xcl666/trackpoint-mechanical-keyboard/PCB/3x10/3D/误差/IMG_2119.JPG

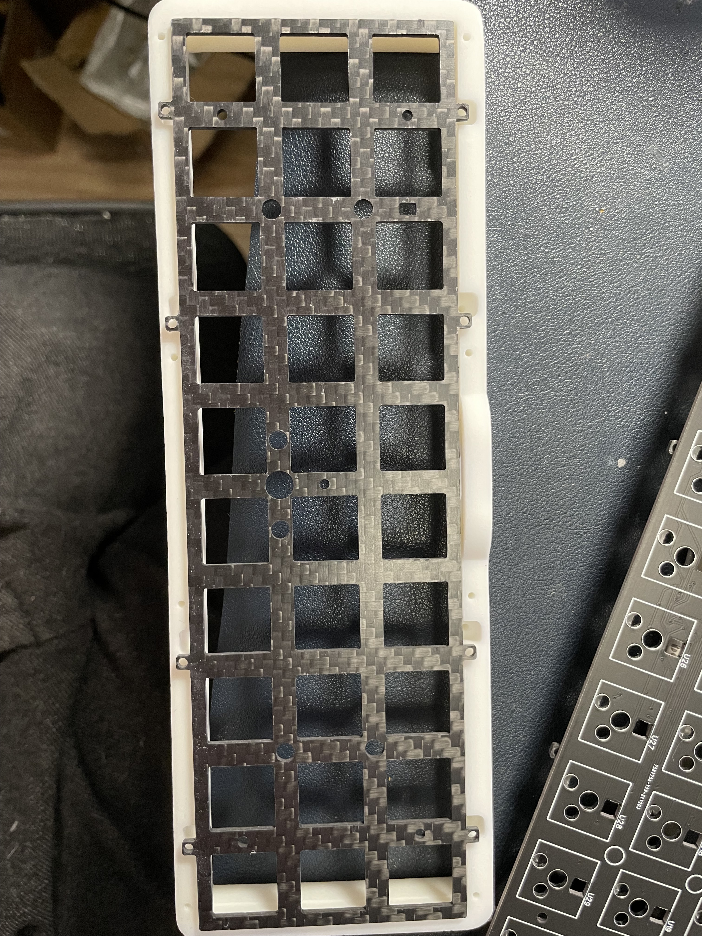
PCB/3x10/3D/误差/IMG_2119.JPG
