xcl666/trackpoint-mechanical-keyboard/PCB/3x10/3D/误差/QQ图片20211208211826.png

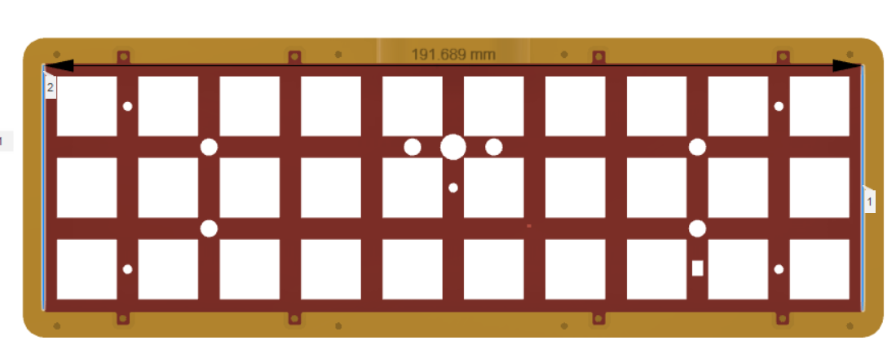
PCB/3x10/3D/误差/QQ图片20211208211826.png
