xcl666/trackpoint-mechanical-keyboard/PCB/3x10/pic/Fo7JxUKhkw28jX1DG1f_OKitPLBH.png

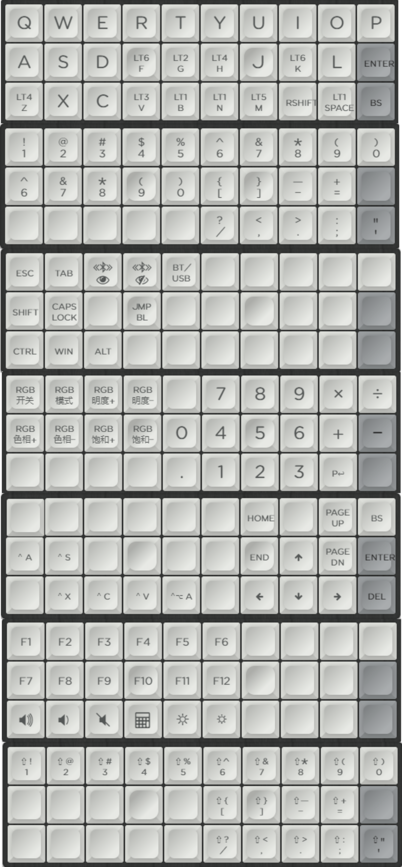
PCB/3x10/pic/Fo7JxUKhkw28jX1DG1f_OKitPLBH.png
