xcl666/trackpoint-mechanical-keyboard/PCB/3x10/pic/IMG_1978(20211202-105650).JPG

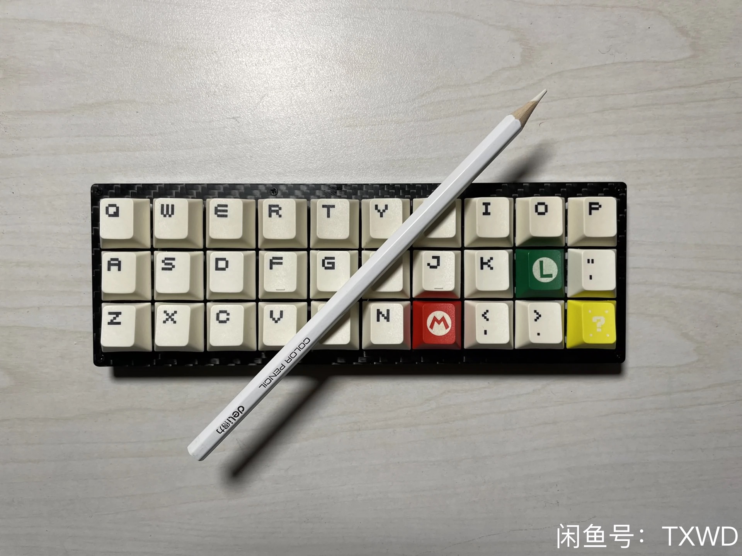
PCB/3x10/pic/IMG_1978(20211202-105650).JPG
