xcl666/trackpoint-mechanical-keyboard/PCB/3x10/pic/IMG_1979(20211202-105653).JPG

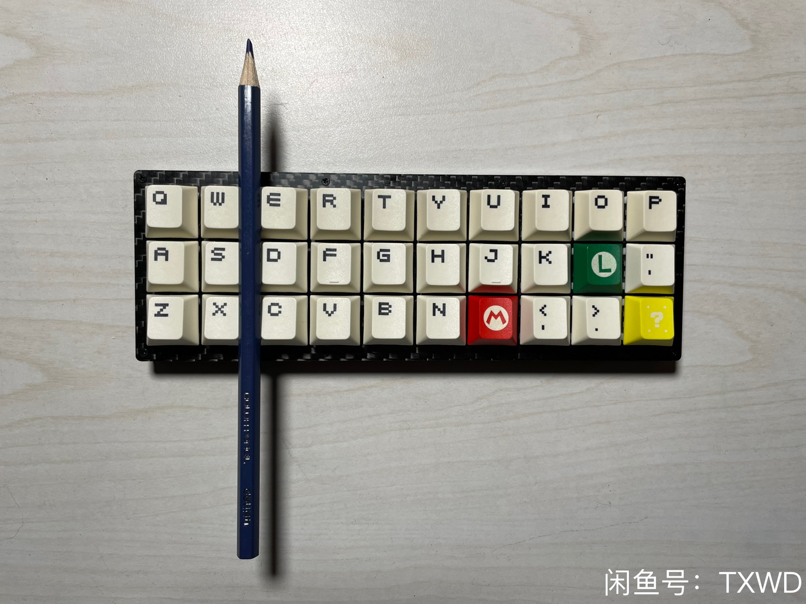
PCB/3x10/pic/IMG_1979(20211202-105653).JPG
