xcl666/trackpoint-mechanical-keyboard/PCB/3x10/pic/IMG_1980(20211202-105657).JPG

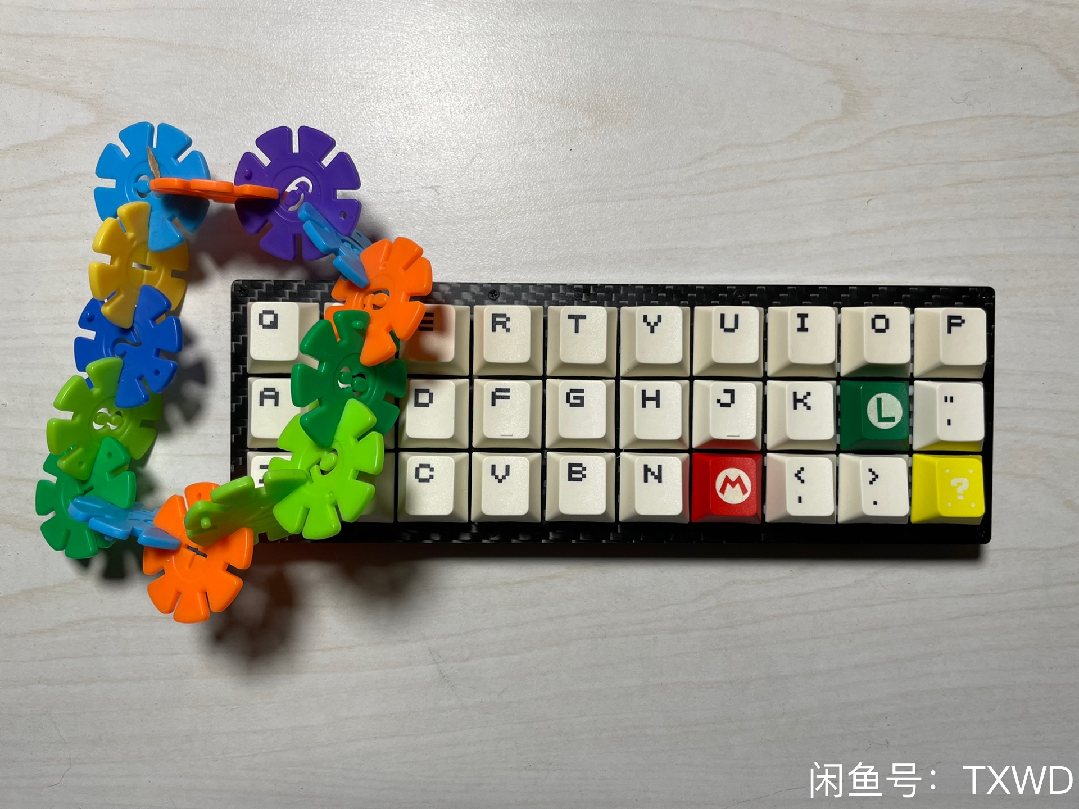
PCB/3x10/pic/IMG_1980(20211202-105657).JPG
