xcl666/trackpoint-mechanical-keyboard/PCB/3x10/pic/IMG_1981(20211202-105700).JPG

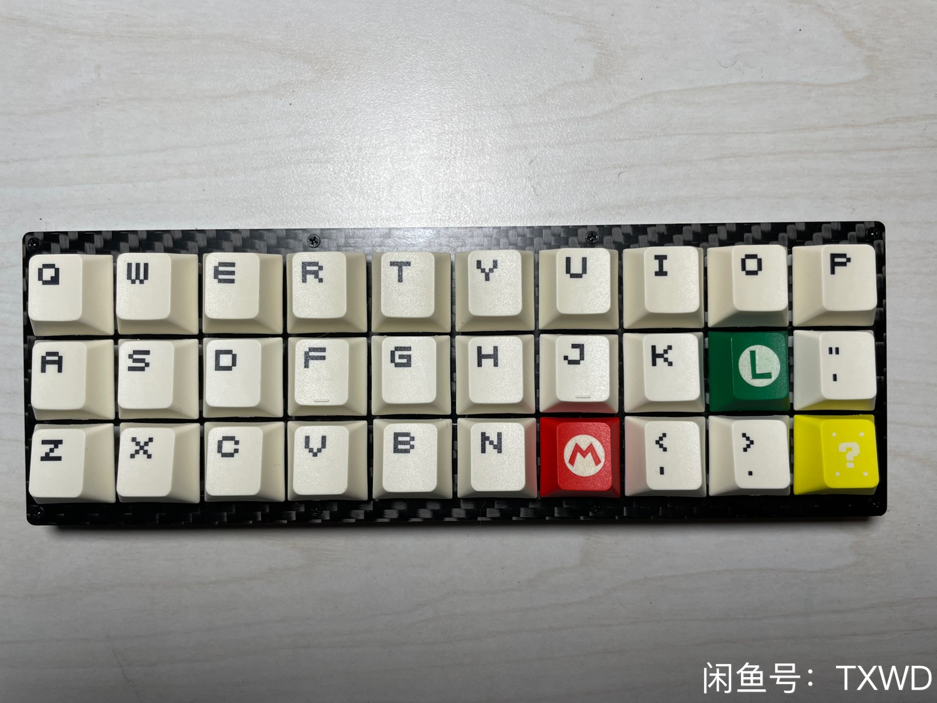
PCB/3x10/pic/IMG_1981(20211202-105700).JPG
