xcl666/trackpoint-mechanical-keyboard/PCB/3x10/pic/IMG_1982(20211202-105706).JPG

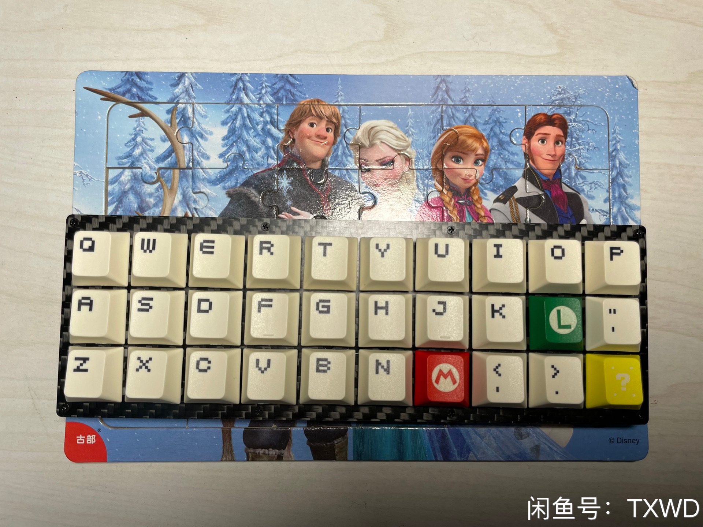
PCB/3x10/pic/IMG_1982(20211202-105706).JPG
