xcl666/trackpoint-mechanical-keyboard/PCB/3x10/pic/IMG_1983(20211202-105742).JPG

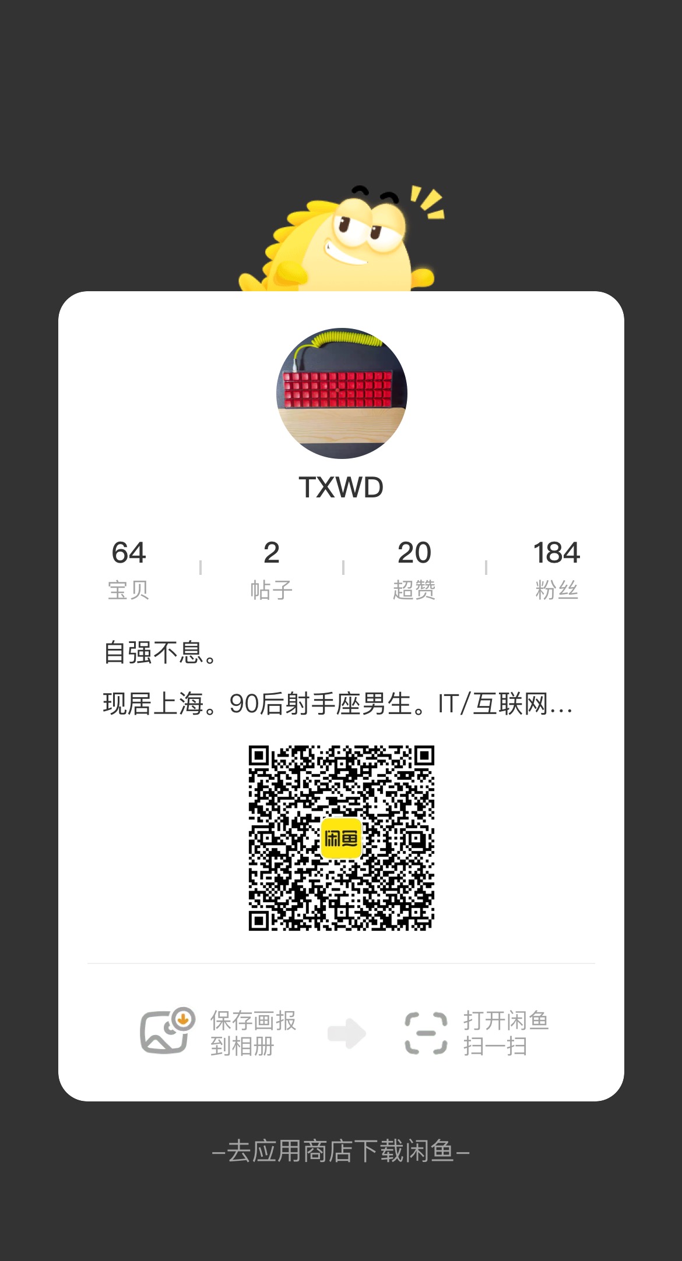
PCB/3x10/pic/IMG_1983(20211202-105742).JPG
