xcl666/trackpoint-mechanical-keyboard/PCB/3x10/QQ图片20211215133456.png

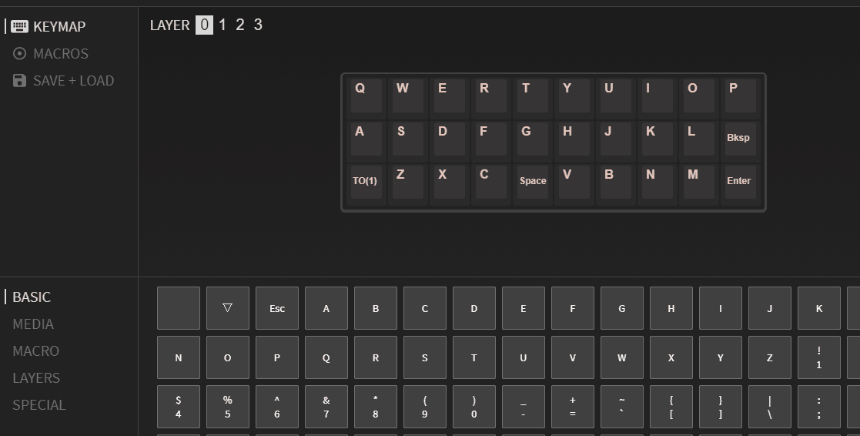
PCB/3x10/QQ图片20211215133456.png
