xcl666/trackpoint-mechanical-keyboard/PCB/4x14/pic/IMG_1932(20211130-000232).JPG

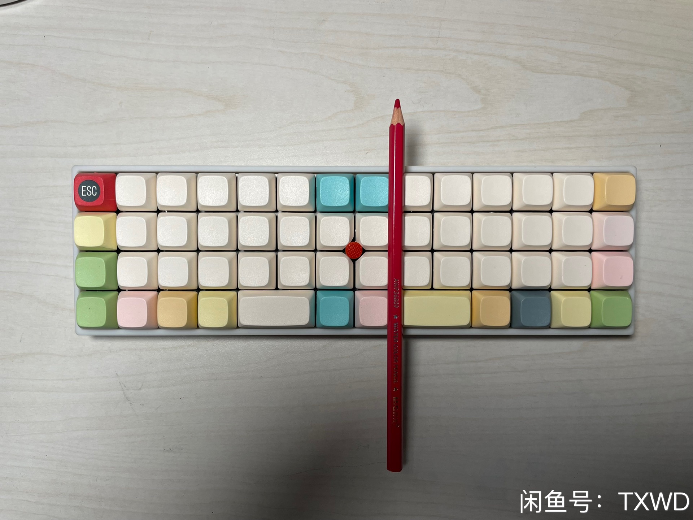
PCB/4x14/pic/IMG_1932(20211130-000232).JPG
