xcl666/trackpoint-mechanical-keyboard/PCB/4x14/pic/IMG_1933(20211130-000236).JPG

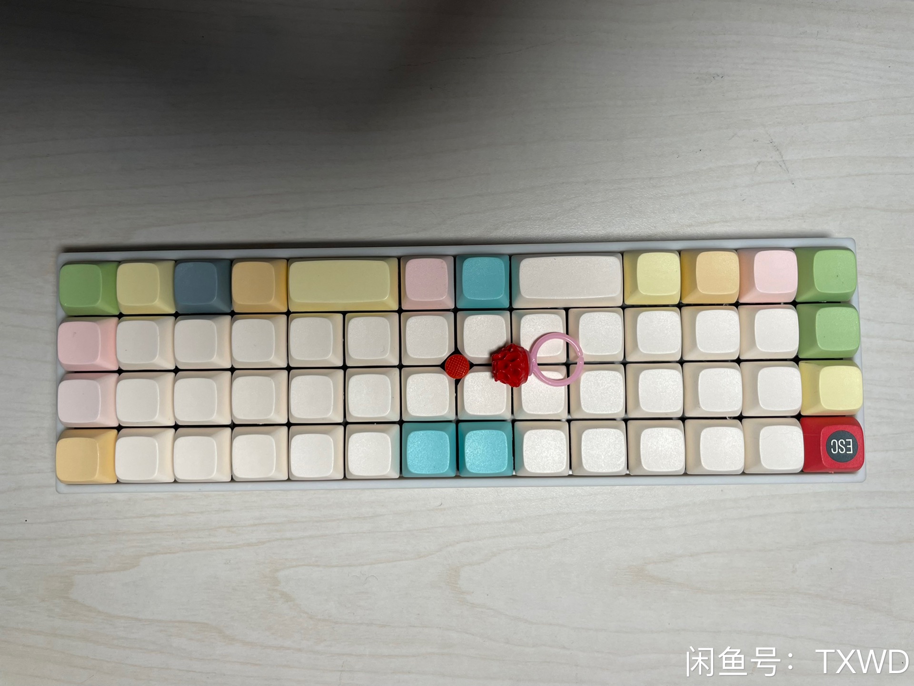
PCB/4x14/pic/IMG_1933(20211130-000236).JPG
