xcl666/trackpoint-mechanical-keyboard/PCB/4x14/pic/IMG_1934(20211130-000239).JPG

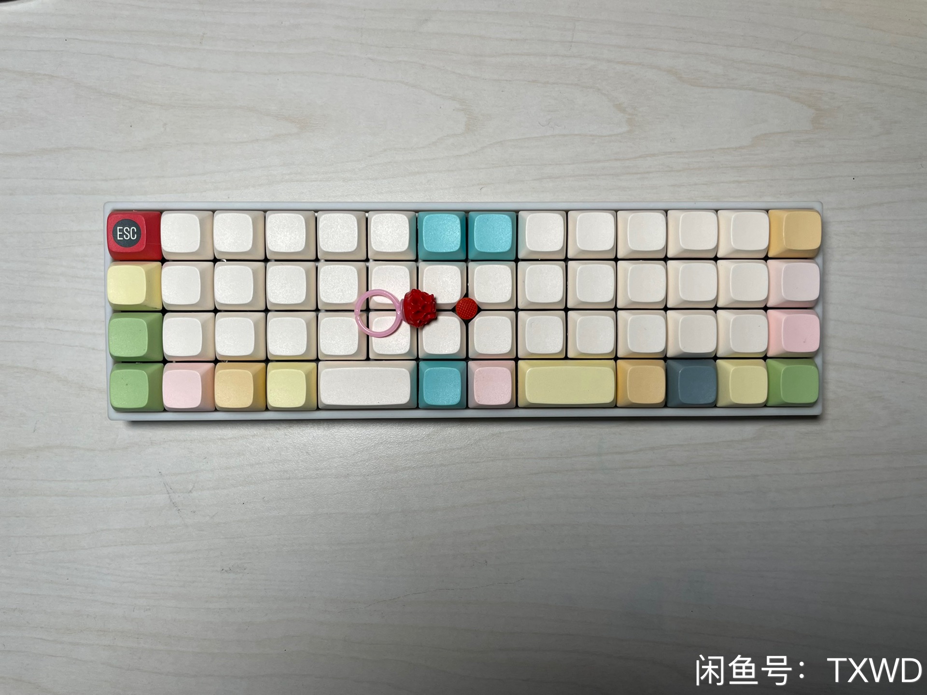
PCB/4x14/pic/IMG_1934(20211130-000239).JPG
