xcl666/trackpoint-mechanical-keyboard/PCB/4x14/pic/IMG_1935(20211130-000242).JPG

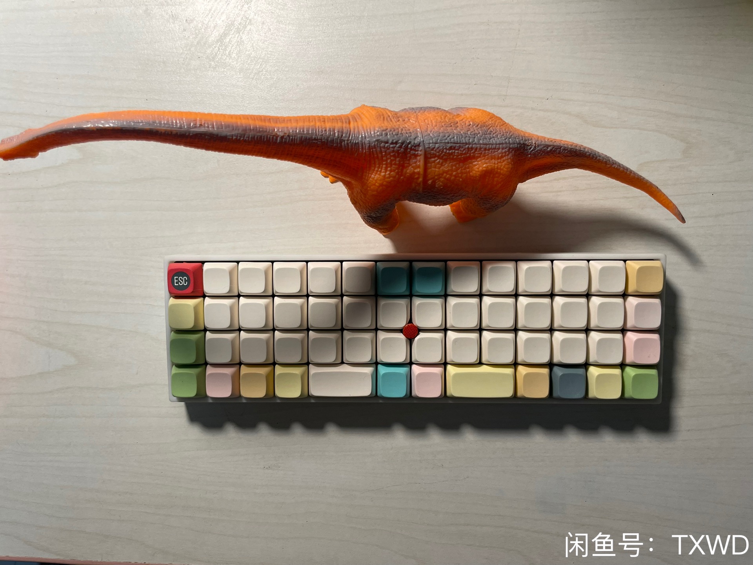
PCB/4x14/pic/IMG_1935(20211130-000242).JPG
