xcl666/trackpoint-mechanical-keyboard/PCB/4x14/pic/IMG_1936(20211130-000251).JPG

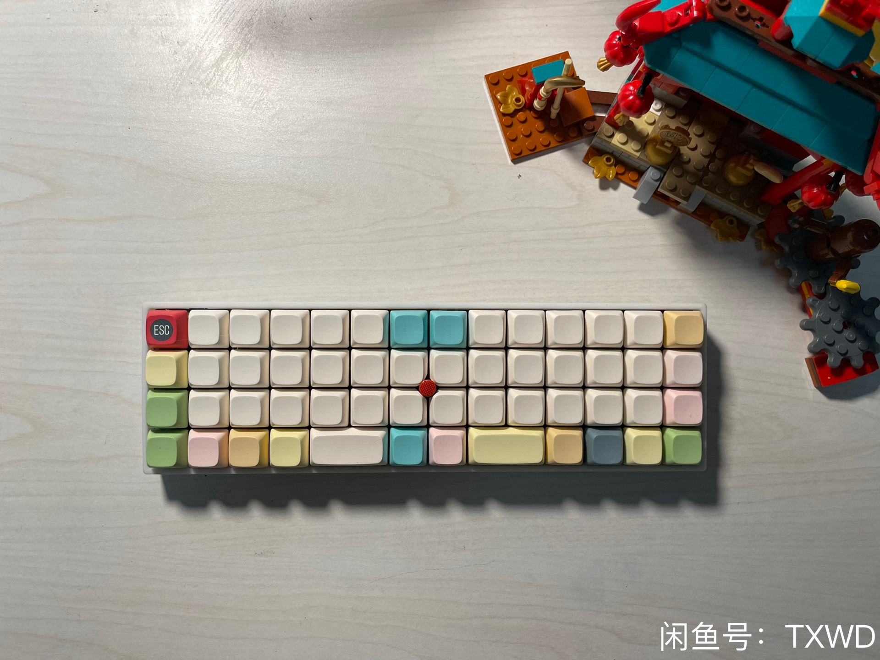
PCB/4x14/pic/IMG_1936(20211130-000251).JPG
