xcl666/trackpoint-mechanical-keyboard/PCB/4x14/pic/IMG_1937(20211130-000254).JPG

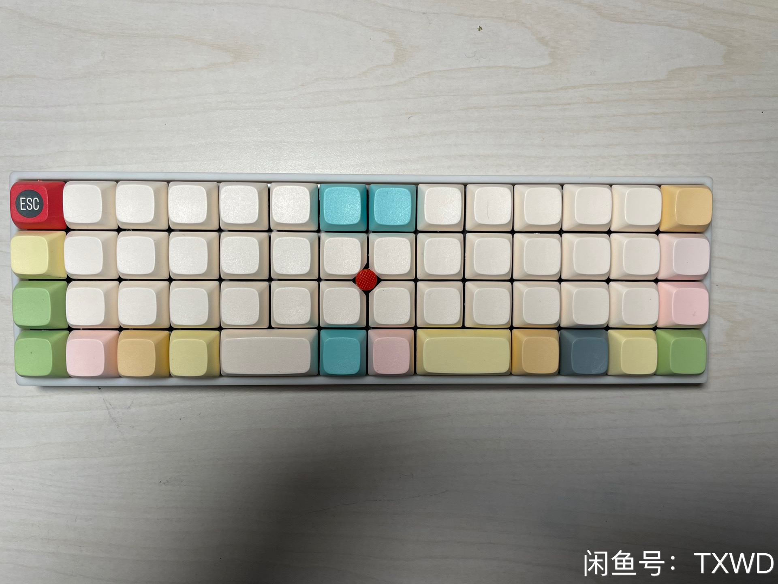
PCB/4x14/pic/IMG_1937(20211130-000254).JPG
