xcl666/trackpoint-mechanical-keyboard/PCB/4x14/pic/IMG_1938(20211130-000258).JPG

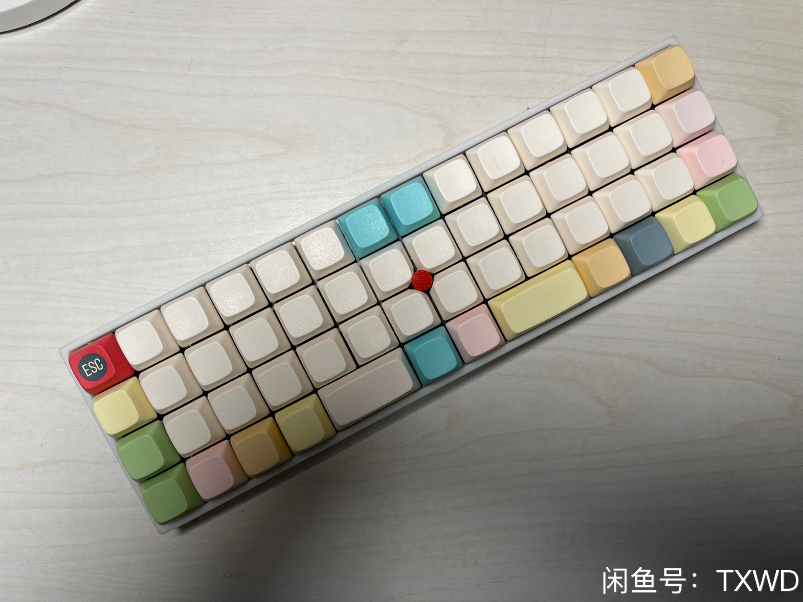
PCB/4x14/pic/IMG_1938(20211130-000258).JPG
