xcl666/trackpoint-mechanical-keyboard/PCB/4x14/pic/IMG_1939(20211130-000301).JPG

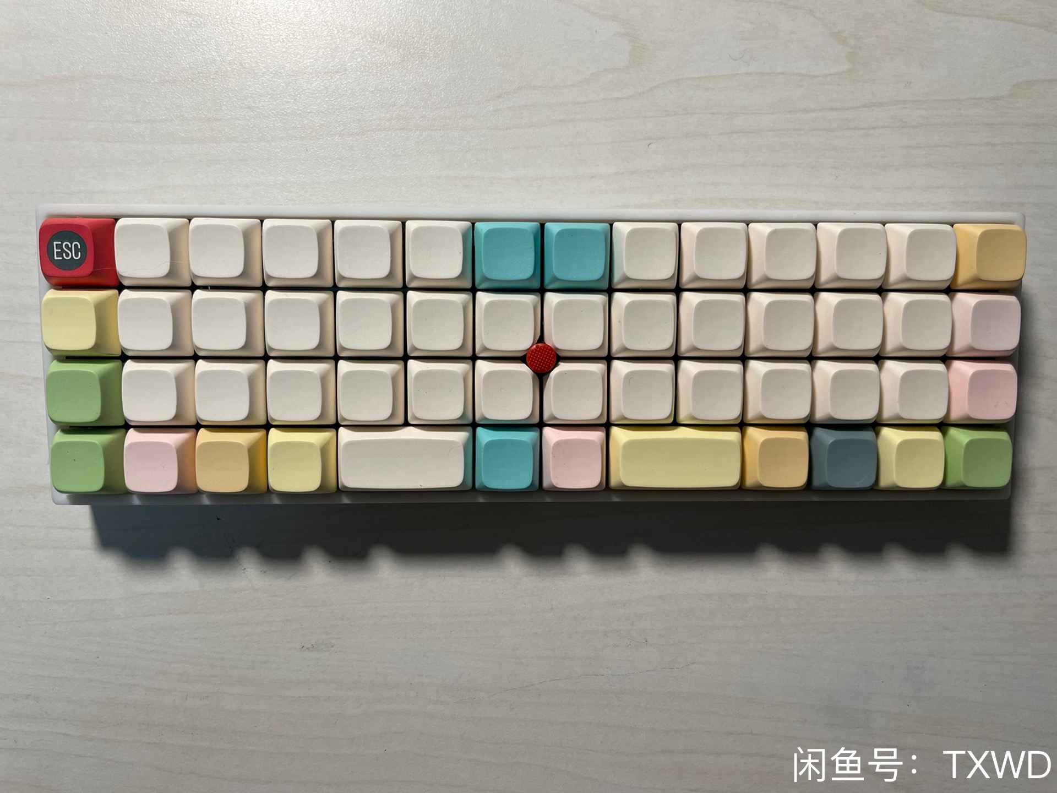
PCB/4x14/pic/IMG_1939(20211130-000301).JPG
