xcl666/trackpoint-mechanical-keyboard/PCB/alice/3D/myown/WeChat Image_20220102115507.png

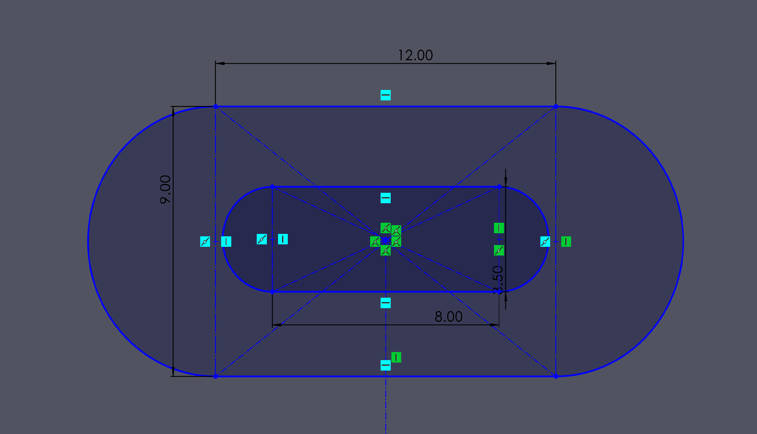
PCB/alice/3D/myown/WeChat Image_20220102115507.png
