xcl666/trackpoint-mechanical-keyboard/PCB/alice/60alicetp.png

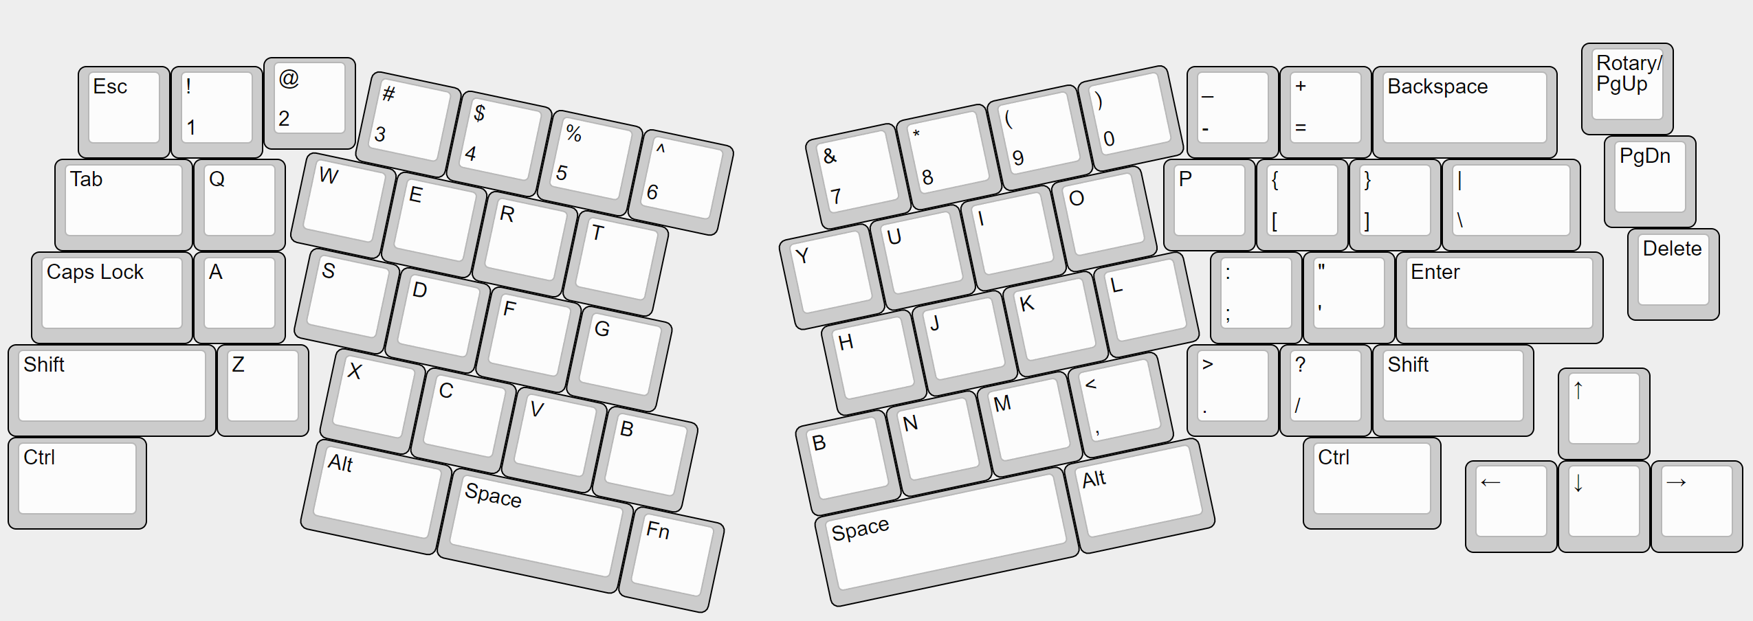
PCB/alice/60alicetp.png
