xcl666/trackpoint-mechanical-keyboard/PCB/alice/70alicetp.png

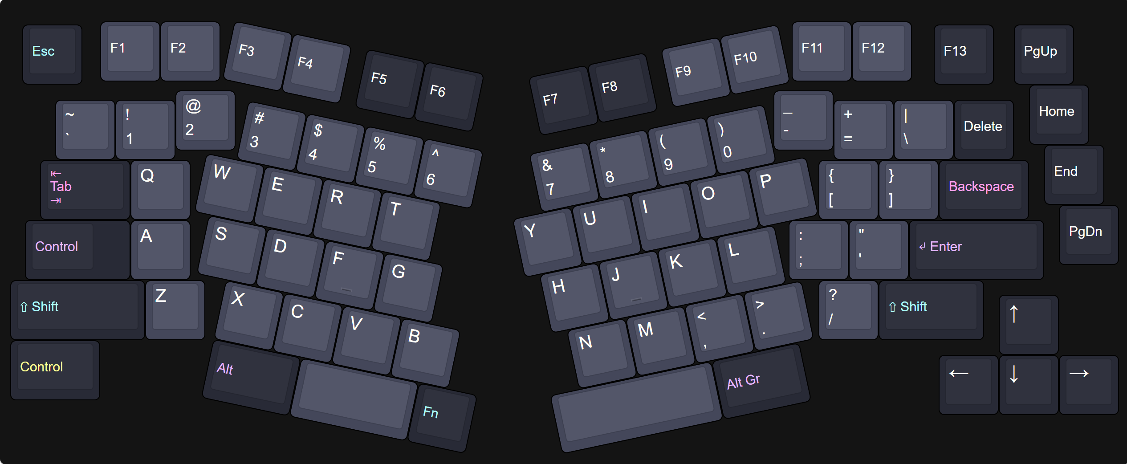
PCB/alice/70alicetp.png
