xcl666/trackpoint-mechanical-keyboard/PCB/alice/Fm2w5G8_fELwdBUXXY6CFaClQVQb.png

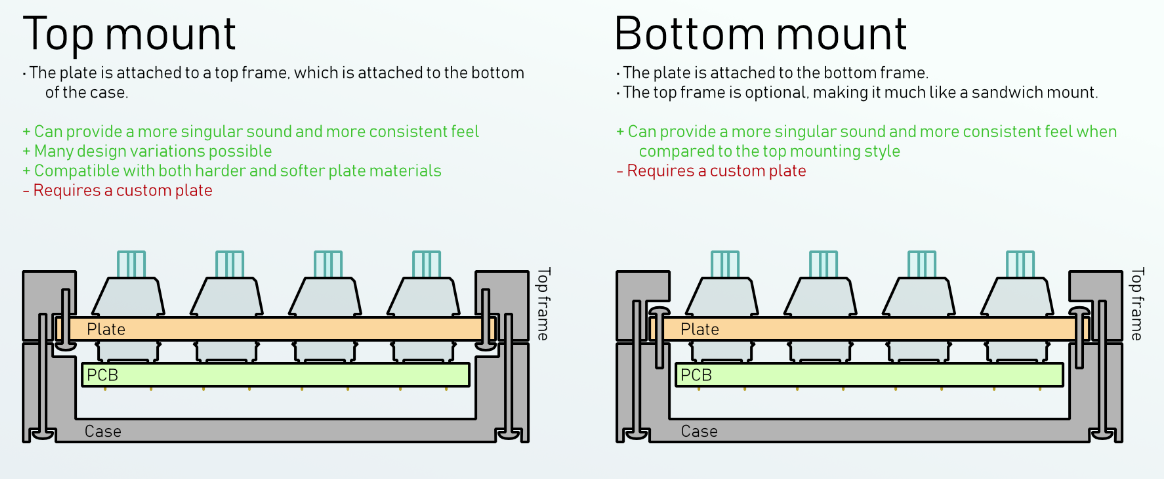
PCB/alice/Fm2w5G8_fELwdBUXXY6CFaClQVQb.png
