xcl666/trackpoint-mechanical-keyboard/PCB/alice/InkedQQ图片20211125203827.jpg

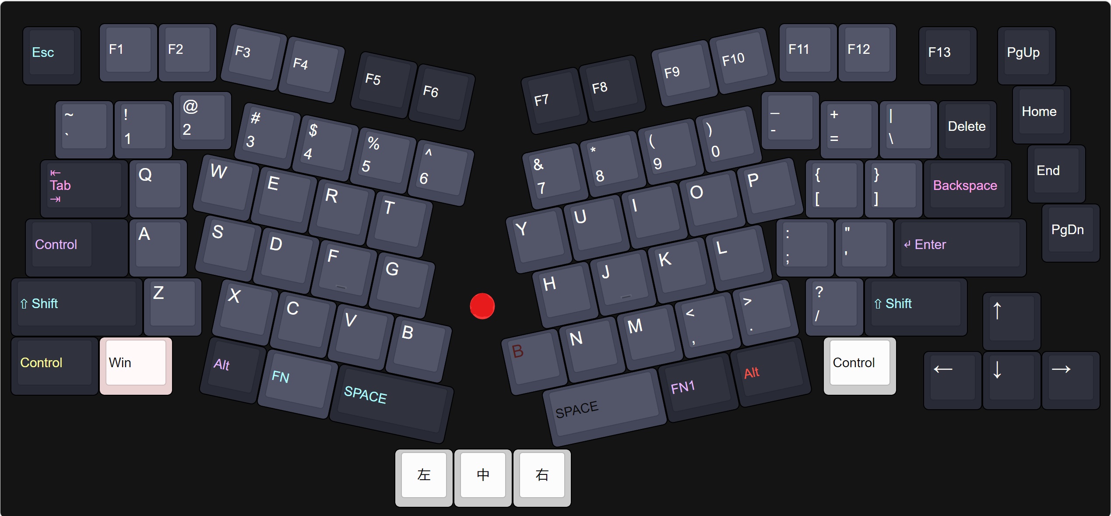
PCB/alice/InkedQQ图片20211125203827.jpg
