xcl666/trackpoint-mechanical-keyboard/PCB/alice/lastAlice.png

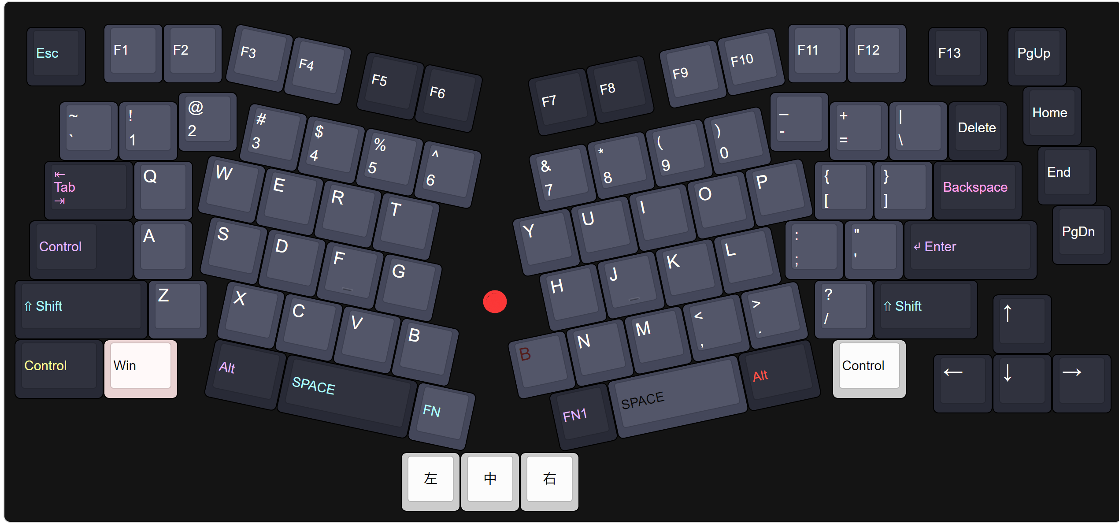
PCB/alice/lastAlice.png
