xcl666/trackpoint-mechanical-keyboard/PCB/alice/QQ图片20211125215850.jpg

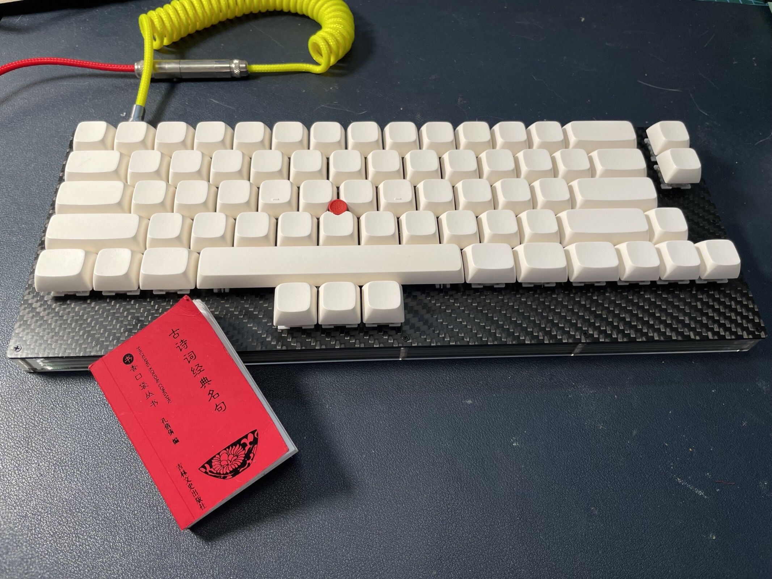
PCB/alice/QQ图片20211125215850.jpg
