xcl666/trackpoint-mechanical-keyboard/PCB/alice/QQ图片20211125220050.png

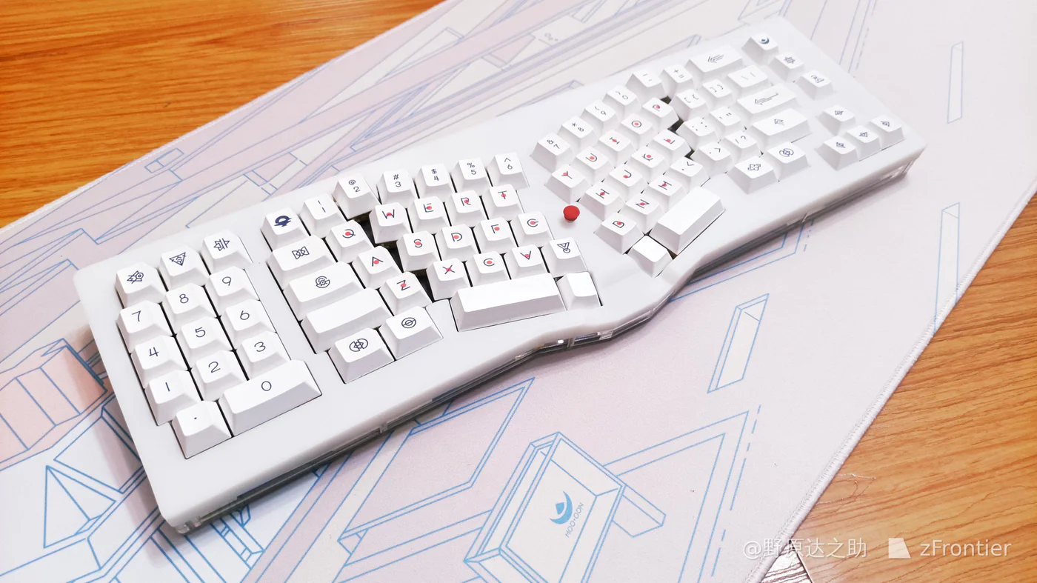
PCB/alice/QQ图片20211125220050.png
