xcl666/trackpoint-mechanical-keyboard/PCB/alice/QQ图片20211127194925.jpg

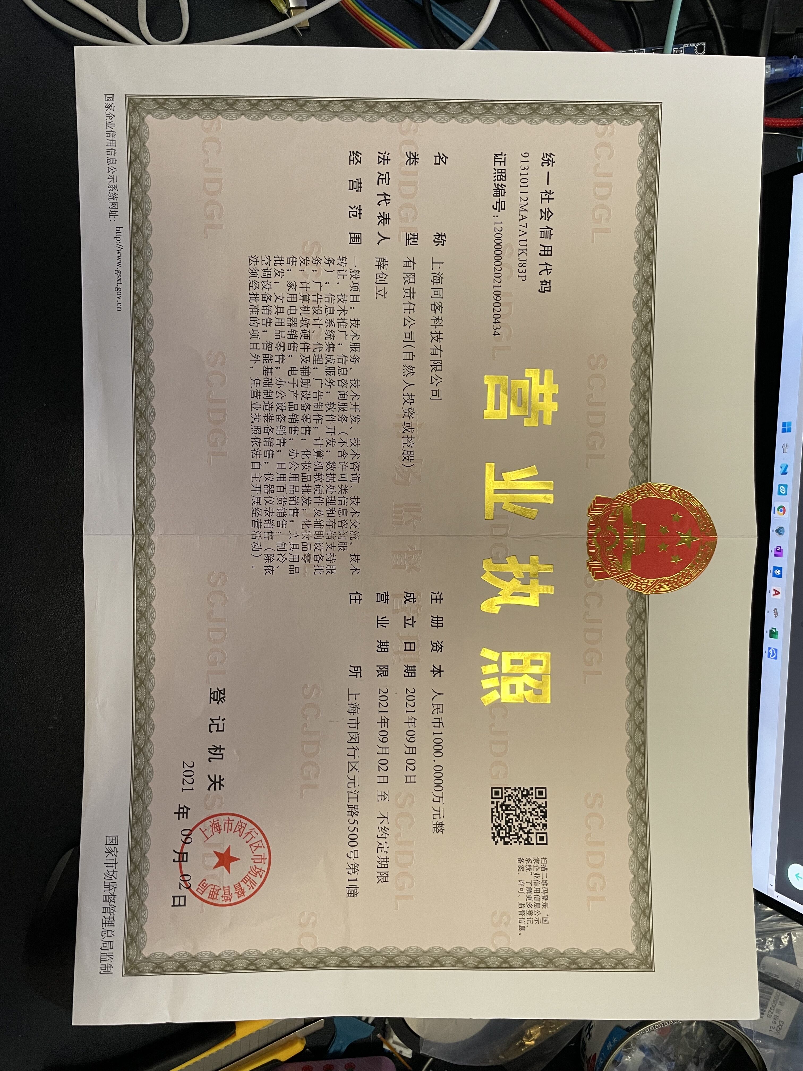
PCB/alice/QQ图片20211127194925.jpg
