xcl666/trackpoint-mechanical-keyboard/PCB/alice/QQ图片20211215164015.jpg

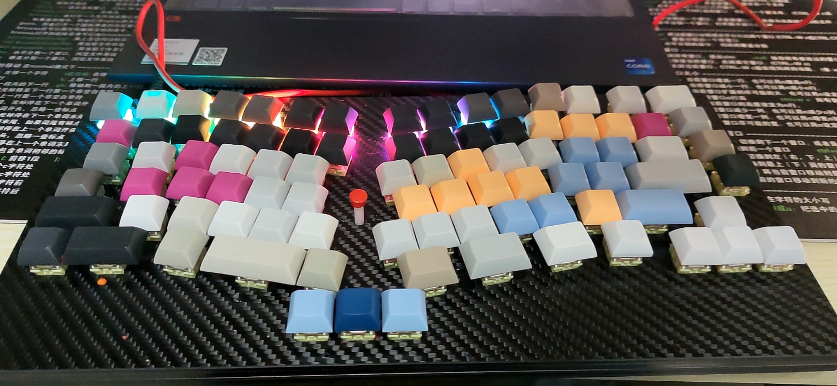
PCB/alice/QQ图片20211215164015.jpg
