xcl666/trackpoint-mechanical-keyboard/PCB/alice/WeChat Image_20211124023521.png

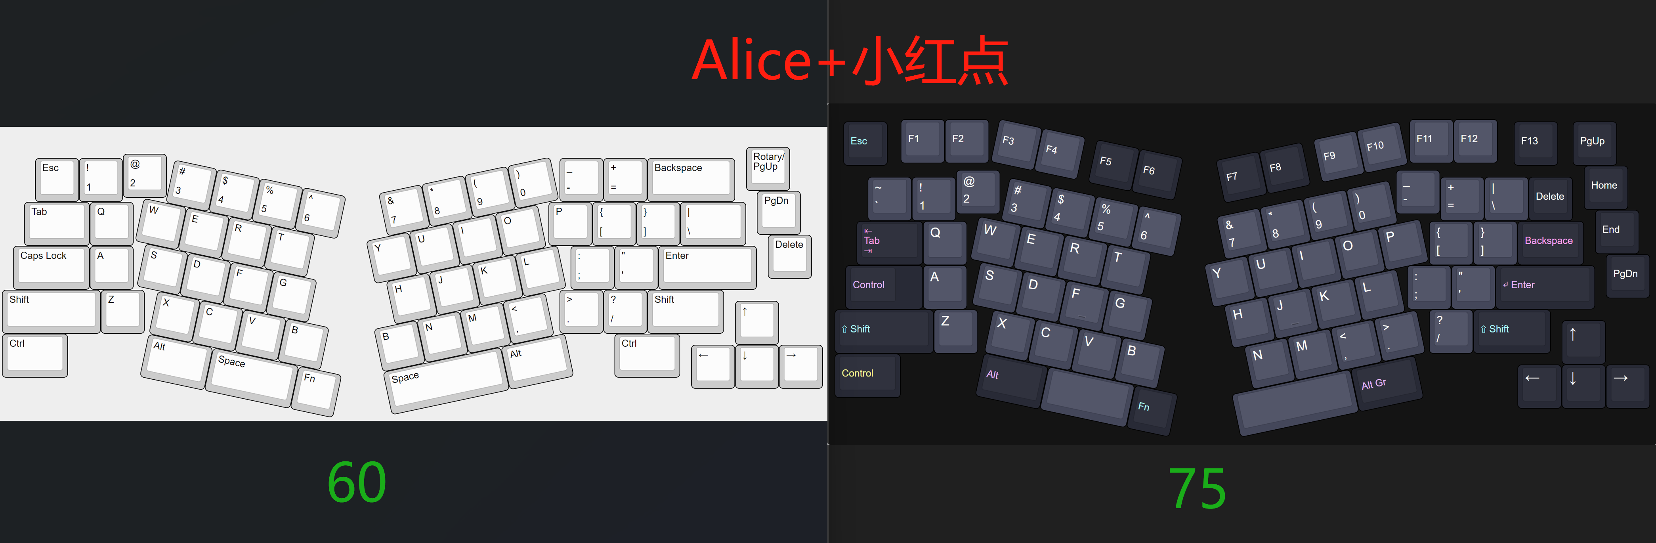
PCB/alice/WeChat Image_20211124023521.png
