xcl666/trackpoint-mechanical-keyboard/PCB/alice/WeChat Image_20211125122409.jpg

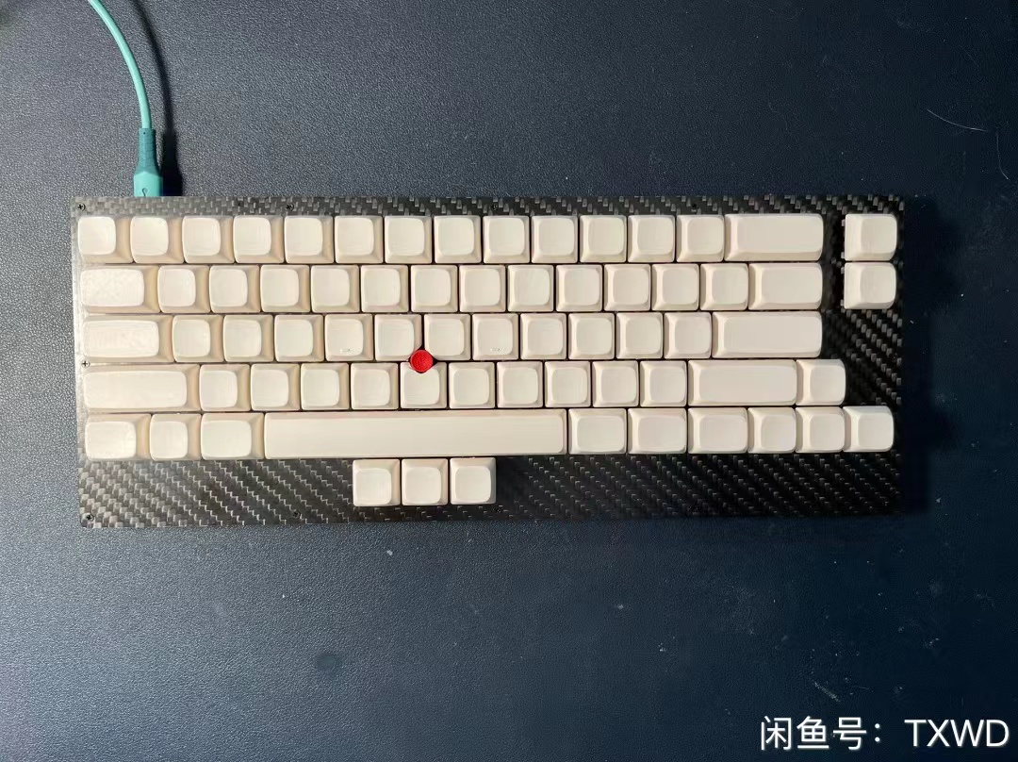
PCB/alice/WeChat Image_20211125122409.jpg
