xcl666/trackpoint-mechanical-keyboard/PCB/alice/WeChat Image_20211211230742.jpg

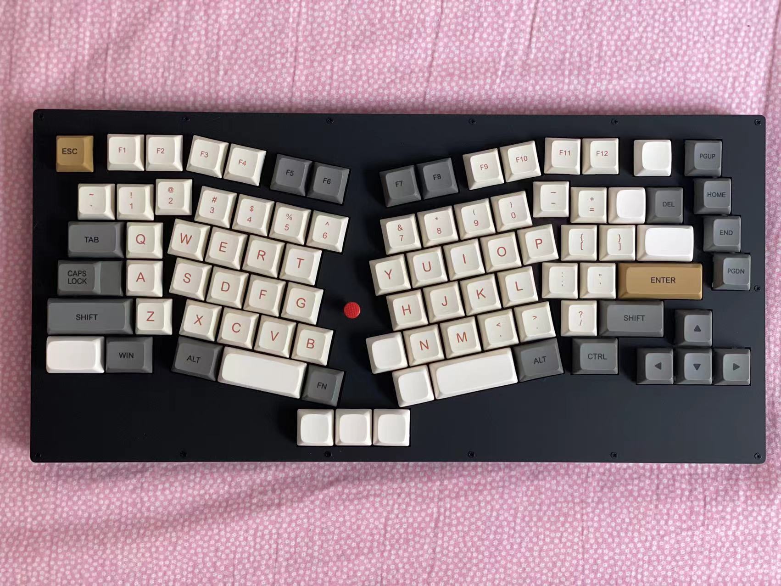
PCB/alice/WeChat Image_20211211230742.jpg
