xcl666/trackpoint-mechanical-keyboard/PCB/alice/选购配件.png

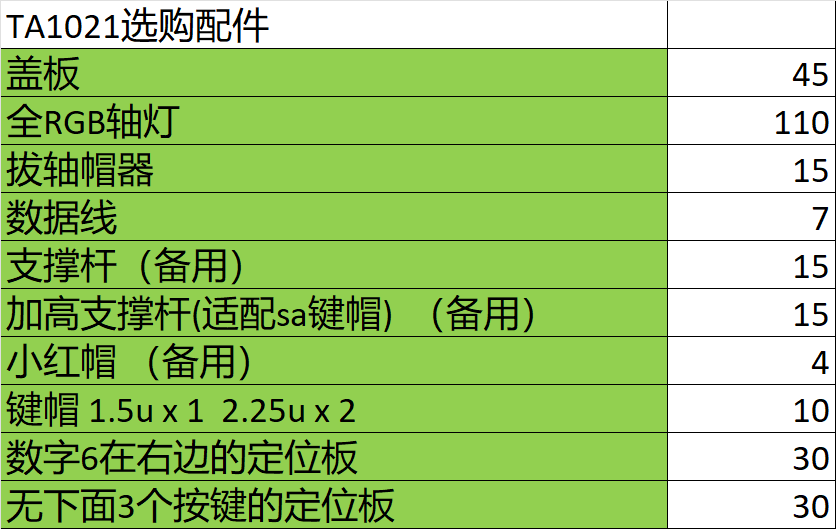
PCB/alice/选购配件.png
