xcl666/trackpoint-mechanical-keyboard/PCB/at90usb646/schematic2pp.png

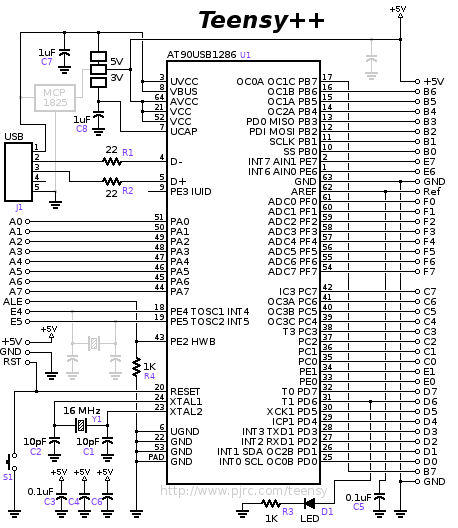
PCB/at90usb646/schematic2pp.png
