xcl666/trackpoint-mechanical-keyboard/PCB/think48/14652E1B-F07E-4A99-99C1-B11ADDA51B1B(1).JPG

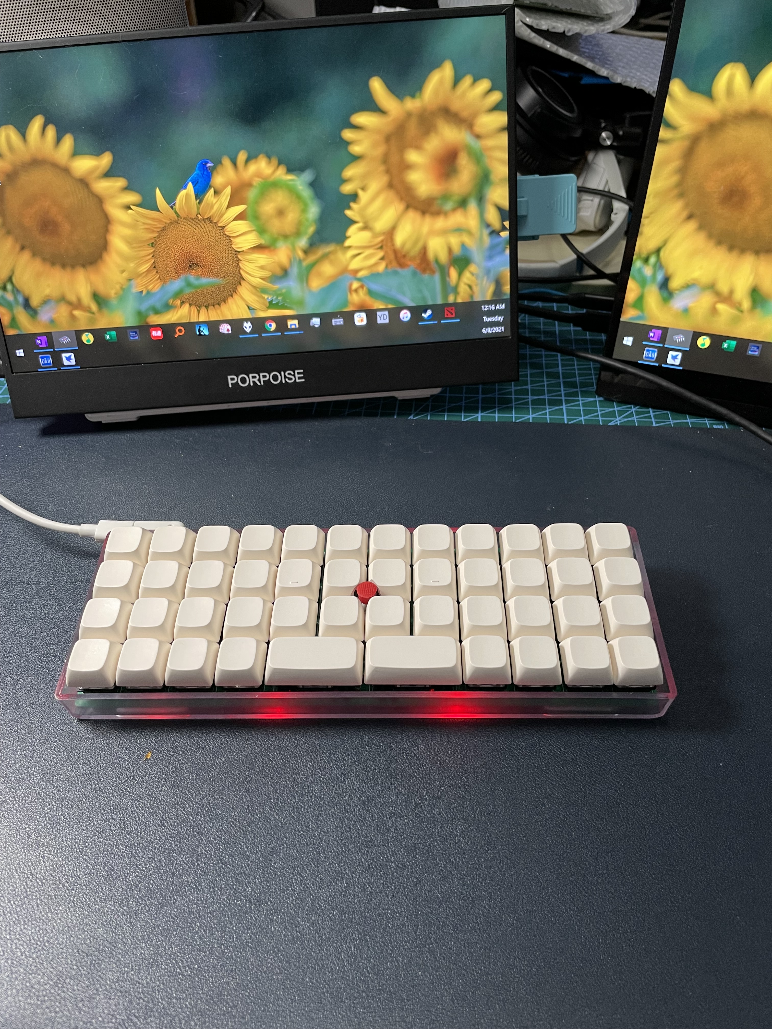
PCB/think48/14652E1B-F07E-4A99-99C1-B11ADDA51B1B(1).JPG
