xcl666/trackpoint-mechanical-keyboard/PCB/think48/EF5D5C7B-043F-4552-9306-83972699D2C9.JPG

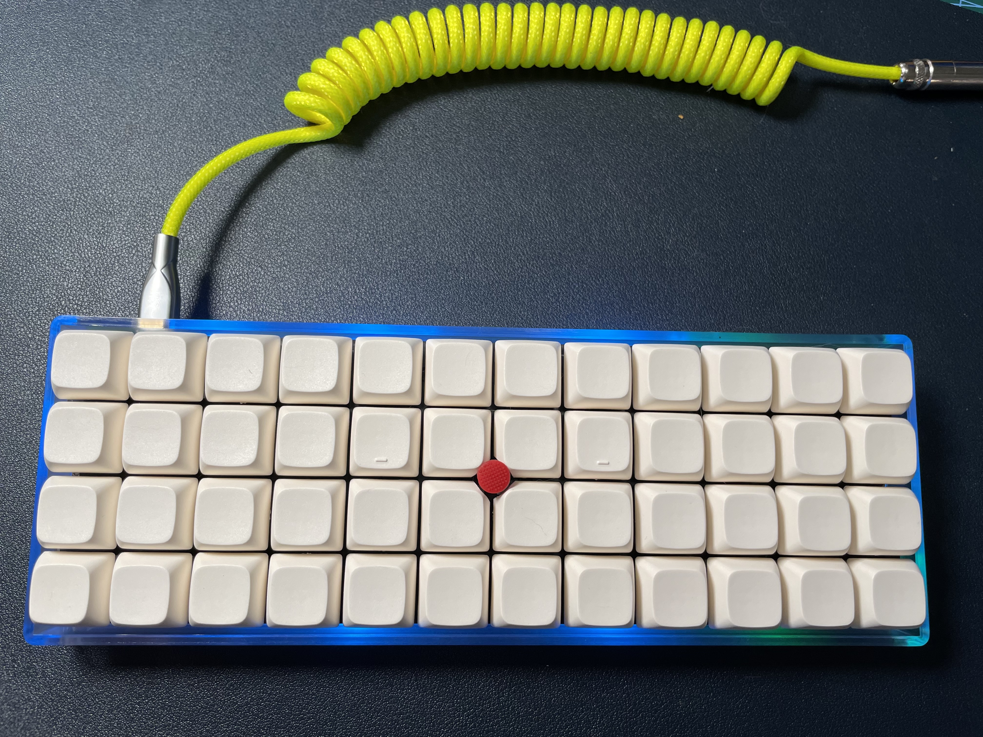
PCB/think48/EF5D5C7B-043F-4552-9306-83972699D2C9.JPG
