xcl666/trackpoint-mechanical-keyboard/PCB/think48/IMG_0189.JPG

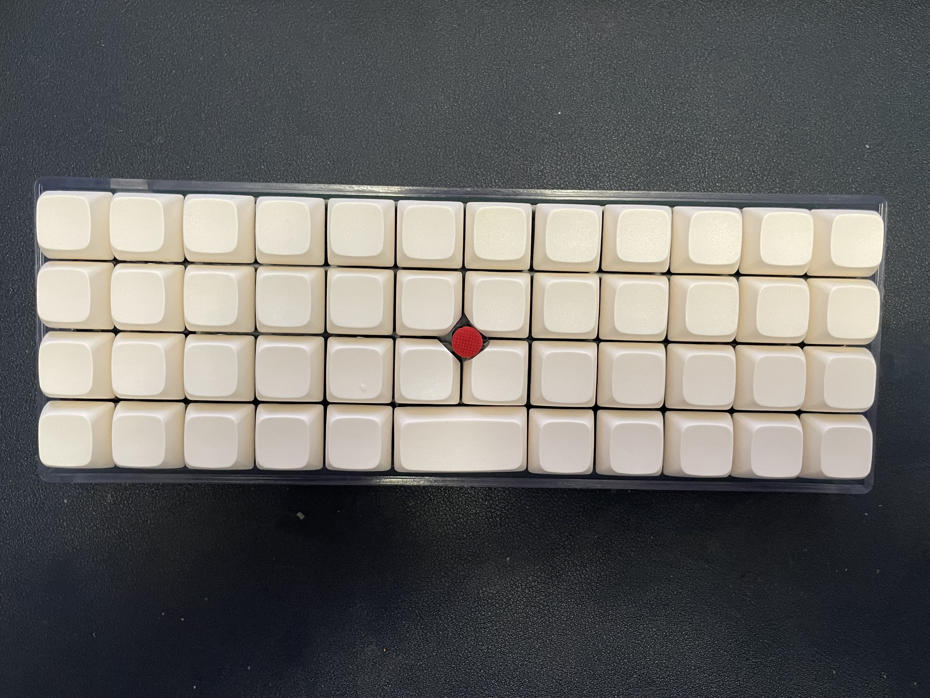
PCB/think48/IMG_0189.JPG
