xcl666/trackpoint-mechanical-keyboard/PCB/think48/IMG_1899(20211126-221744).JPG

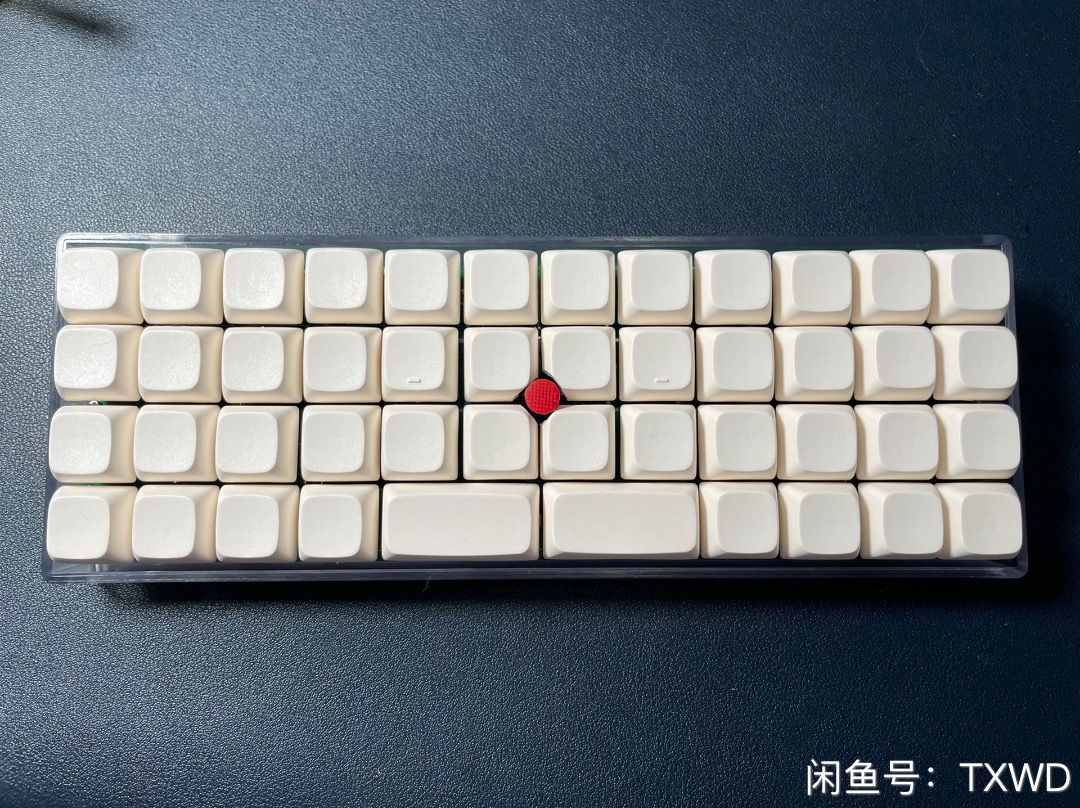
PCB/think48/IMG_1899(20211126-221744).JPG
