xcl666/trackpoint-mechanical-keyboard/PCB/think48/IMG_2052(20220107-030827).JPG

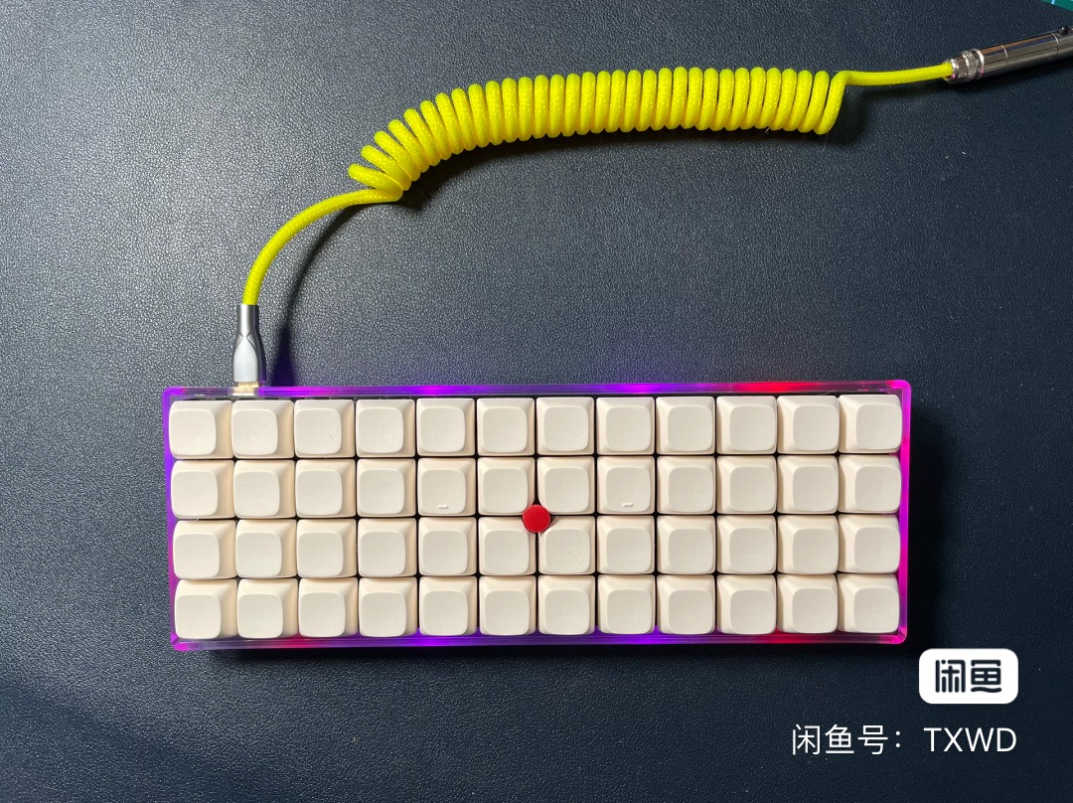
PCB/think48/IMG_2052(20220107-030827).JPG
