xcl666/trackpoint-mechanical-keyboard/PCB/think48/IMG_2998.JPG

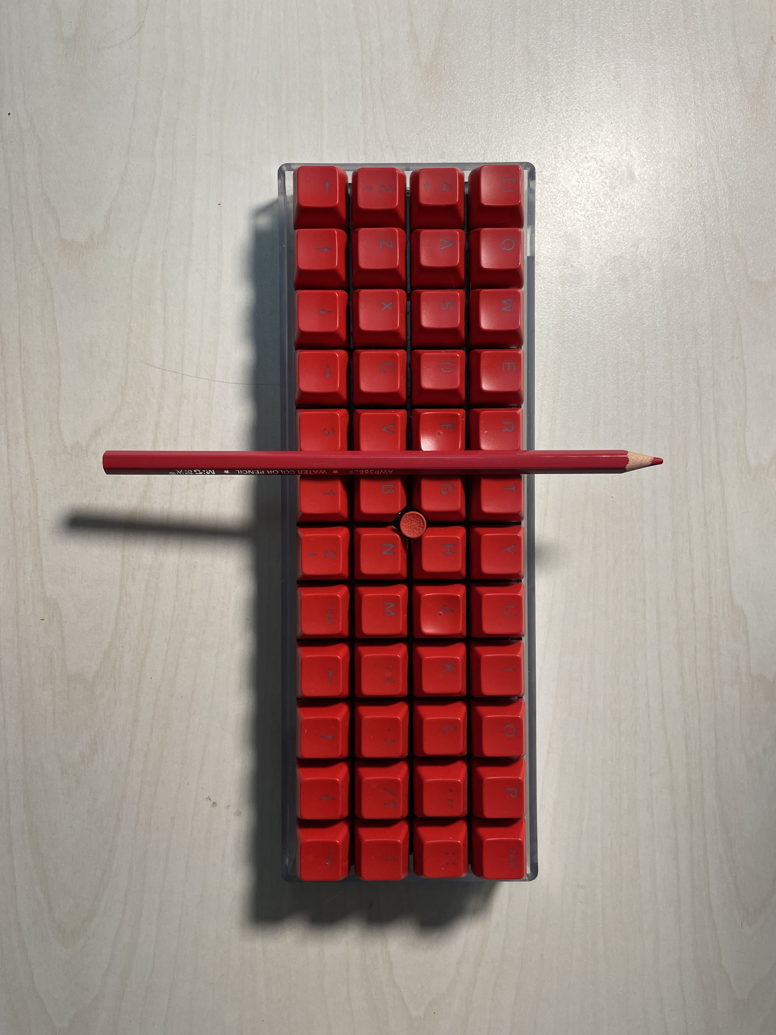
PCB/think48/IMG_2998.JPG
