xcl666/trackpoint-mechanical-keyboard/PCB/think48/new/WeChat Image_20220222152111.jpg

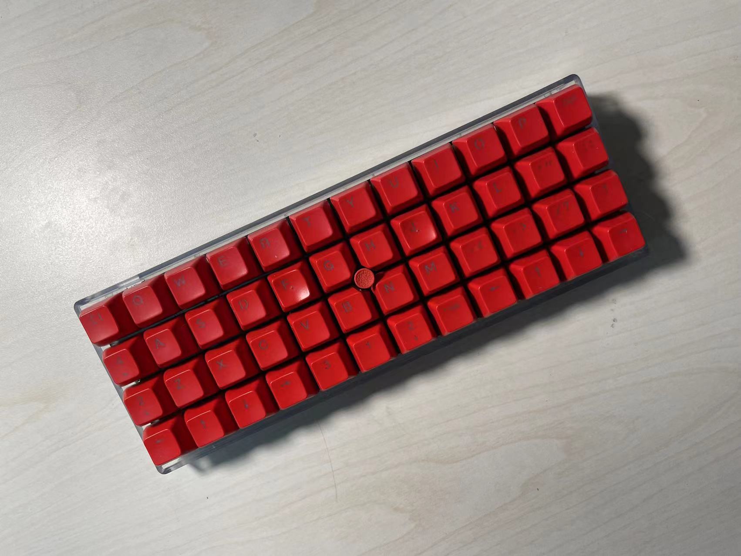
PCB/think48/new/WeChat Image_20220222152111.jpg
