xcl666/trackpoint-mechanical-keyboard/PCB/think48/new/WeChat Image_202202221521092.jpg

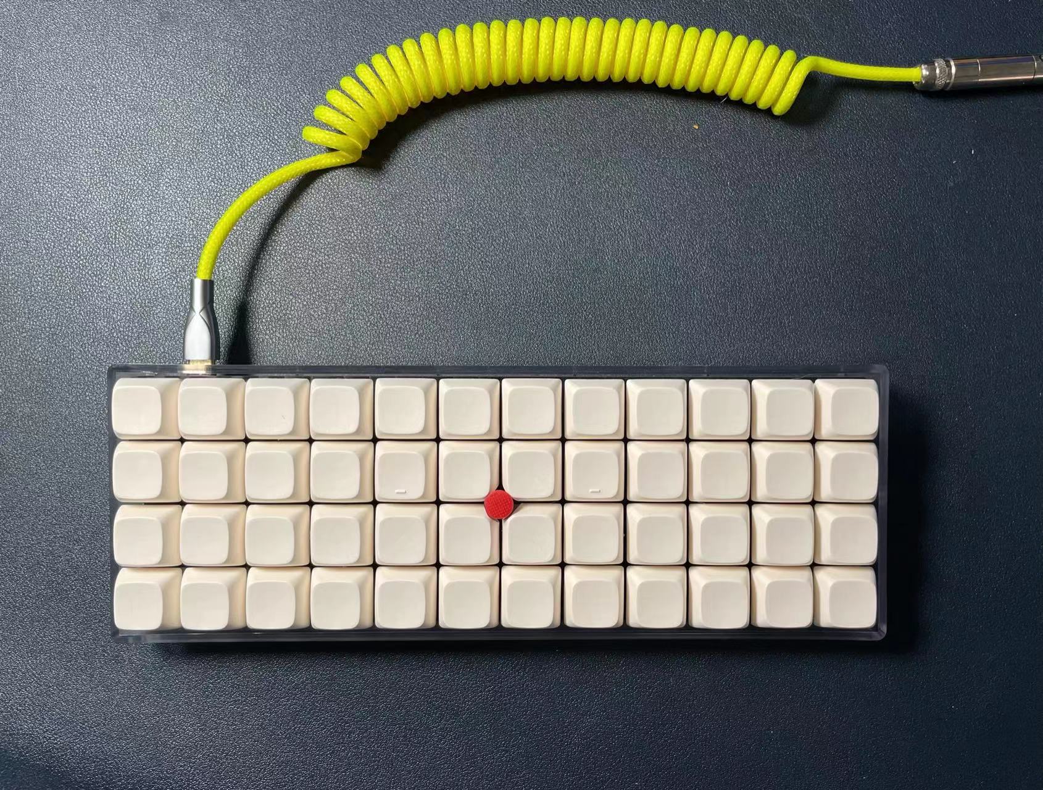
PCB/think48/new/WeChat Image_202202221521092.jpg
