xcl666/trackpoint-mechanical-keyboard/PCB/think48/new/WeChat Image_202202221521093.jpg

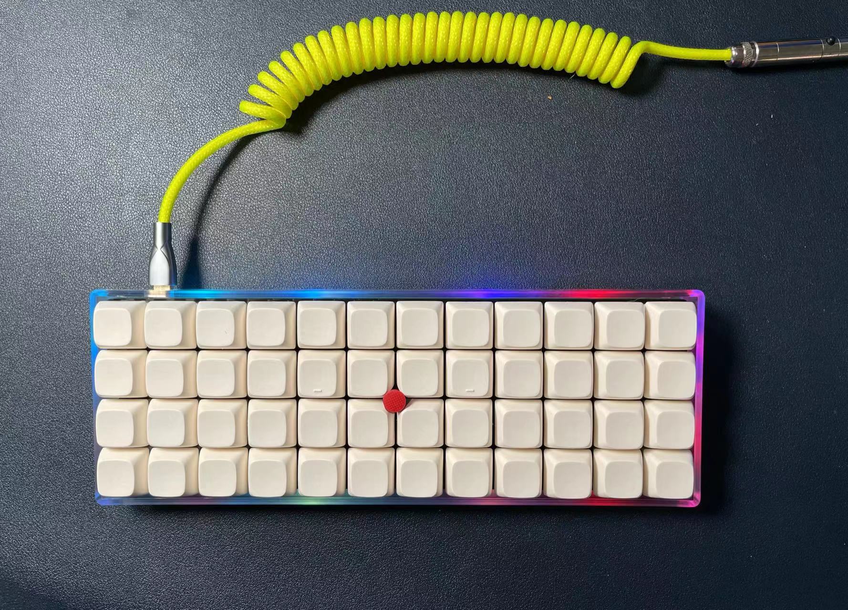
PCB/think48/new/WeChat Image_202202221521093.jpg
