xcl666/trackpoint-mechanical-keyboard/PCB/think48/new/WeChat Image_202202221521102.jpg

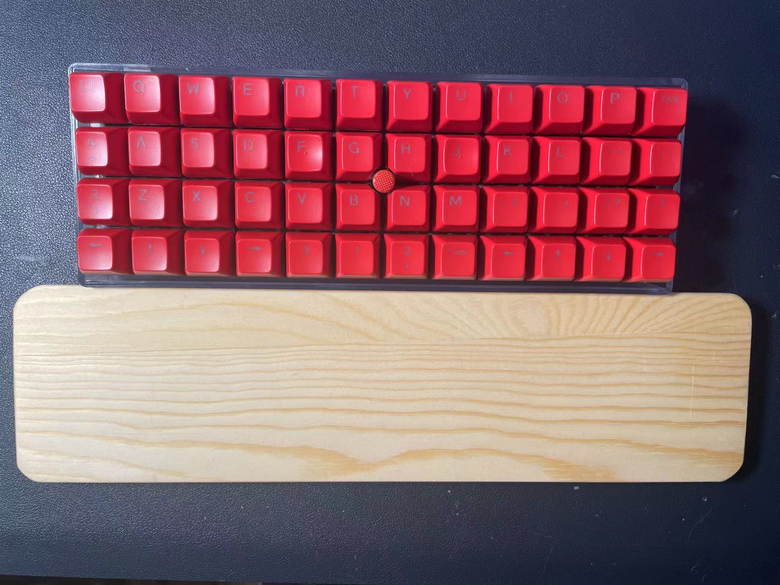
PCB/think48/new/WeChat Image_202202221521102.jpg
