xcl666/trackpoint-mechanical-keyboard/PCB/think48/new/WeChat Image_202202221521111.jpg

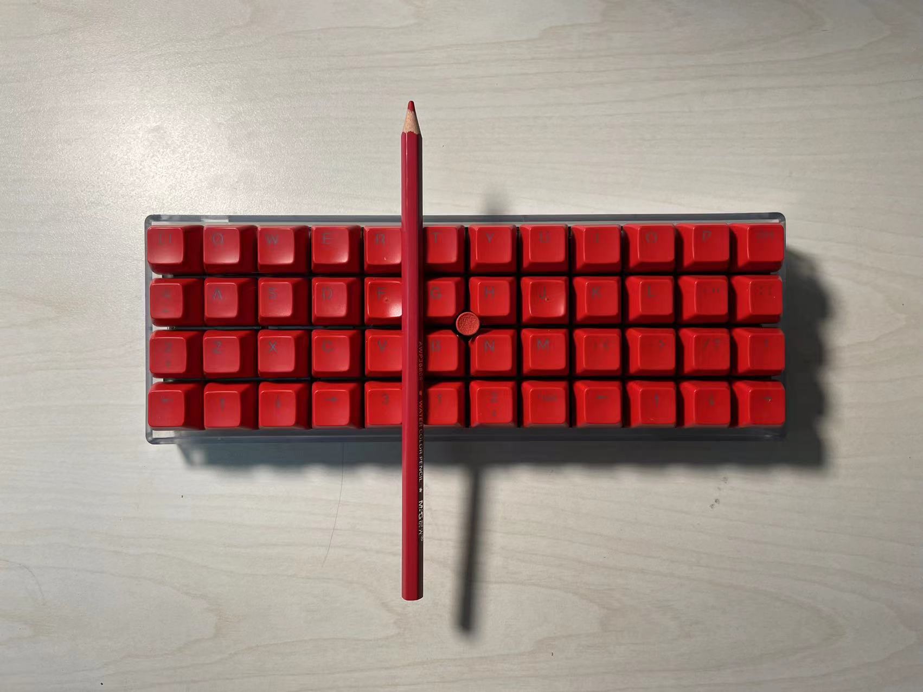
PCB/think48/new/WeChat Image_202202221521111.jpg
