xcl666/trackpoint-mechanical-keyboard/PCB/think84/7月28日开源文件/7月28日开源文件/高清键盘图/computer-1209104_1920.jpg

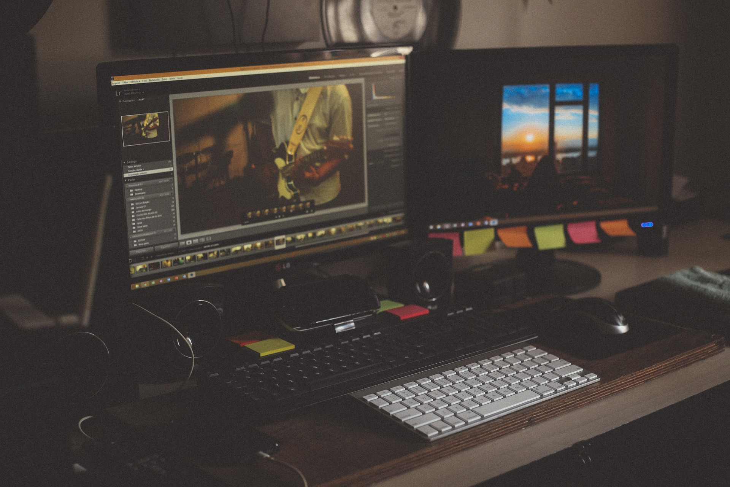
PCB/think84/7月28日开源文件/7月28日开源文件/高清键盘图/computer-1209104_1920.jpg
