xcl666/trackpoint-mechanical-keyboard/PCB/think84/7月28日开源文件/7月28日开源文件/高清键盘图/musical-instrument-1865597_1920.jpg

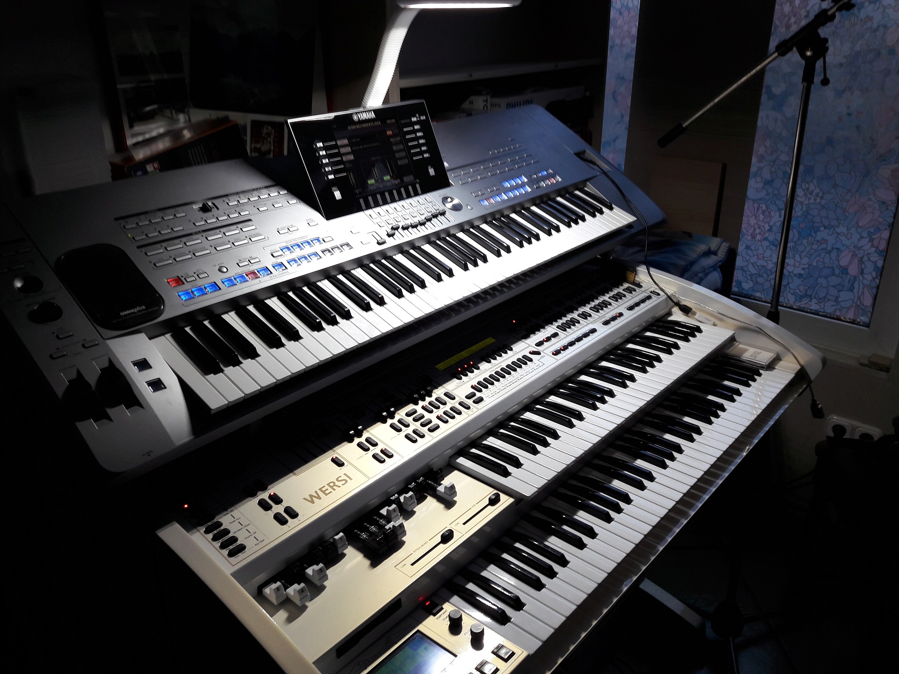
PCB/think84/7月28日开源文件/7月28日开源文件/高清键盘图/musical-instrument-1865597_1920.jpg
