xcl666/trackpoint-mechanical-keyboard/PCB/think84/7月28日开源文件/7月28日开源文件/高清键盘图/typewriter-1138293_1920.png

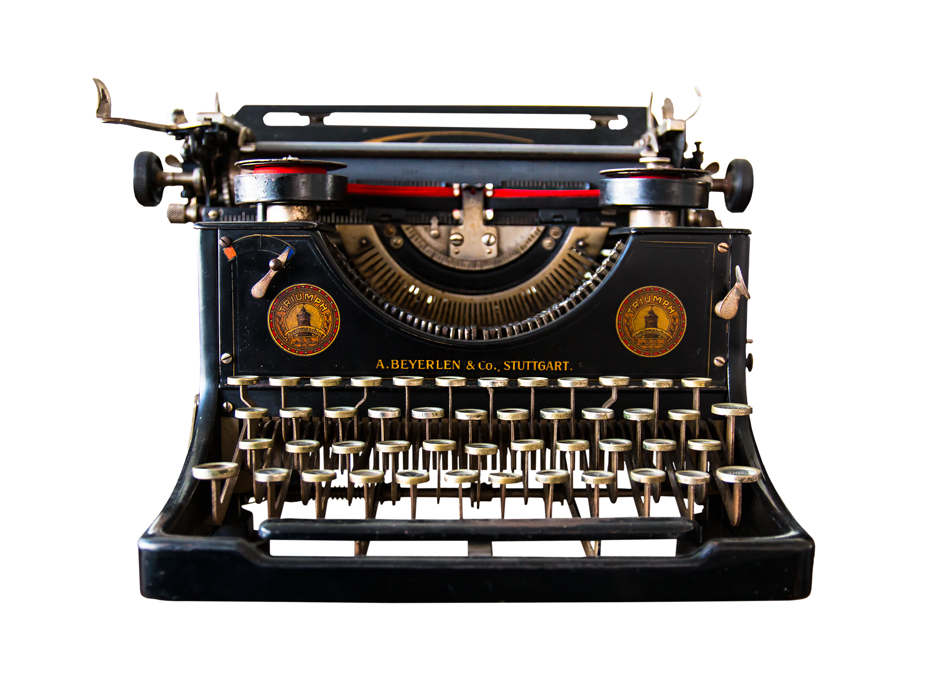
PCB/think84/7月28日开源文件/7月28日开源文件/高清键盘图/typewriter-1138293_1920.png
