xcl666/trackpoint-mechanical-keyboard/PCB/tp2000/formula.jpg

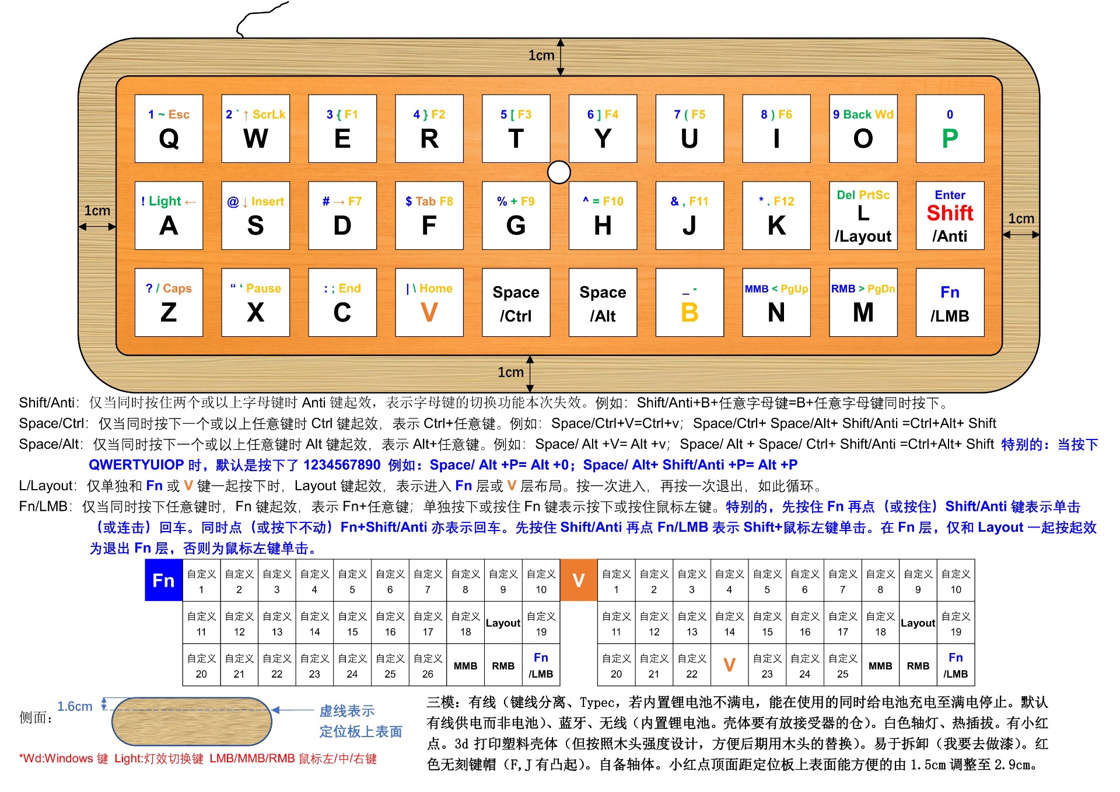
PCB/tp2000/formula.jpg
