xcl666/trackpoint-mechanical-keyboard/PCB/tpec32-main/tpec32-main/img/01.jpg

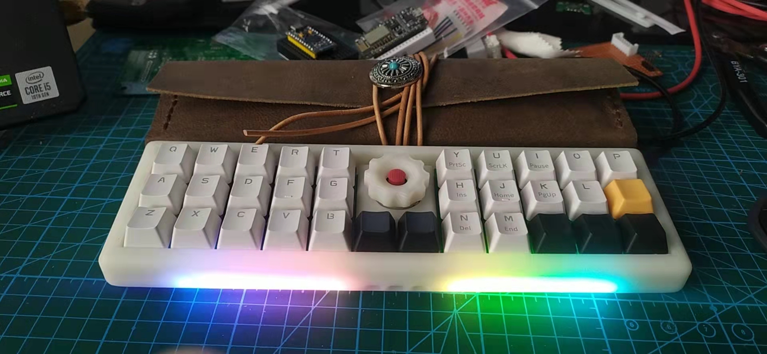
PCB/tpec32-main/tpec32-main/img/01.jpg
