xcl666/trackpoint-mechanical-keyboard/PCB/tpec32-main/tpec32-main/img/encoder.png

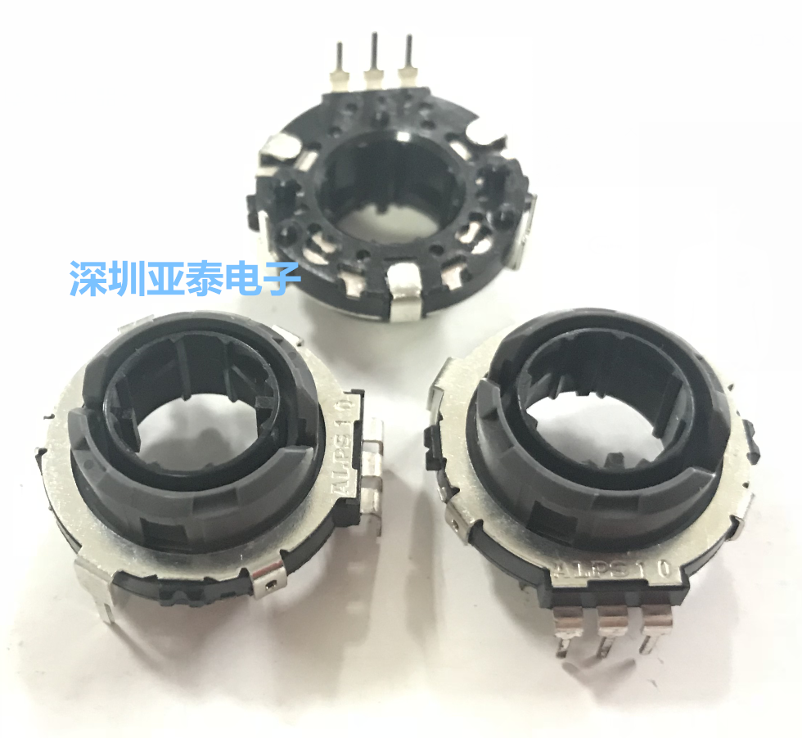
PCB/tpec32-main/tpec32-main/img/encoder.png
