xcl666/trackpoint-mechanical-keyboard/PCB/tpec32-main/tpec32-main/img/knob.JPG

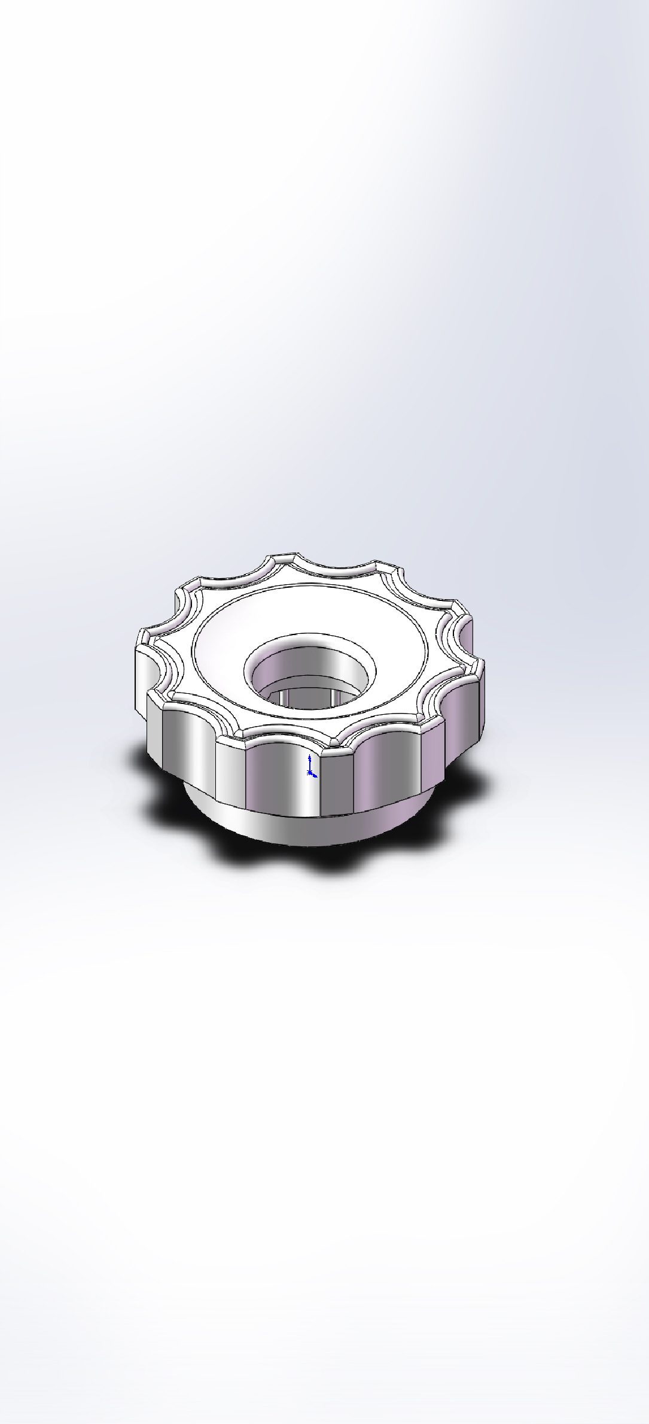
PCB/tpec32-main/tpec32-main/img/knob.JPG
