xcl666/trackpoint-mechanical-keyboard/PCB/tpec32-main/tpec32-main/img/pcb.jpg

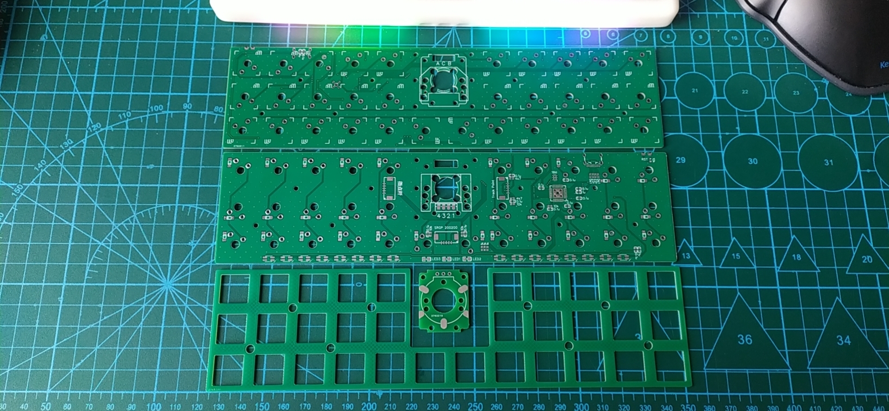
PCB/tpec32-main/tpec32-main/img/pcb.jpg
