xcl666/trackpoint-mechanical-keyboard/PCB/tpec32-main/tpec32-main/img/rod_1.JPG

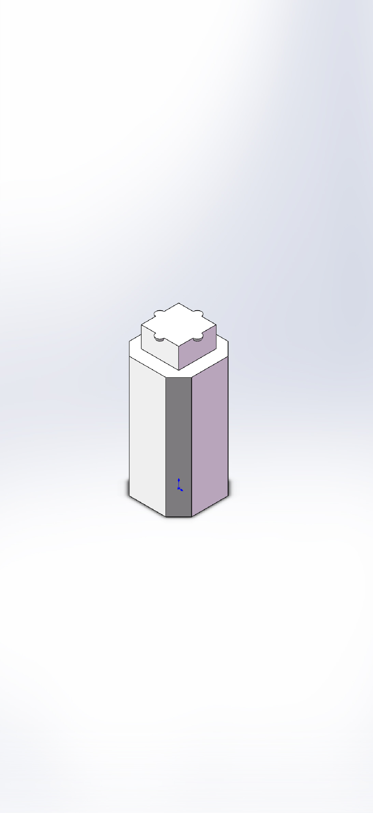
PCB/tpec32-main/tpec32-main/img/rod_1.JPG
