xcl666/trackpoint-mechanical-keyboard/PCB/tpec32-main/tpec32-main/img/shell.JPG

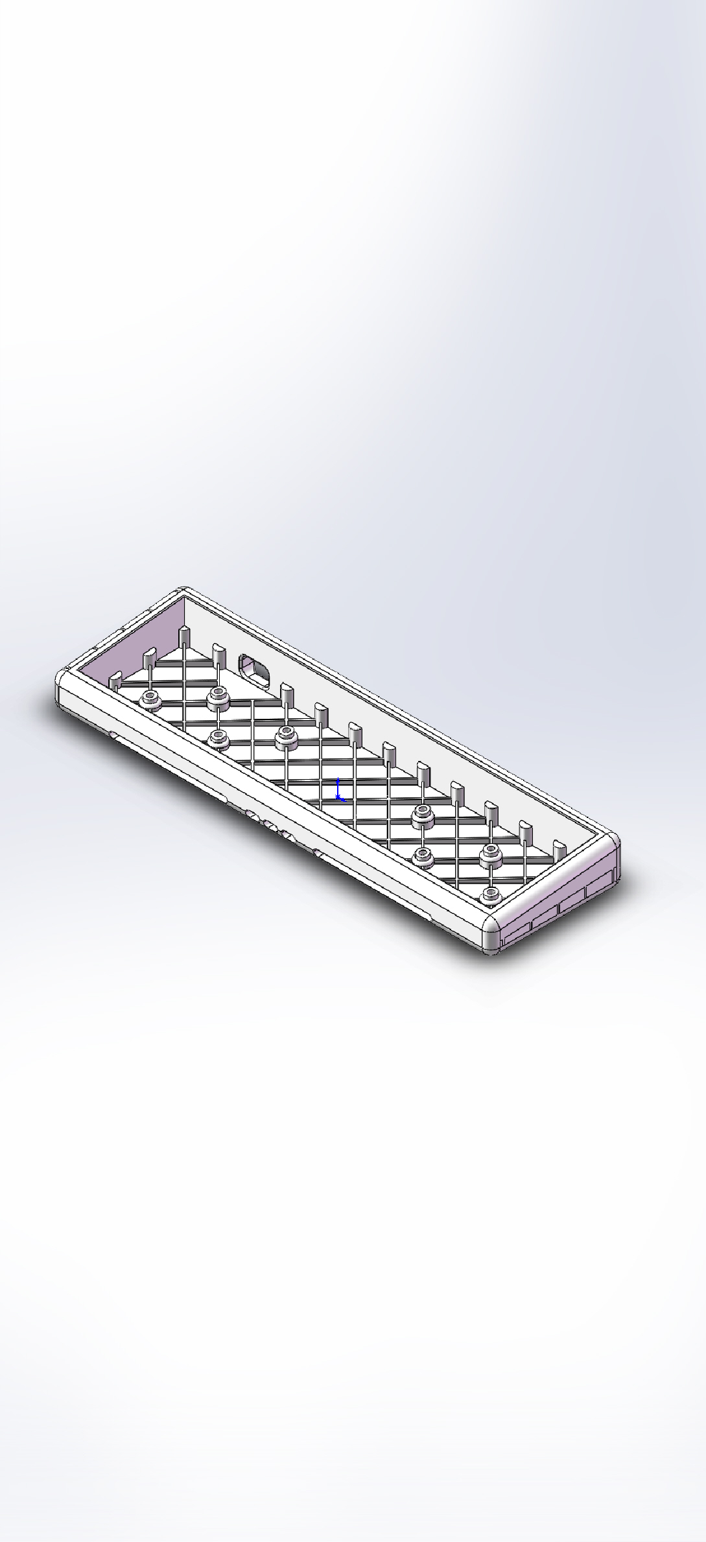
PCB/tpec32-main/tpec32-main/img/shell.JPG
