xcl666/trackpoint-mechanical-keyboard/PCB/tpec32-main/tpec32-main/img/thinkpad.jpg

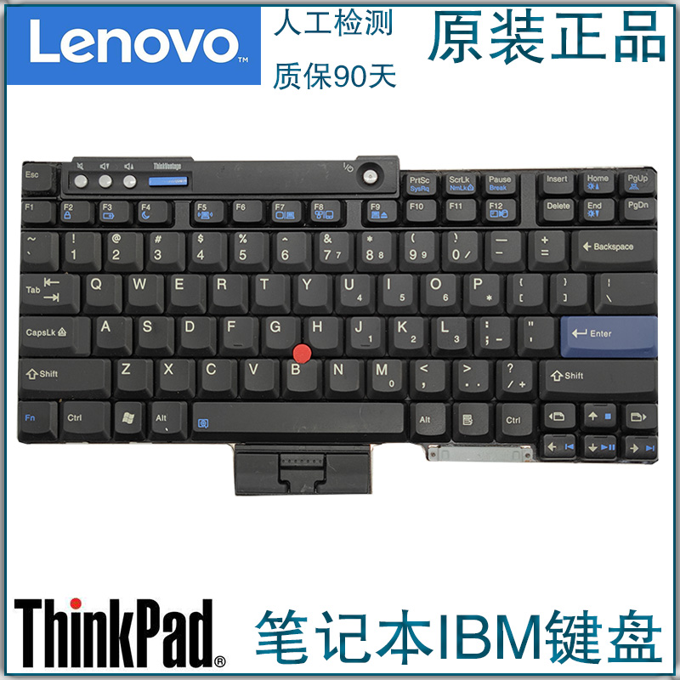
PCB/tpec32-main/tpec32-main/img/thinkpad.jpg
