xcl666/trackpoint-mechanical-keyboard/PCB/tpec32-main/tpec32-main/img/tp_2.jpg

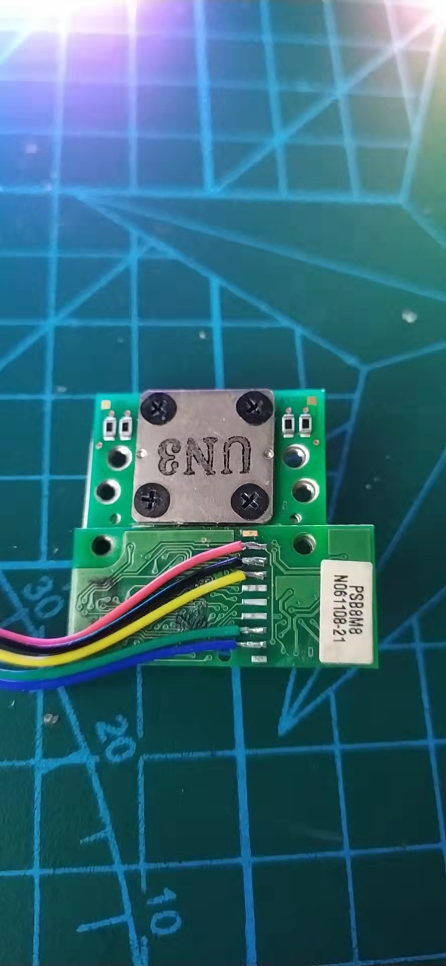
PCB/tpec32-main/tpec32-main/img/tp_2.jpg
