xcl666/trackpoint-mechanical-keyboard/PCB/tpec32-main/tpec32-main/img/tp_lid.JPG

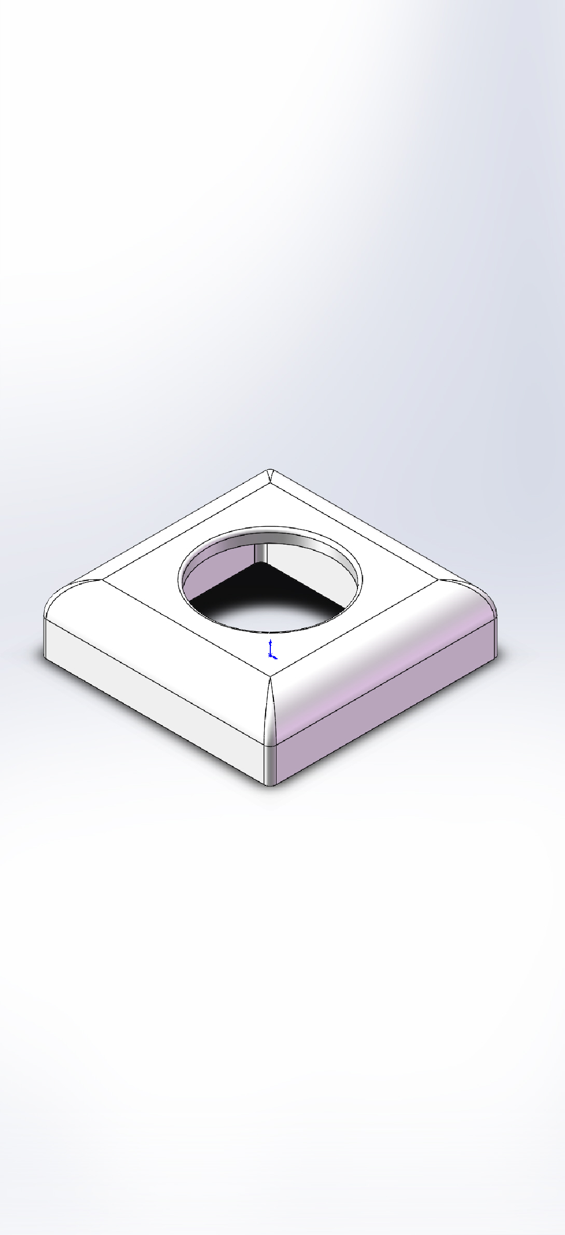
PCB/tpec32-main/tpec32-main/img/tp_lid.JPG
