xcl666/trackpoint-mechanical-keyboard/PCB/tppad/pic/QQ图片20211202125502.jpg

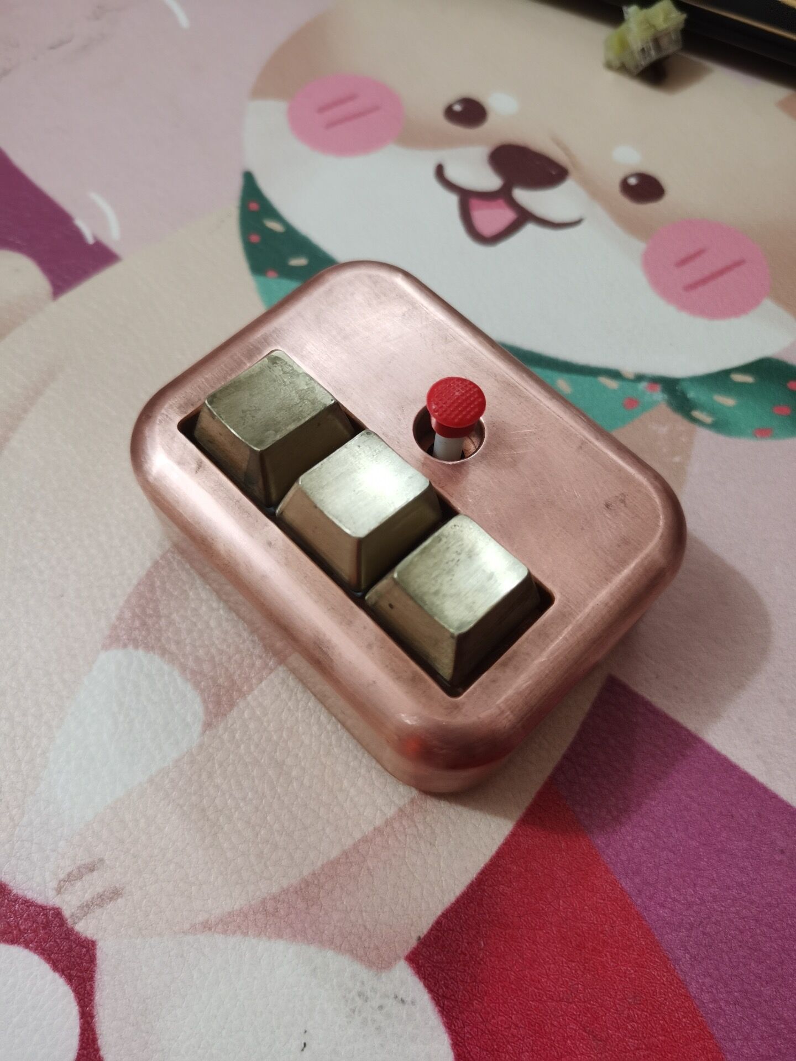
PCB/tppad/pic/QQ图片20211202125502.jpg
