xcl666/trackpoint-mechanical-keyboard/PCB/TP键盘升级包/TP键盘升级包/help.png

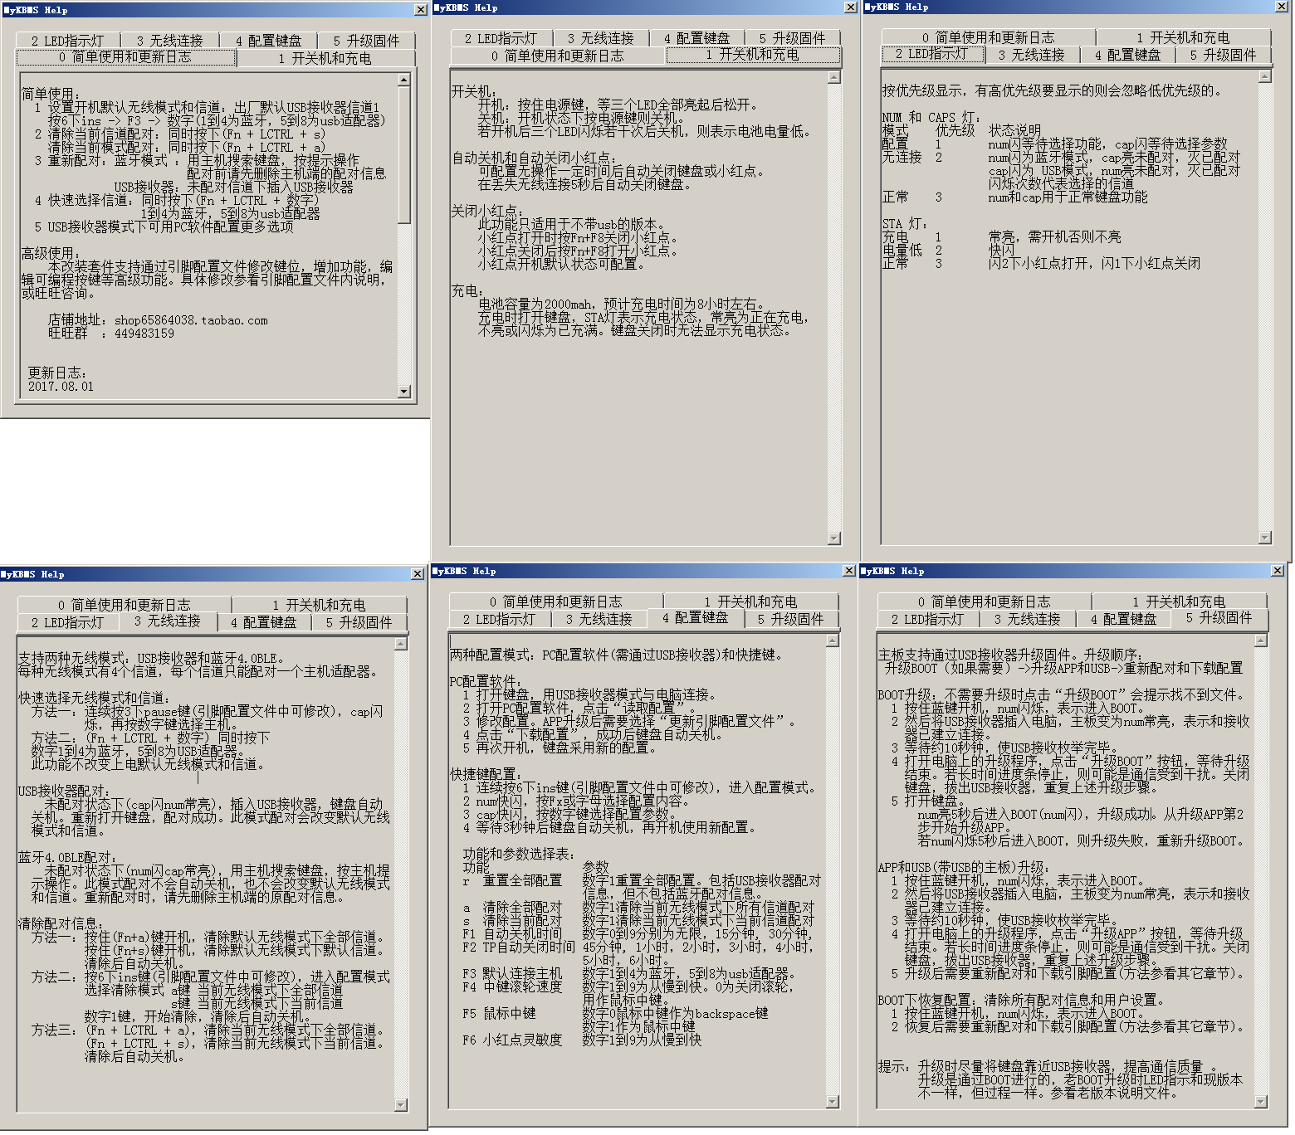
PCB/TP键盘升级包/TP键盘升级包/help.png
