xcl666/trackpoint-mechanical-keyboard/PCB/TrackPoint Hardware - Deskthority wiki_files/179px-LVMV-TrackPoint-front.jpeg

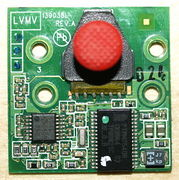
PCB/TrackPoint Hardware - Deskthority wiki_files/179px-LVMV-TrackPoint-front.jpeg
