xcl666/trackpoint-mechanical-keyboard/PCB/TrackPoint Hardware - Deskthority wiki_files/240px-IBM-SpaceSaver-II.jpeg

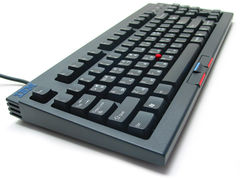
PCB/TrackPoint Hardware - Deskthority wiki_files/240px-IBM-SpaceSaver-II.jpeg
