xcl666/trackpoint-mechanical-keyboard/PCB/TrackPoint Hardware - Deskthority wiki_files/240px-R61_front.JPG

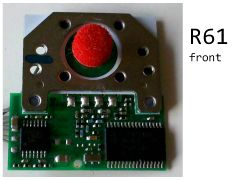
PCB/TrackPoint Hardware - Deskthority wiki_files/240px-R61_front.JPG
