xcl666/trackpoint-mechanical-keyboard/PCB/TrackPoint Hardware - Deskthority wiki_files/283px-SSII-screws.jpeg

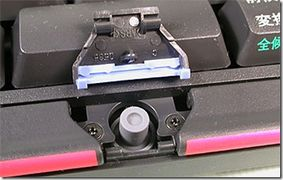
PCB/TrackPoint Hardware - Deskthority wiki_files/283px-SSII-screws.jpeg
