xcl666/trackpoint-mechanical-keyboard/PCB/TrackPoint Hardware - Deskthority wiki_files/400px-R40_back.JPG

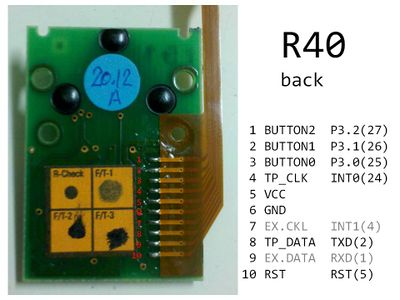
PCB/TrackPoint Hardware - Deskthority wiki_files/400px-R40_back.JPG
