xcl666/trackpoint-mechanical-keyboard/PCB/TrackPoint Hardware - Deskthority wiki_files/535px-SSII-TrackPoint.jpeg

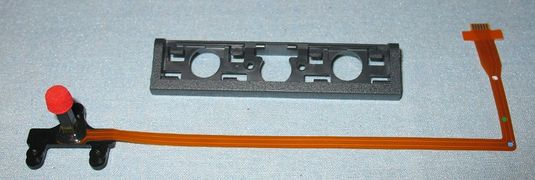
PCB/TrackPoint Hardware - Deskthority wiki_files/535px-SSII-TrackPoint.jpeg
