xcl666/trackpoint-mechanical-keyboard/PCB/TrackPoint Hardware - Deskthority wiki_files/600px-Pinout-trackpoint-LVC9.jpg

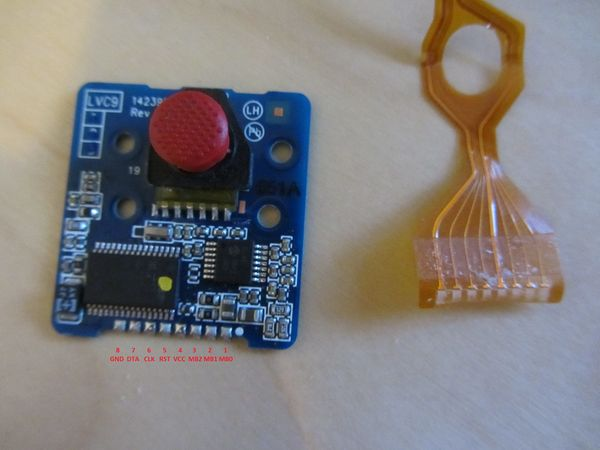
PCB/TrackPoint Hardware - Deskthority wiki_files/600px-Pinout-trackpoint-LVC9.jpg
