xcl666/trackpoint-mechanical-keyboard/PCB/TrackPoint Hardware - Deskthority wiki_files/600px-Pinout-trackpoint-LVMV.JPG

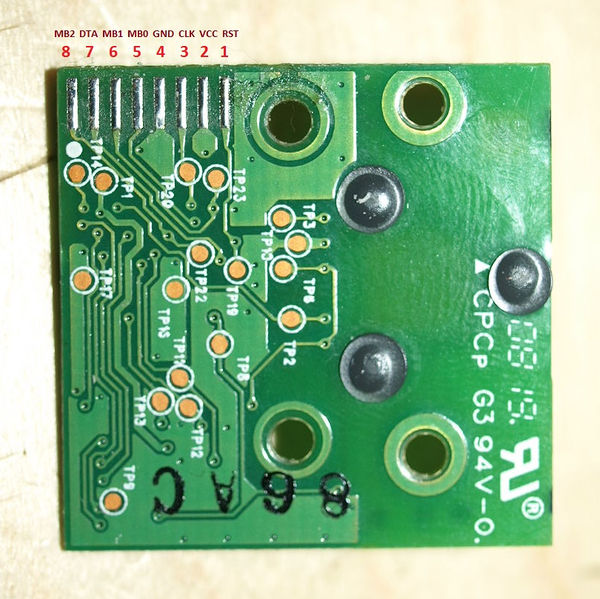
PCB/TrackPoint Hardware - Deskthority wiki_files/600px-Pinout-trackpoint-LVMV.JPG
