xcl666/trackpoint-mechanical-keyboard/PCB/TrackPoint Hardware - Deskthority wiki_files/600px-Ssii-controller.jpeg

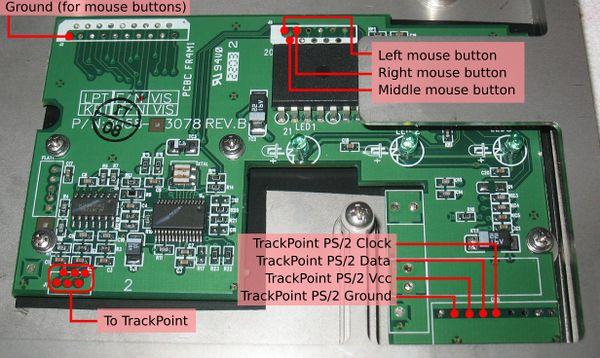
PCB/TrackPoint Hardware - Deskthority wiki_files/600px-Ssii-controller.jpeg
