xcl666/trackpoint-mechanical-keyboard/PCB/TrackPoint Hardware - Deskthority wiki_files/800px-T40-Pinout.png

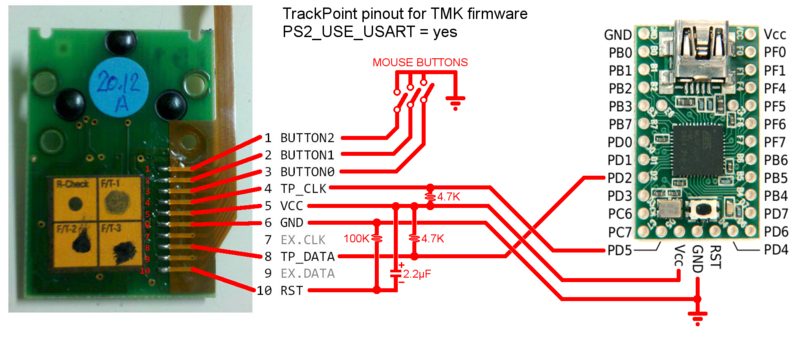
PCB/TrackPoint Hardware - Deskthority wiki_files/800px-T40-Pinout.png
