xcl666/trackpoint-mechanical-keyboard/PCB/trackpoint/A4Riv.jpg

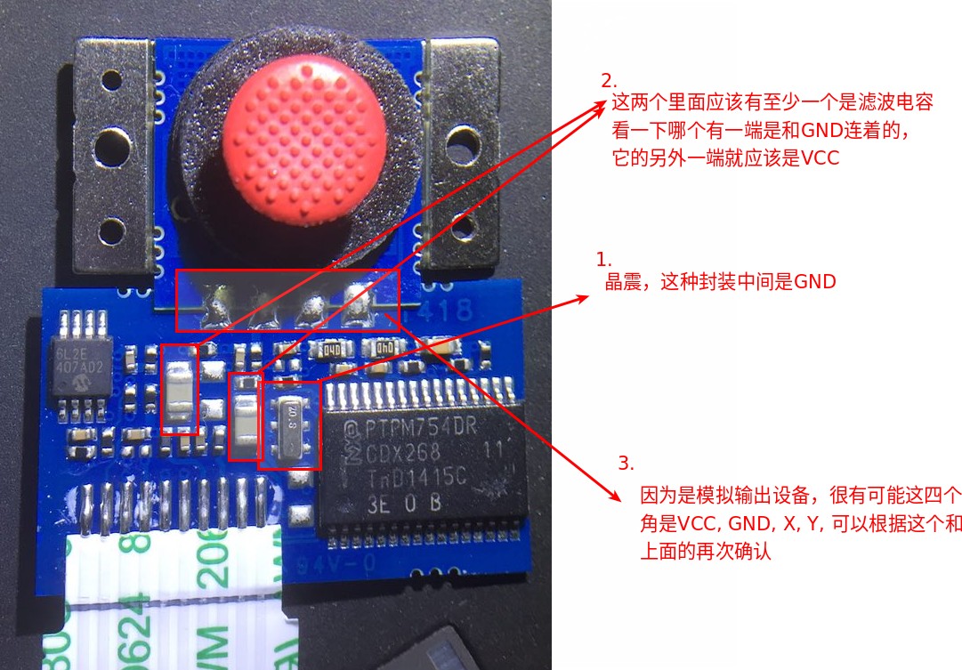
PCB/trackpoint/A4Riv.jpg
