xcl666/trackpoint-mechanical-keyboard/PCB/trackpoint/interesting/轨迹球板外壳/1.jpg

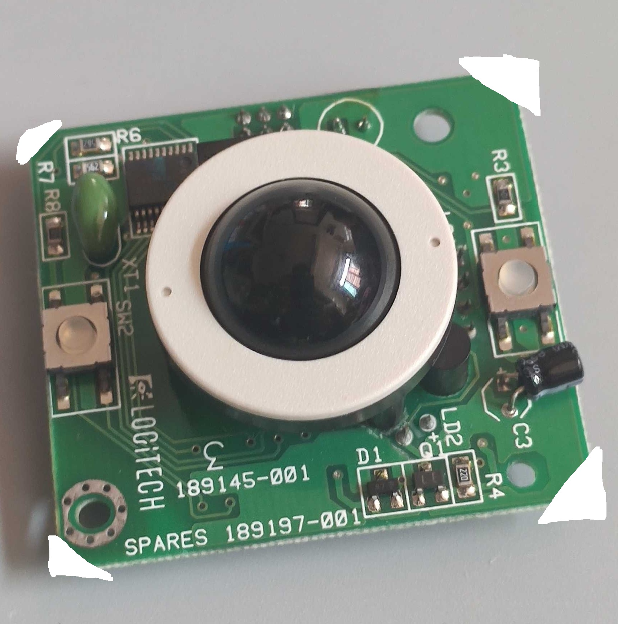
PCB/trackpoint/interesting/轨迹球板外壳/1.jpg
