xcl666/trackpoint-mechanical-keyboard/PCB/trackpoint/newtp/QQ图片20211201124901.jpg

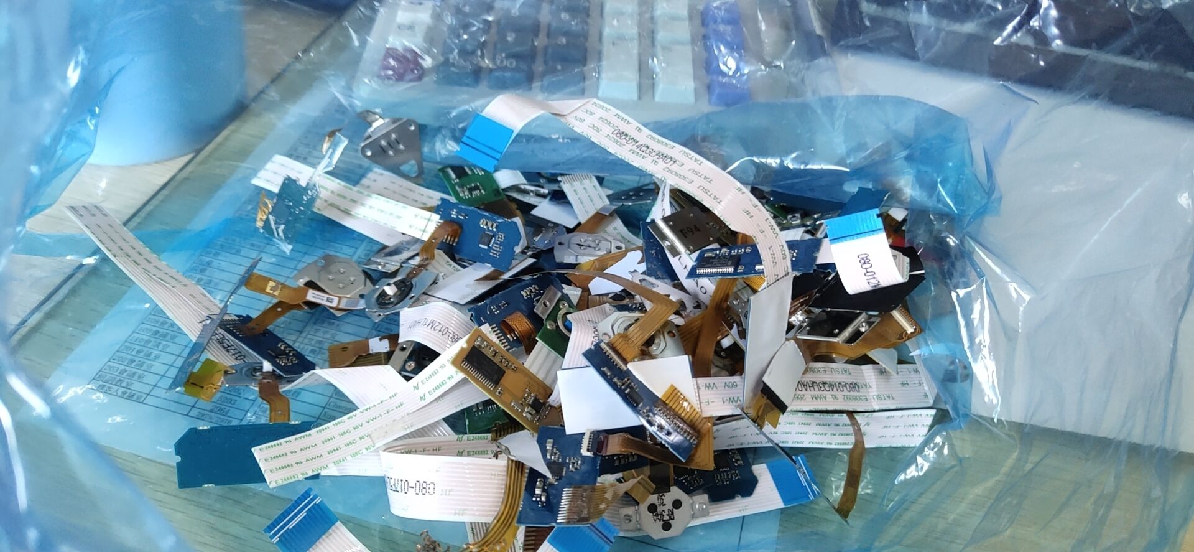
PCB/trackpoint/newtp/QQ图片20211201124901.jpg
