xcl666/trackpoint-mechanical-keyboard/PCB/trackpoint/newtp/QQ图片20211201125002.jpg

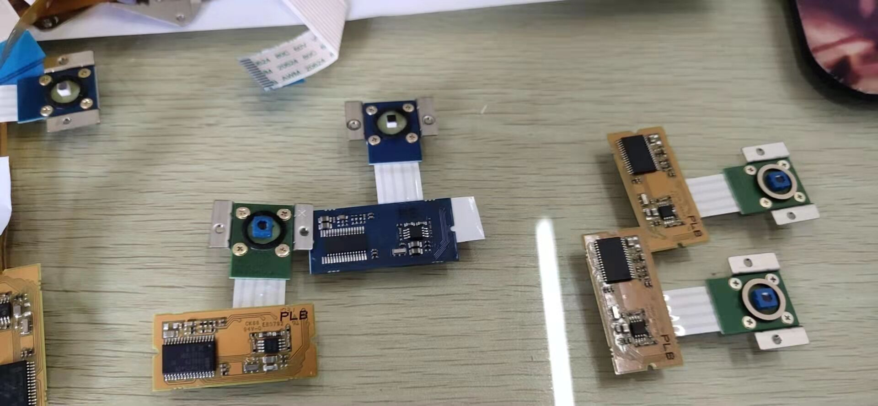
PCB/trackpoint/newtp/QQ图片20211201125002.jpg
