xcl666/trackpoint-mechanical-keyboard/PCB/trackpoint/tex_trackpoint.jpg

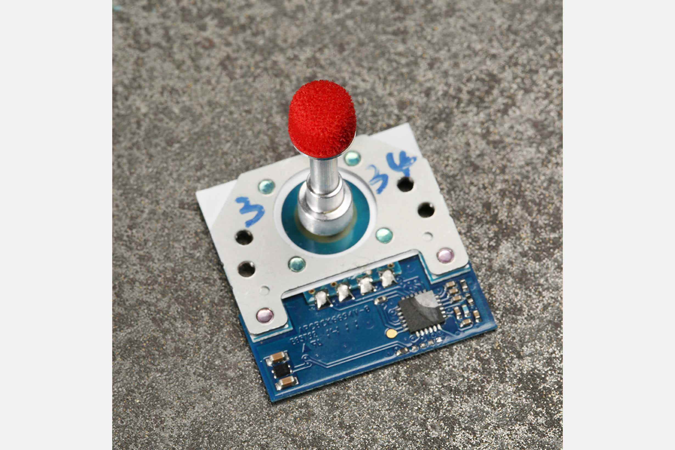
PCB/trackpoint/tex_trackpoint.jpg
