xcl666/trackpoint-mechanical-keyboard/PCB/trackpoint/TPM754_IC.jpg

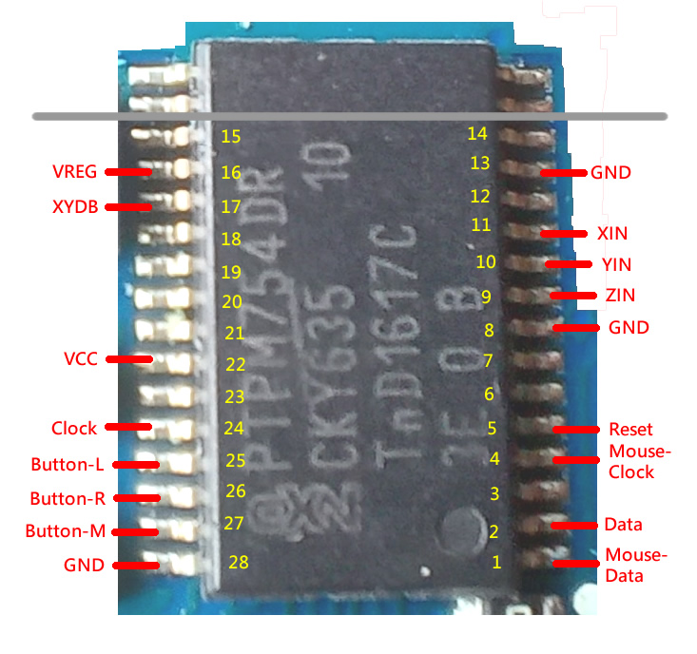
PCB/trackpoint/TPM754_IC.jpg
