xcl666/trackpoint-mechanical-keyboard/PCB/trackpoint/定位点计算.png

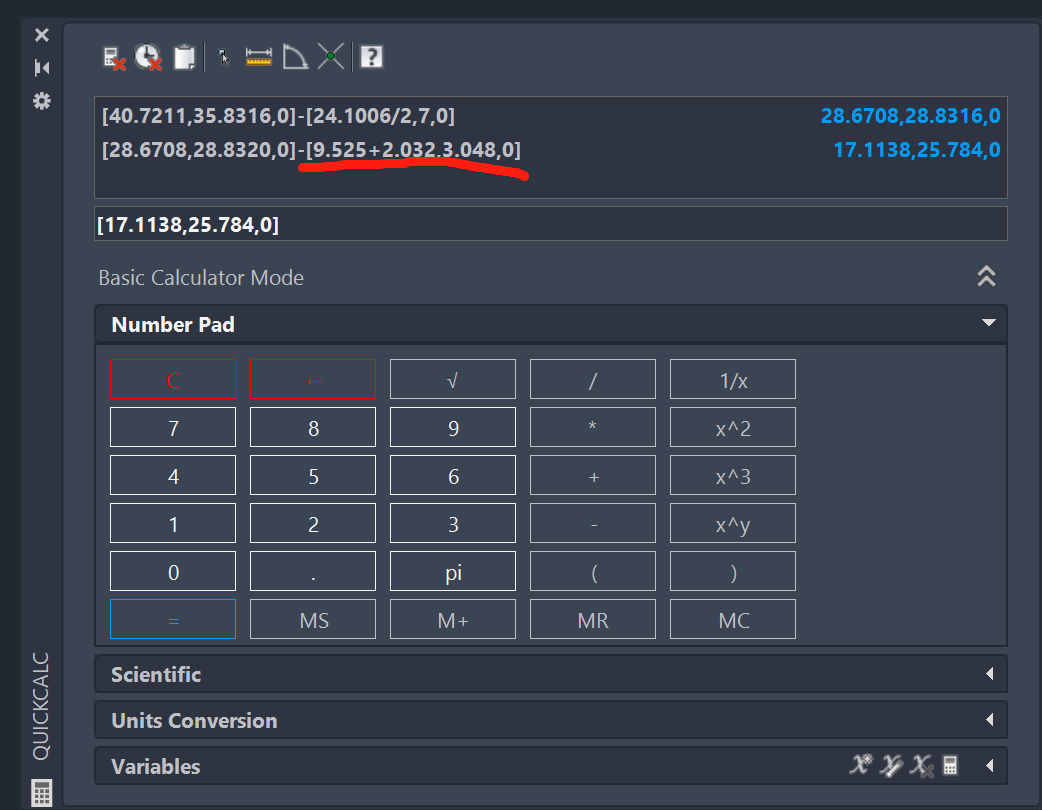
PCB/trackpoint/定位点计算.png
