xcl666/trackpoint-mechanical-keyboard/PCB/trackpoint/阿里旺旺图片20211220091814.jpg

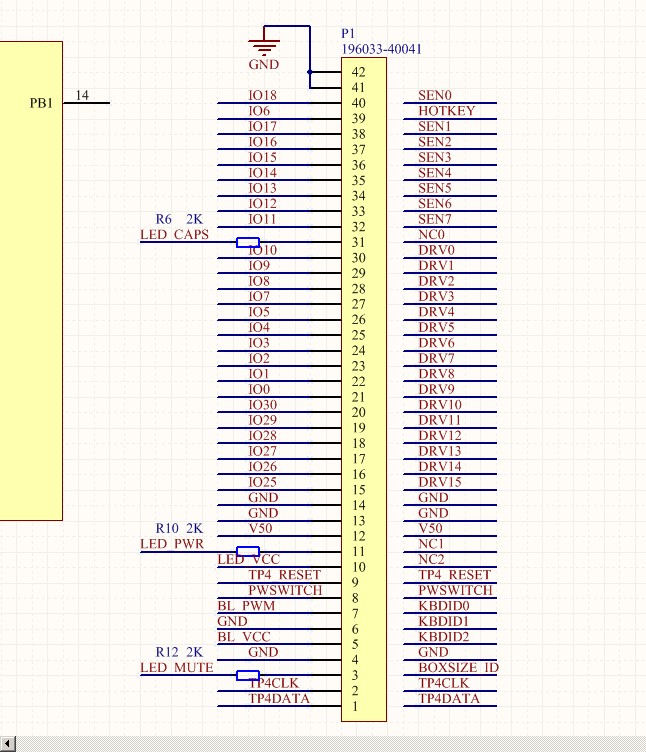
PCB/trackpoint/阿里旺旺图片20211220091814.jpg
