xcl666/trackpoint-mechanical-keyboard/Pic/speed.JPG

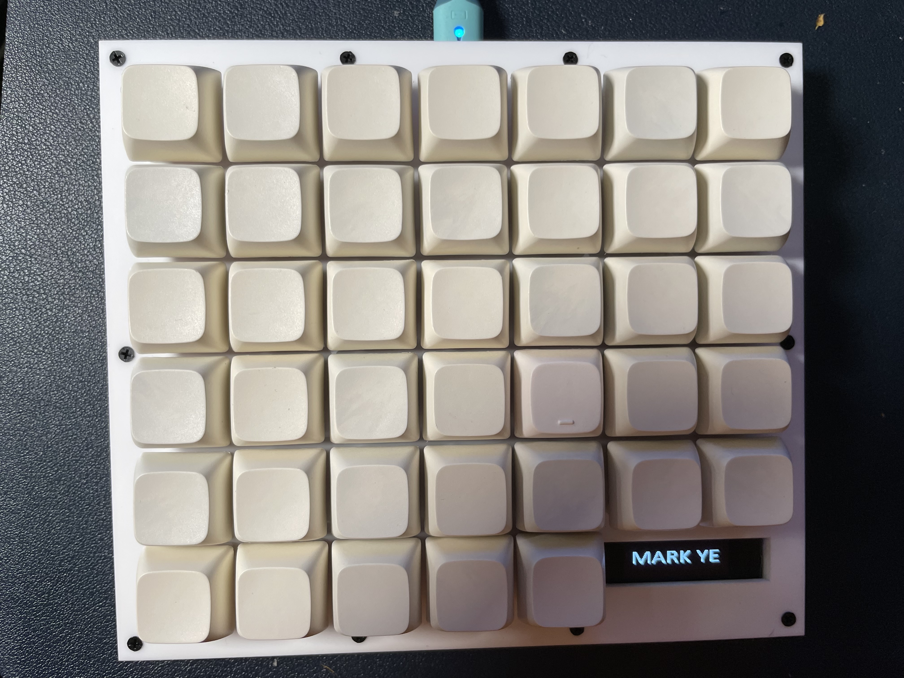
Pic/speed.JPG
