xcl666/trackpoint-mechanical-keyboard/qmk_firmware/keyboards/xcl/at90usb128.jpeg

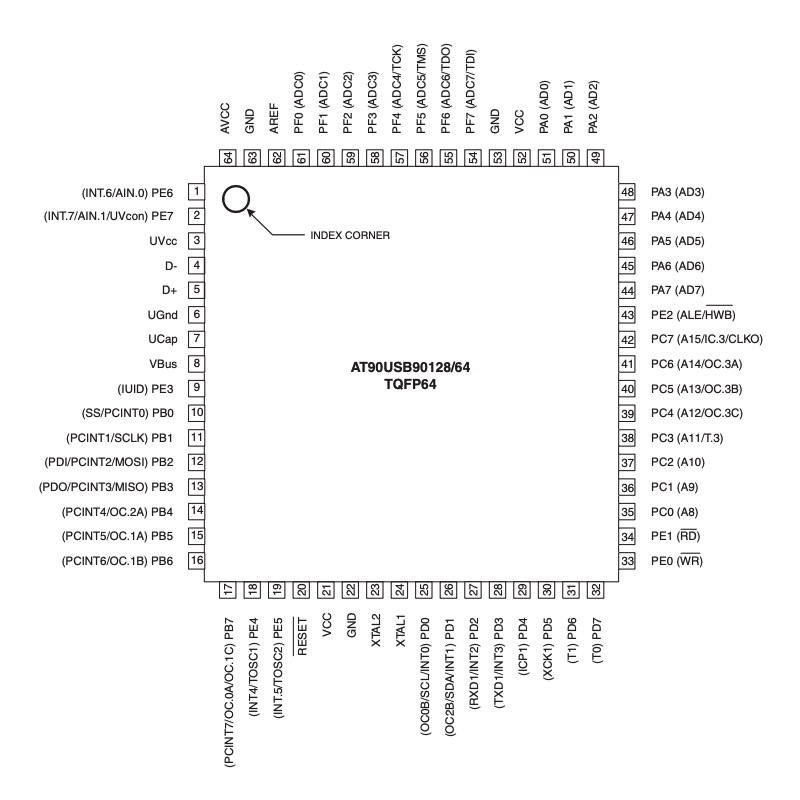
qmk_firmware/keyboards/xcl/at90usb128.jpeg
