xcl666/trackpoint-mechanical-keyboard/qmk_firmware/keyboards/xcl/atmega32u4.jpeg

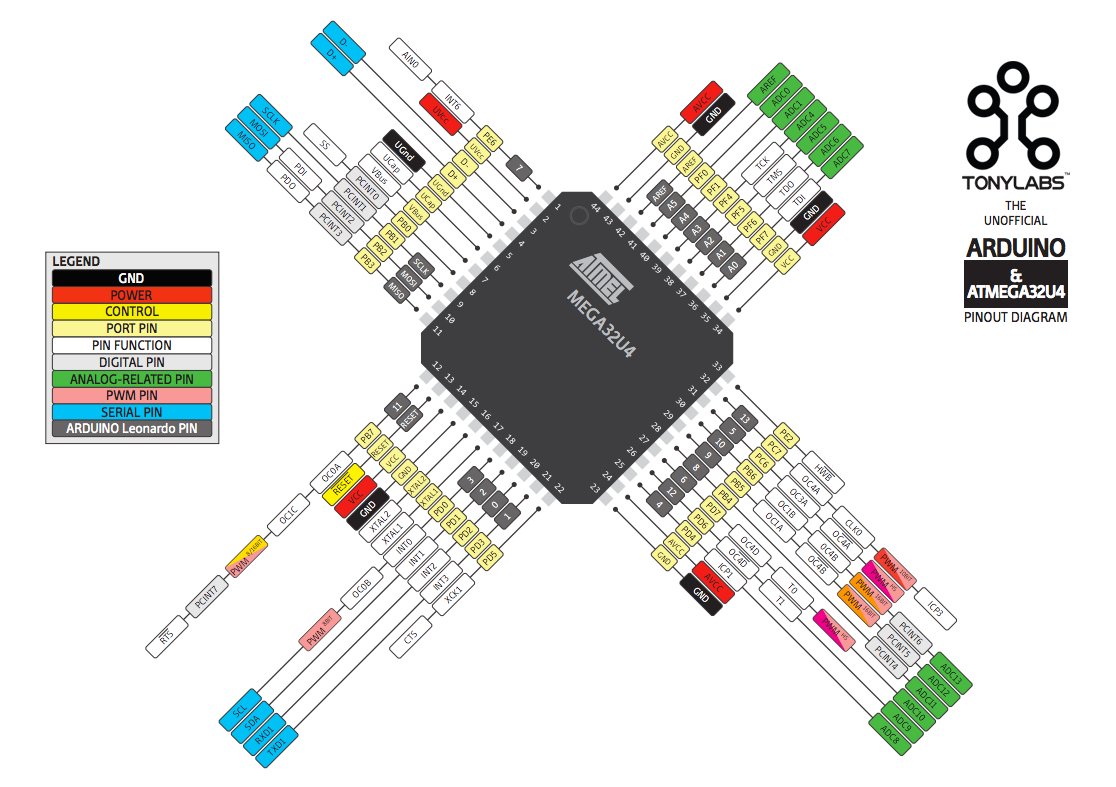
qmk_firmware/keyboards/xcl/atmega32u4.jpeg
