xcl666/trackpoint-mechanical-keyboard/qmk_firmware/keyboards/xcl/atmega328p.jpeg

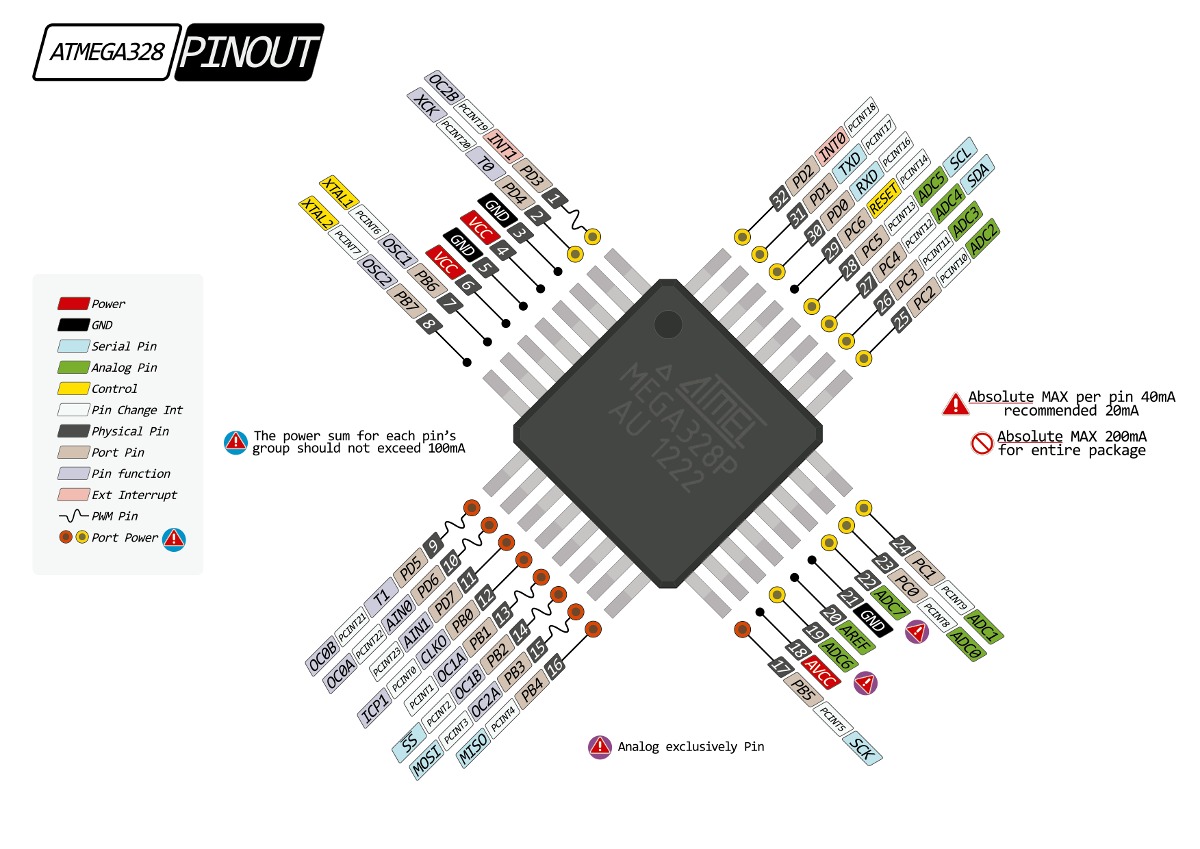
qmk_firmware/keyboards/xcl/atmega328p.jpeg
