xcl666/trackpoint-mechanical-keyboard/qmk_firmware/keyboards/xcl/black-pill.jpeg

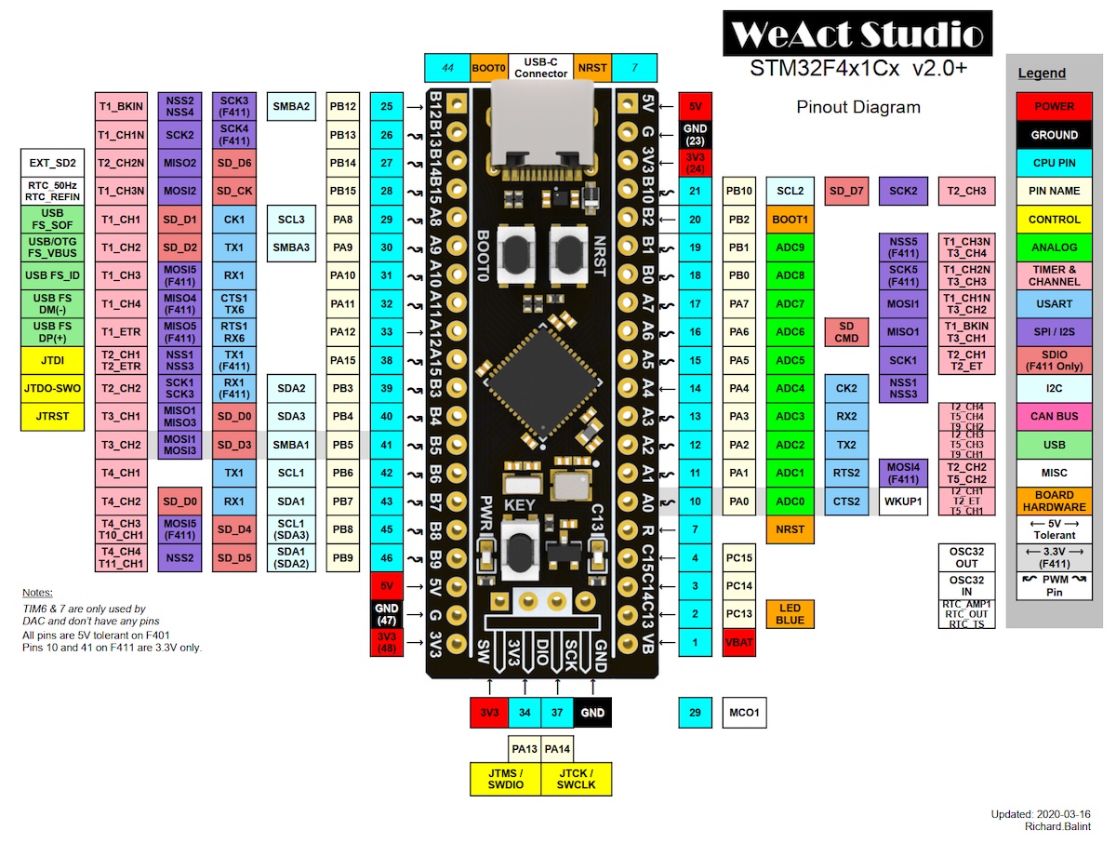
qmk_firmware/keyboards/xcl/black-pill.jpeg
