xcl666/trackpoint-mechanical-keyboard/qmk_firmware/keyboards/xcl/pro-micro.jpeg

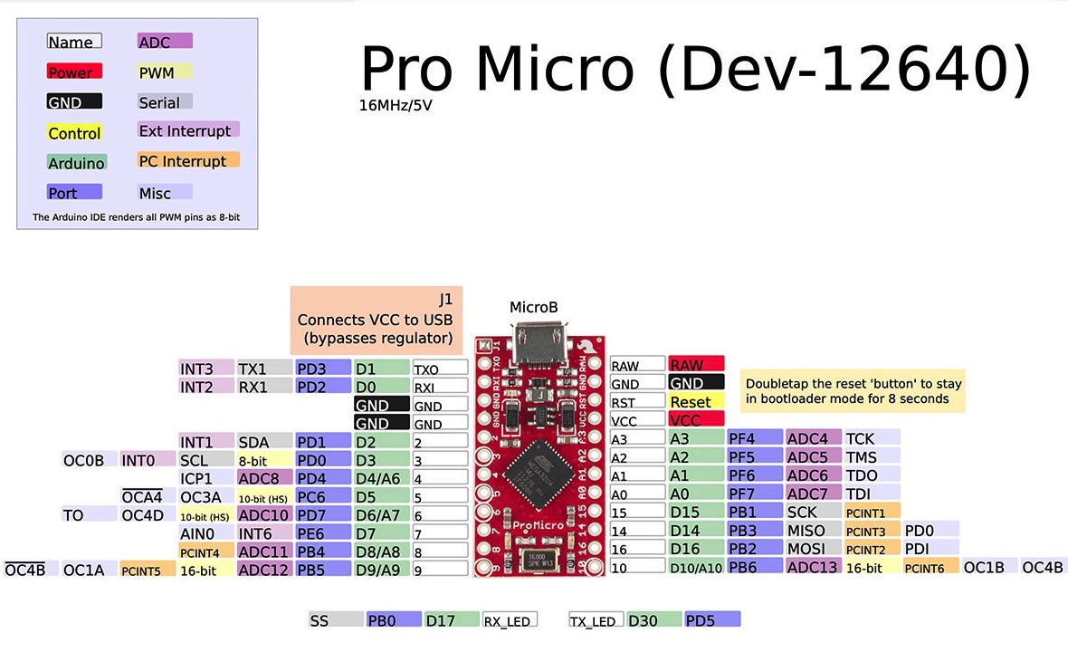
qmk_firmware/keyboards/xcl/pro-micro.jpeg
