xcl666/trackpoint-mechanical-keyboard/qmk_firmware/keyboards/xcl/pro-mini.jpeg

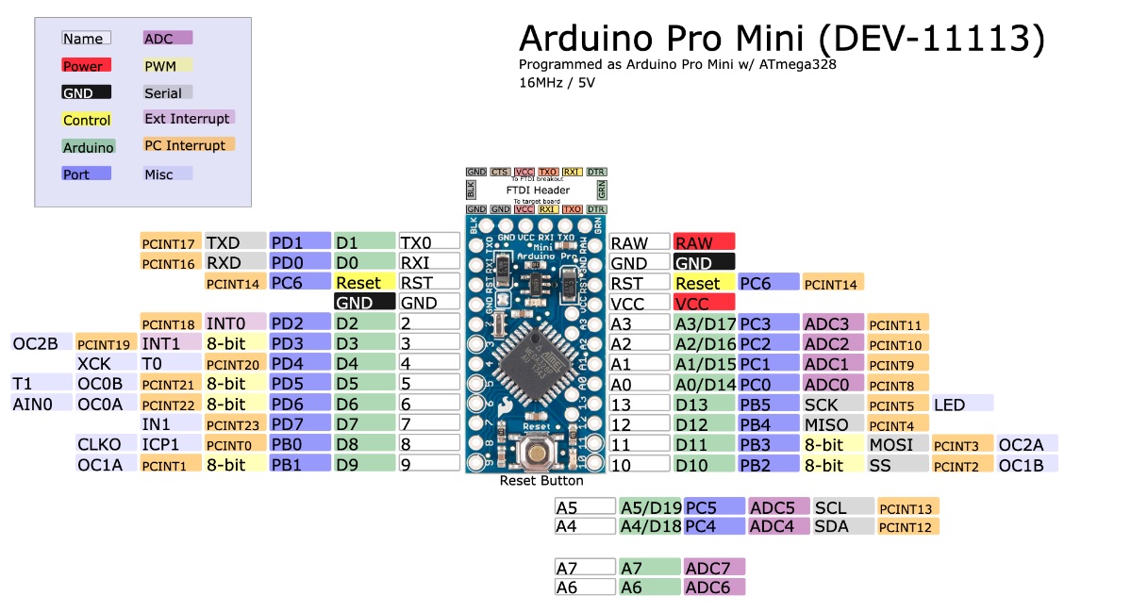
qmk_firmware/keyboards/xcl/pro-mini.jpeg
