xcl666/trackpoint-mechanical-keyboard/qmk_firmware/keyboards/xcl/stm32f103c8t6.jpeg

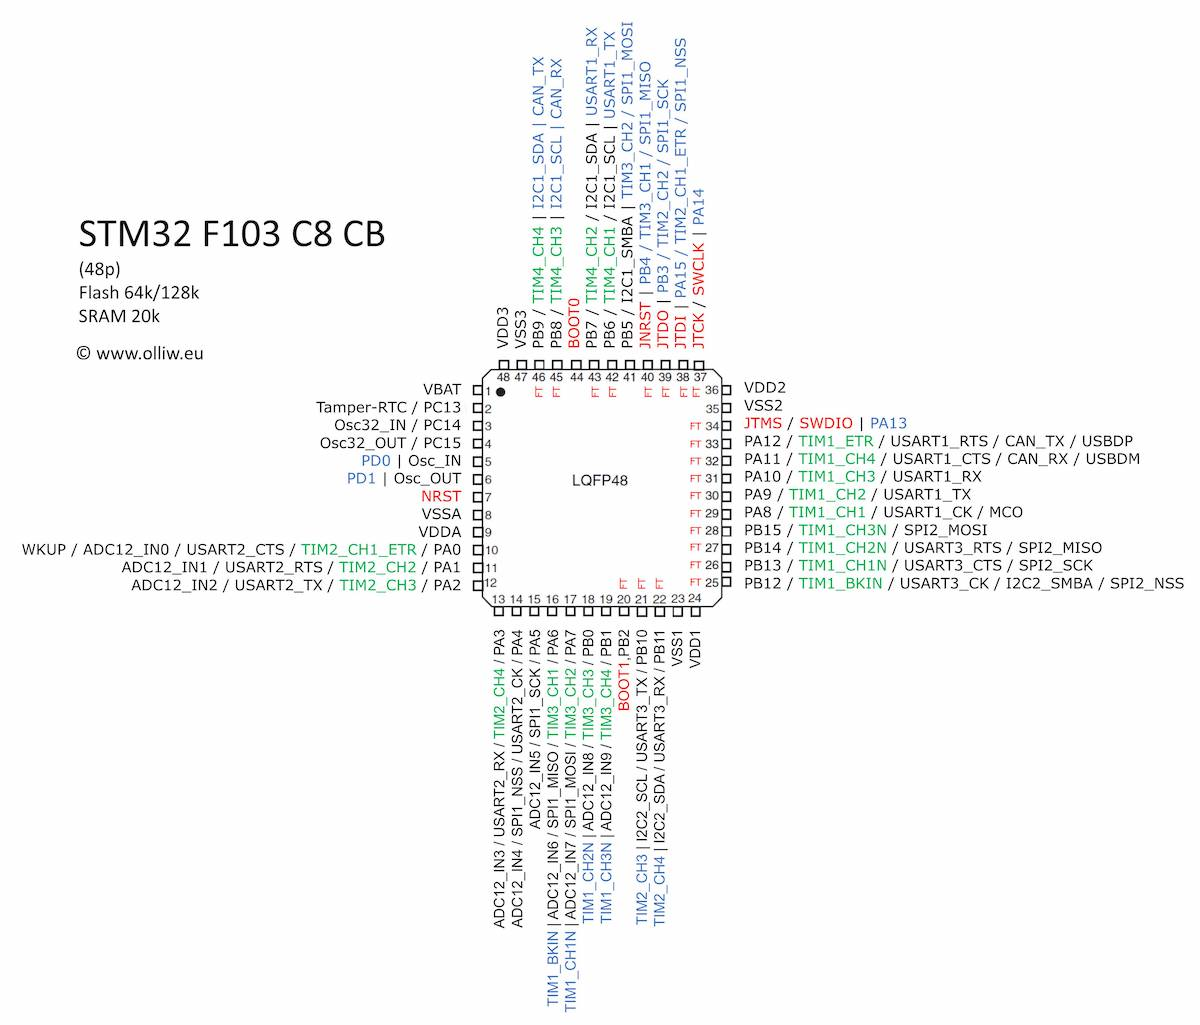
qmk_firmware/keyboards/xcl/stm32f103c8t6.jpeg
