xcl666/trackpoint-mechanical-keyboard/qmk_firmware/keyboards/xcl/teensy++.jpeg

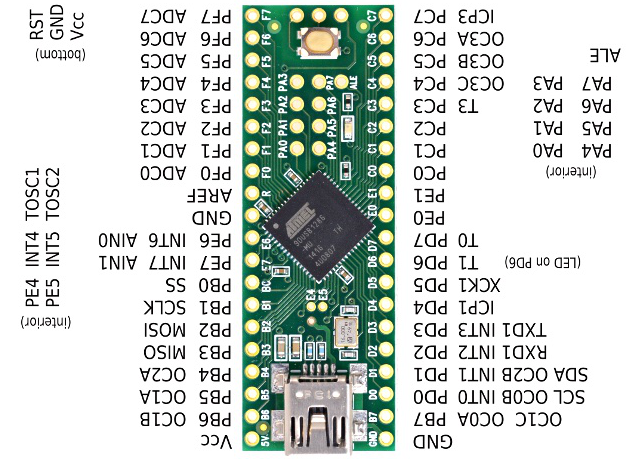
qmk_firmware/keyboards/xcl/teensy++.jpeg
