xcl666/trackpoint-mechanical-keyboard/PCB/alice/3D/myown/new/组装.SLDASM

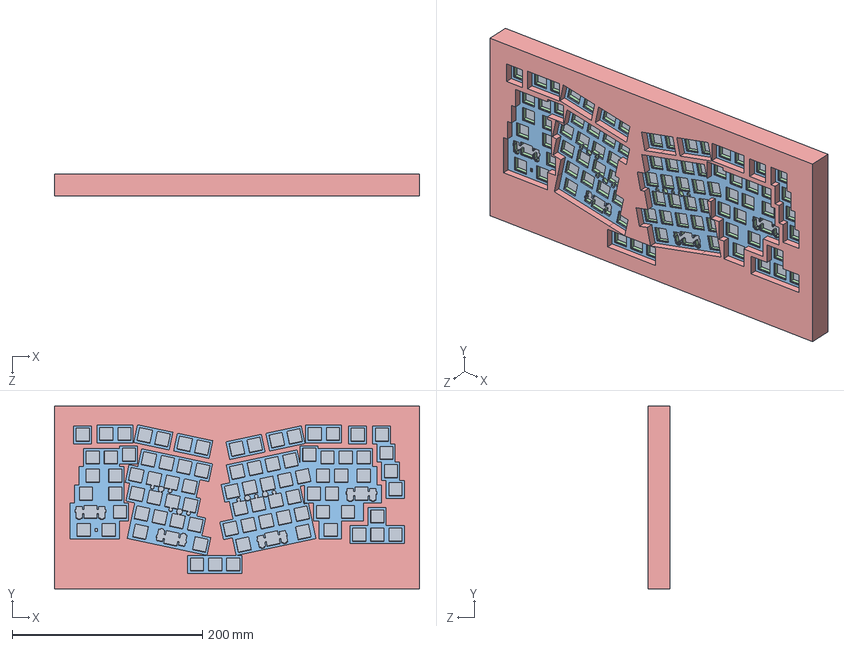
[picture p127: CAD file, 2022-12-10]
PCB/alice/3D/myown/new/组装.SLDASM
383.5 x 192.0 x 23.5 mm
上壳
夹心棉
定位板
底壳
底棉
