xcl666/trackpoint-mechanical-keyboard/PCB/alice/3D/TA上盖.step

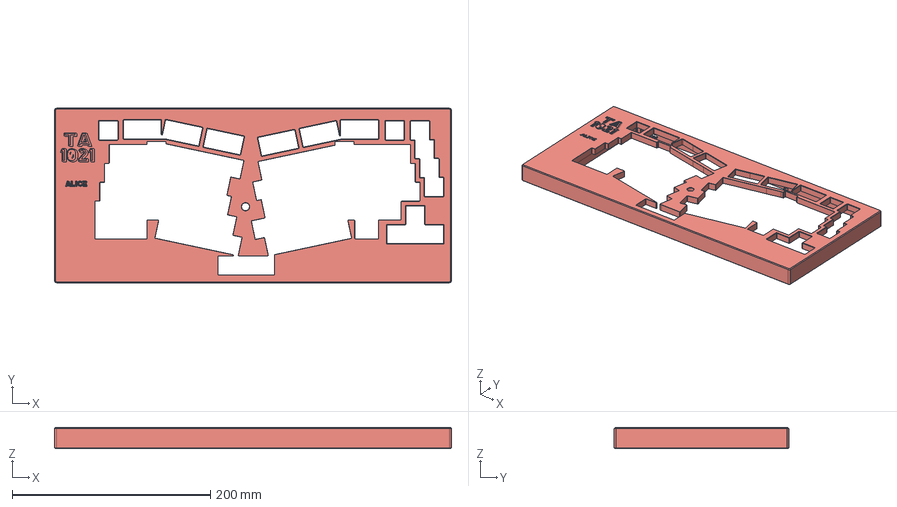
[picture p141: CAD file, 2022-12-10]
PCB/alice/3D/TA上盖.step
400.5 x 176.0 x 21.3 mm
