xcl666/trackpoint-mechanical-keyboard/PCB/alice/adelheid/adelheid-master/adelheid-master/case/foam/foam.dxf

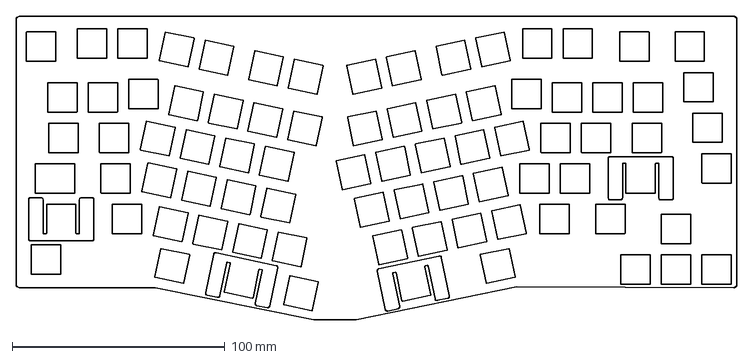
[picture p143: CAD file, 2022-12-10]
PCB/alice/adelheid/adelheid-master/adelheid-master/case/foam/foam.dxf
338.9 x 142.6 mm
