xcl666/trackpoint-mechanical-keyboard/PCB/alice/adelheid/adelheid-master/adelheid-master/case/lasercut-layers/hipro_layers_addon.dxf

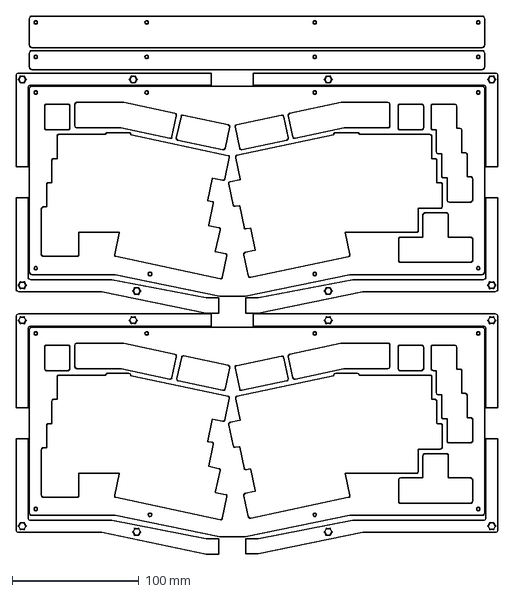
[picture p144: CAD file, 2022-12-10]
PCB/alice/adelheid/adelheid-master/adelheid-master/case/lasercut-layers/hipro_layers_addon.dxf
380.2 x 424.4 mm
