xcl666/trackpoint-mechanical-keyboard/PCB/alice/Kolibri/Kolibri-main/Kolibri-main/Case/03 Case gasket.dxf

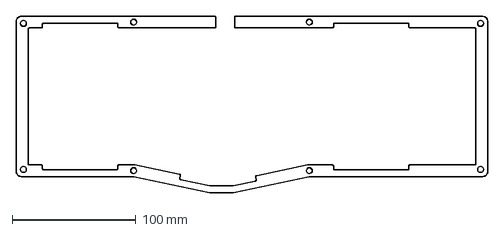
[picture p145: CAD file, 2022-12-10]
PCB/alice/Kolibri/Kolibri-main/Kolibri-main/Case/03 Case gasket.dxf
381.4 x 142.8 mm
