xcl666/trackpoint-mechanical-keyboard/PCB/alice/shell/TA1021lastswitchv5ToTop.dxf

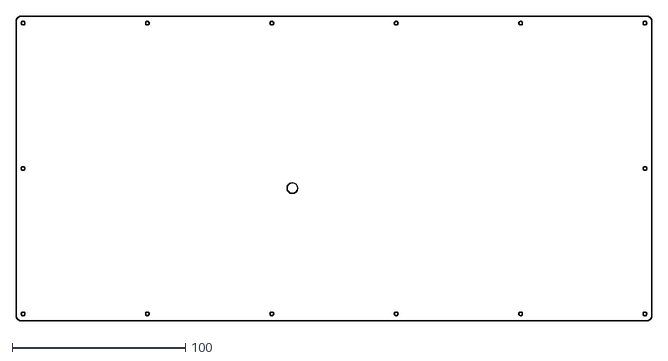
[picture p146: CAD file, 2022-12-10]
PCB/alice/shell/TA1021lastswitchv5ToTop.dxf
367.5 x 176.0
