xcl666/trackpoint-mechanical-keyboard/PCB/think48/PCB通用v1.dxf

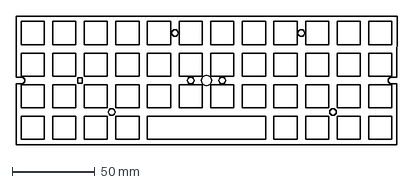
[picture p147: CAD file, 2022-12-10]
PCB/think48/PCB通用v1.dxf
229.6 x 77.2 mm
