xcl666/trackpoint-mechanical-keyboard/PCB/Think60/think60plate.dxf

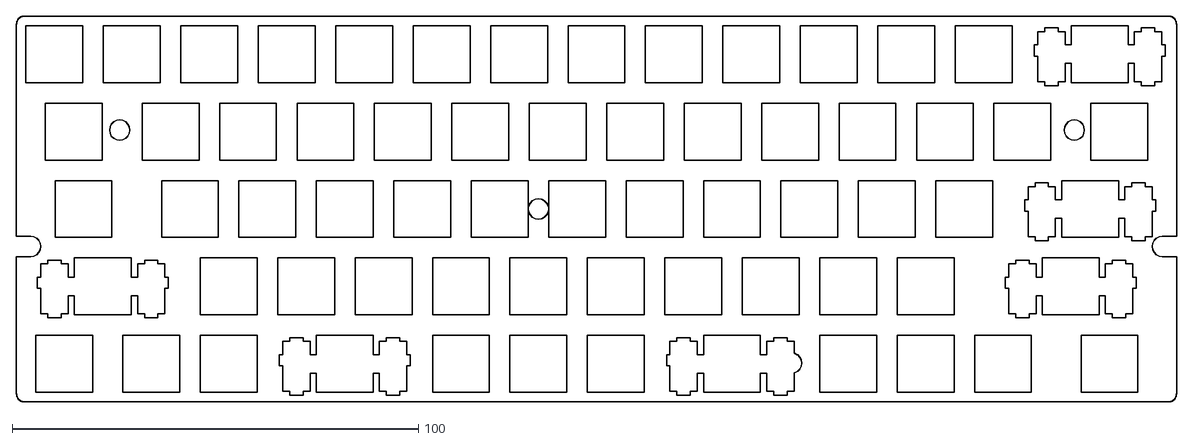
[picture p148: CAD file, 2022-12-10]
PCB/Think60/think60plate.dxf
285.4 x 94.9
