xcl666/trackpoint-mechanical-keyboard/PCB/think84/7月28日开源文件/7月28日开源文件/40配列定位板.dxf

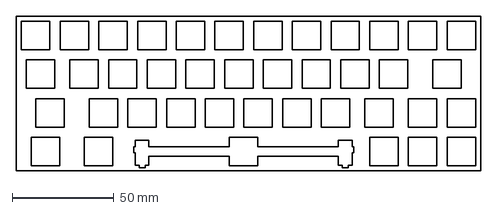
[picture p149: CAD file, 2022-12-10]
PCB/think84/7月28日开源文件/7月28日开源文件/40配列定位板.dxf
228.6 x 76.2 mm
