xcl666/trackpoint-mechanical-keyboard/PCB/think84/formal/bottom.dxf

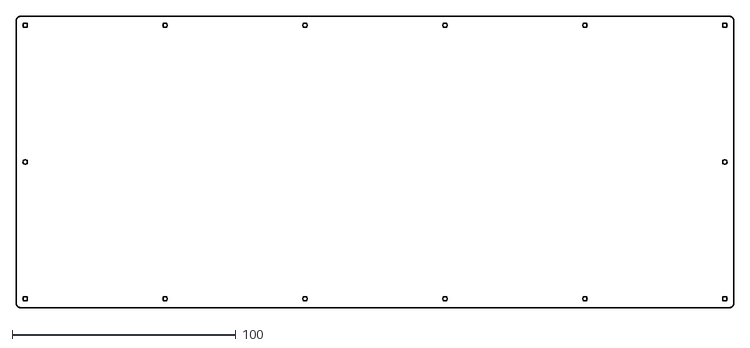
[picture p150: CAD file, 2022-12-10]
PCB/think84/formal/bottom.dxf
320.8 x 130.3
