xcl666/trackpoint-mechanical-keyboard/PCB/tp60/3dshell/60壳.stl

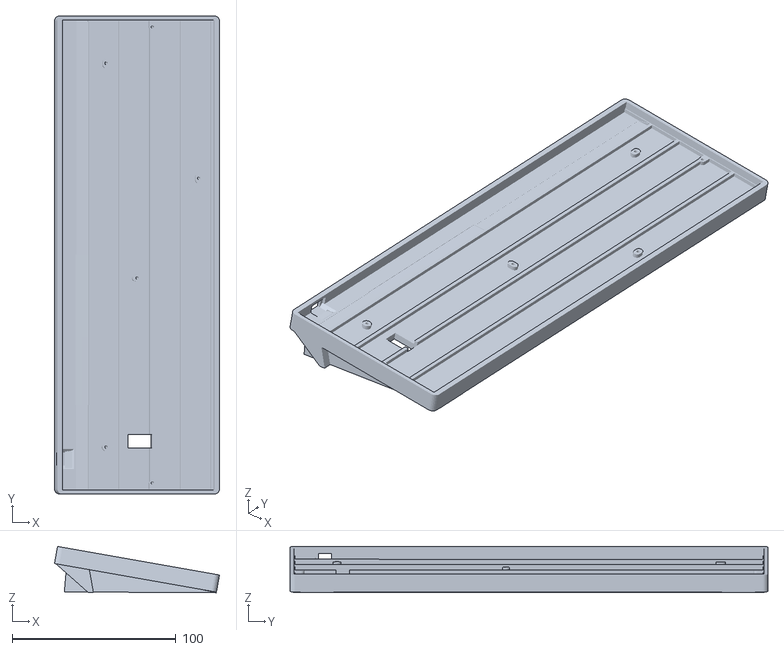
[picture p151: CAD file, 2022-12-10]
PCB/tp60/3dshell/60壳.stl
100.8 x 292.0 x 28.2
