xcl666/trackpoint-mechanical-keyboard/PCB/tp60/cnc/左移64开槽.dxf

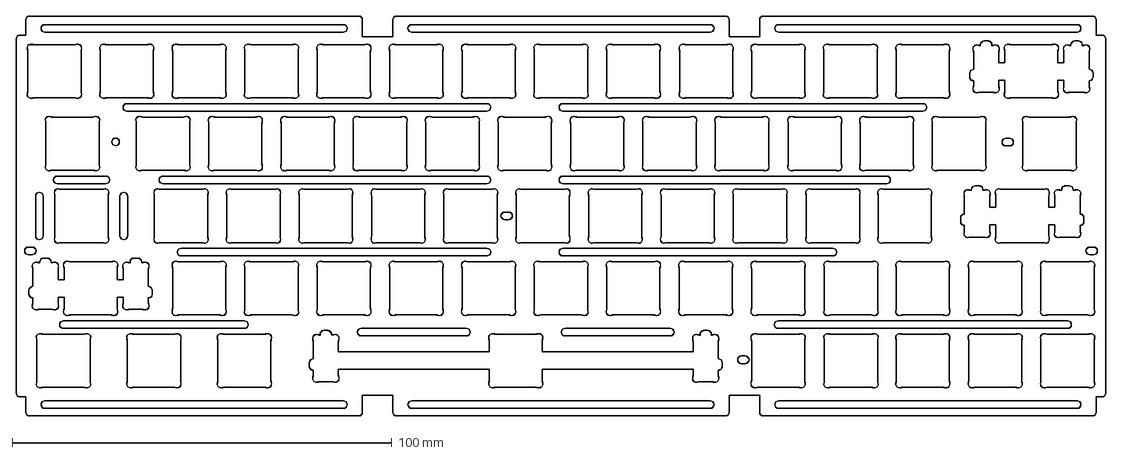
[picture p152: CAD file, 2022-12-10]
PCB/tp60/cnc/左移64开槽.dxf
286.7 x 105.2 mm
