xcl666/trackpoint-mechanical-keyboard/PCB/tp60/gasket/bottom.dxf

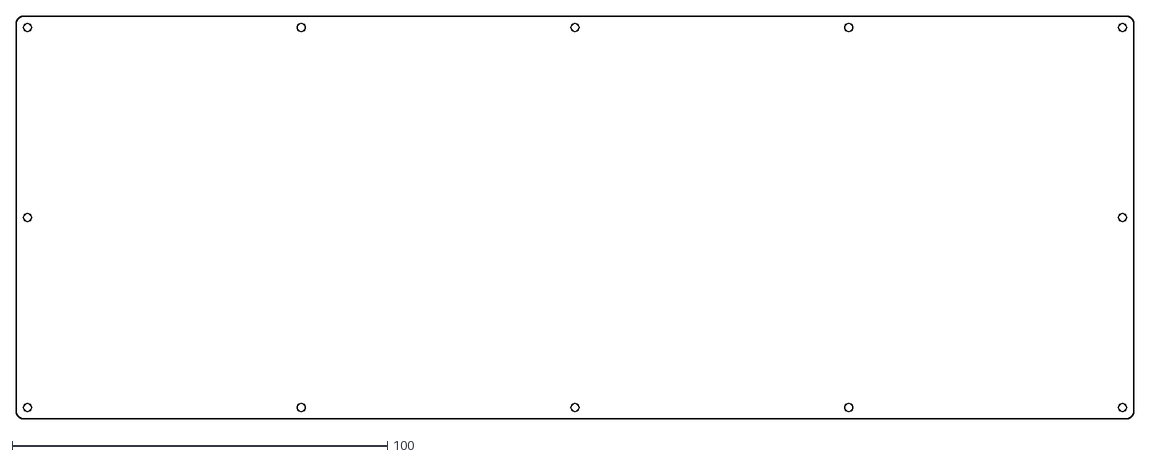
[picture p153: CAD file, 2022-12-10]
PCB/tp60/gasket/bottom.dxf
297.8 x 107.2
