xcl666/trackpoint-mechanical-keyboard/PCB/tp_threekeys/shell/零件2.SLDPRT

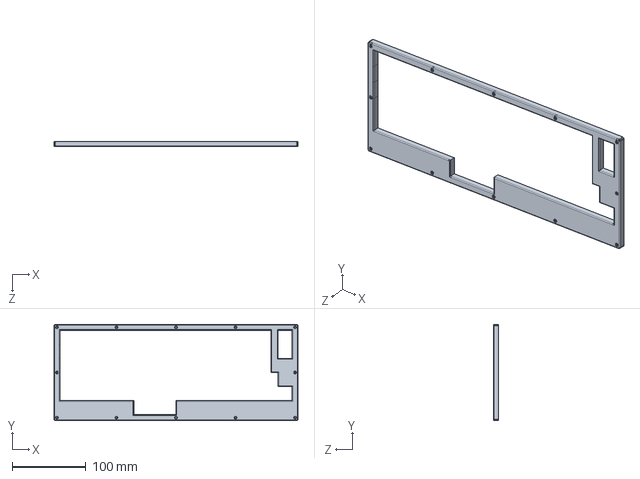
[picture p154: CAD file, 2022-12-10]
PCB/tp_threekeys/shell/零件2.SLDPRT
330.3 x 130.3 x 7.00 mm
