xcl666/trackpoint-mechanical-keyboard/PCB/tp_threekeys/tpThreeKeys.dxf

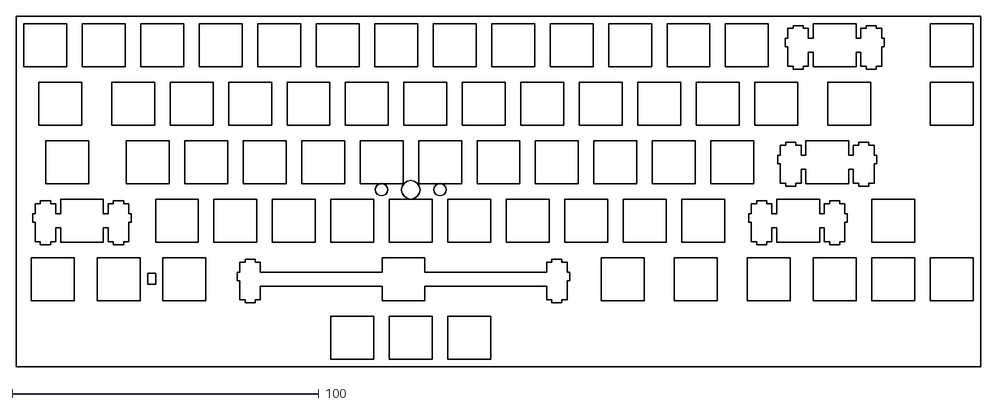
[picture p155: CAD file, 2022-12-10]
PCB/tp_threekeys/tpThreeKeys.dxf
314.3 x 114.3
