xcl666/trackpoint-mechanical-keyboard/PCB/tpec32-main/tpec32-main/stl/rod_1.STL

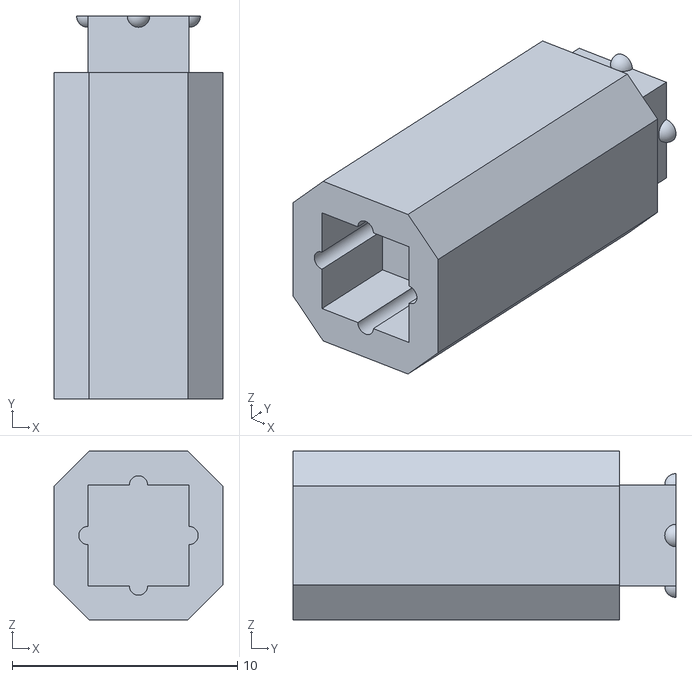
[picture p156: CAD file, 2022-12-10]
PCB/tpec32-main/tpec32-main/stl/rod_1.STL
7.50 x 17.0 x 7.50
