xcl666/trackpoint-mechanical-keyboard/PCB/tpec32-main/tpec32-main/sw/shell.SLDPRT

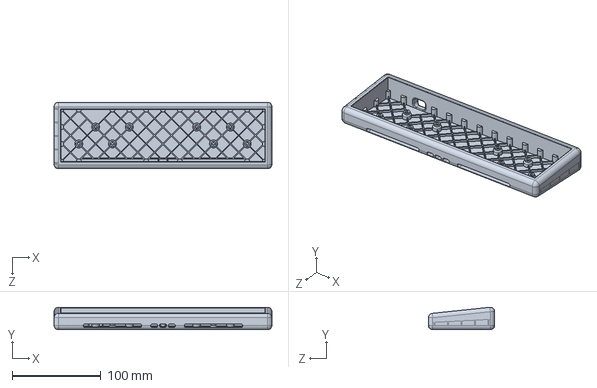
[picture p157: CAD file, 2022-12-10]
PCB/tpec32-main/tpec32-main/sw/shell.SLDPRT
246.0 x 25.3 x 75.0 mm
