xcl666/trackpoint-mechanical-keyboard/PCB/tppad/3d/上盖.step

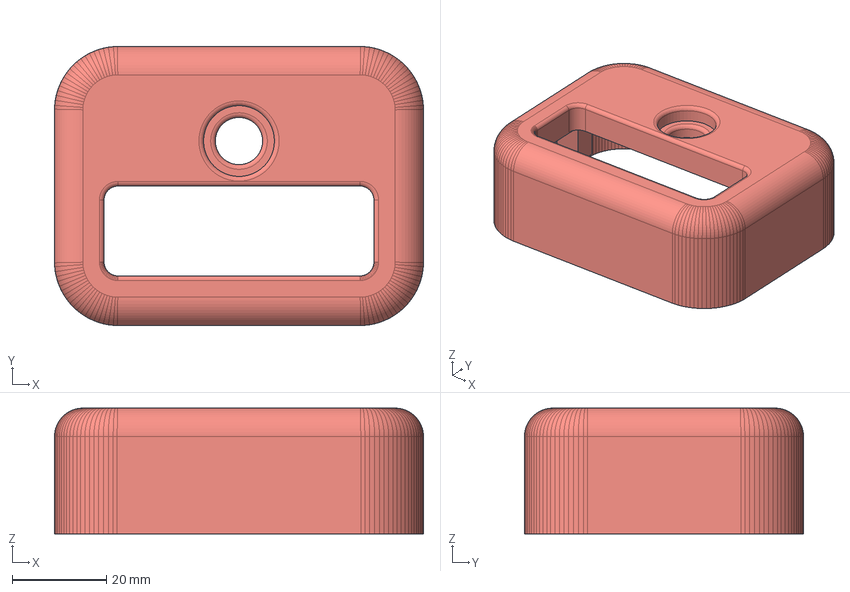
[picture p158: CAD file, 2022-12-10]
PCB/tppad/3d/上盖.step
78.2 x 59.1 x 26.6 mm
