xcl666/trackpoint-mechanical-keyboard/PCB/tppad/3dv1/定位板.STEP

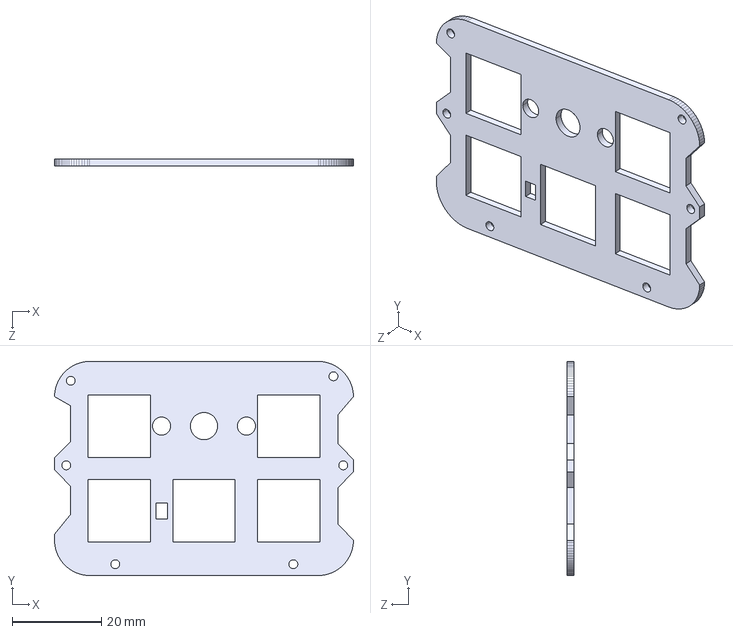
[picture p159: CAD file, 2022-12-10]
PCB/tppad/3dv1/定位板.STEP
67.2 x 48.1 x 1.60 mm
