xcl666/trackpoint-mechanical-keyboard/PCB/tppad/3dv2/定位板.STEP

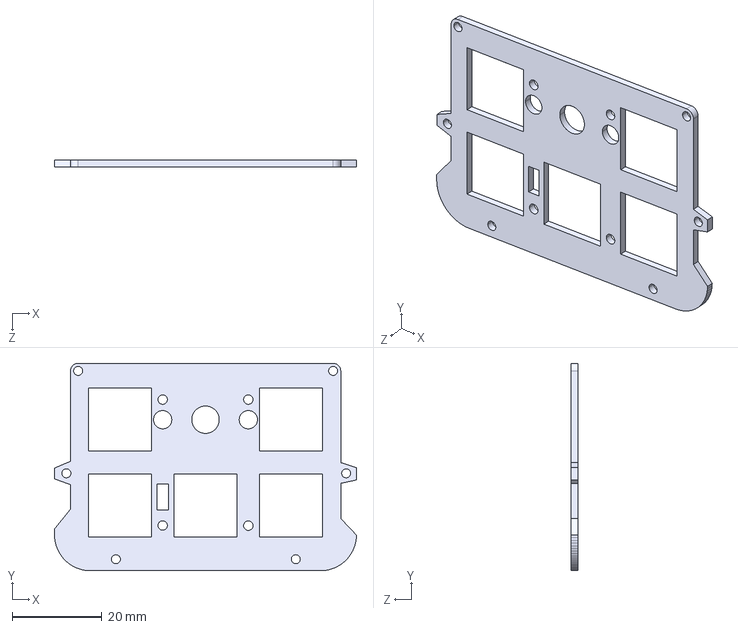
[picture p160: CAD file, 2022-12-10]
PCB/tppad/3dv2/定位板.STEP
67.2 x 46.1 x 1.50 mm
