xcl666/trackpoint-mechanical-keyboard/PCB/tppad/pcbv1.dxf

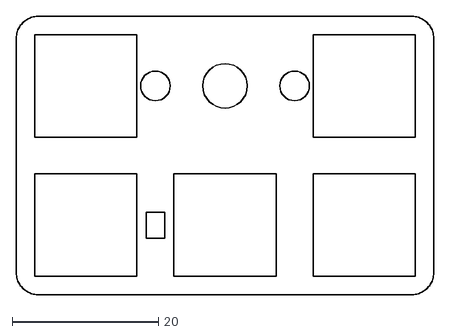
[picture p161: CAD file, 2022-12-10]
PCB/tppad/pcbv1.dxf
57.2 x 38.1
