xcl666/trackpoint-mechanical-keyboard/PCB/TP键盘升级包/TP键盘升级包/底座CAD/base_x41_u_5mm.DXF

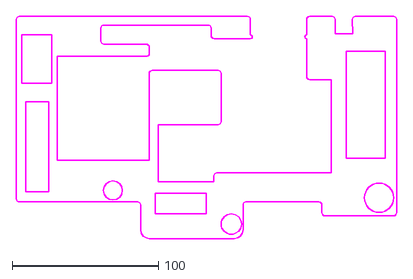
[picture p162: CAD file, 2022-12-10]
PCB/TP键盘升级包/TP键盘升级包/底座CAD/base_x41_u_5mm.DXF
260.0 x 152.0
