xcl666/trackpoint-mechanical-keyboard/PCB/trackpoint/interesting/轨迹球板外壳/3个文件/3个文件/shell_2_of_鼠标底盖.stl

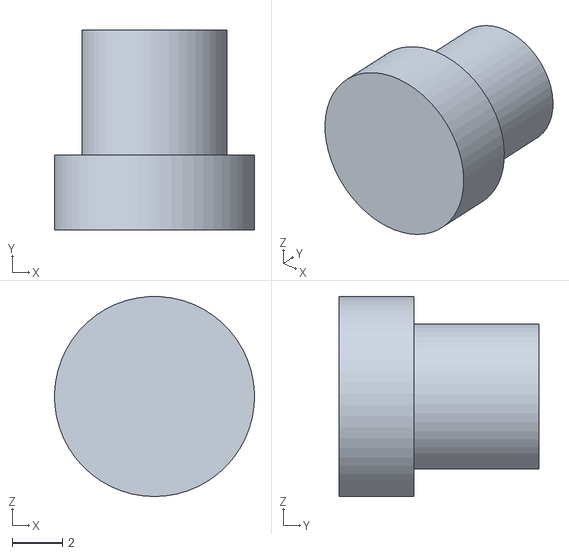
[picture p163: CAD file, 2022-12-10]
PCB/trackpoint/interesting/轨迹球板外壳/3个文件/3个文件/shell_2_of_鼠标底盖.stl
8.00 x 8.00 x 8.00
