xcl666/trackpoint-mechanical-keyboard/PCB/trackpoint/interesting/轨迹球板外壳/鼠标.STL

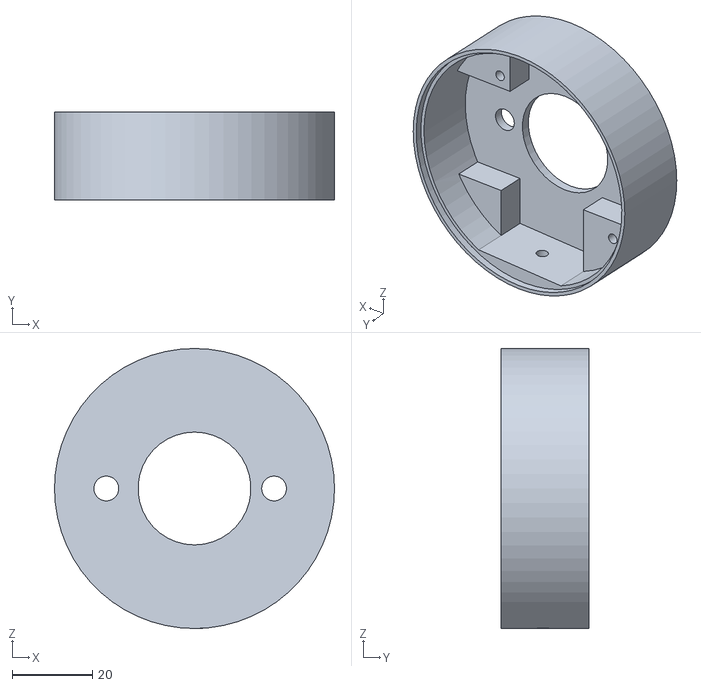
[picture p164: CAD file, 2022-12-10]
PCB/trackpoint/interesting/轨迹球板外壳/鼠标.STL
70.0 x 22.0 x 70.0
