xcl666/trackpoint-mechanical-keyboard/PCB/trackpoint/own.SLDPRT

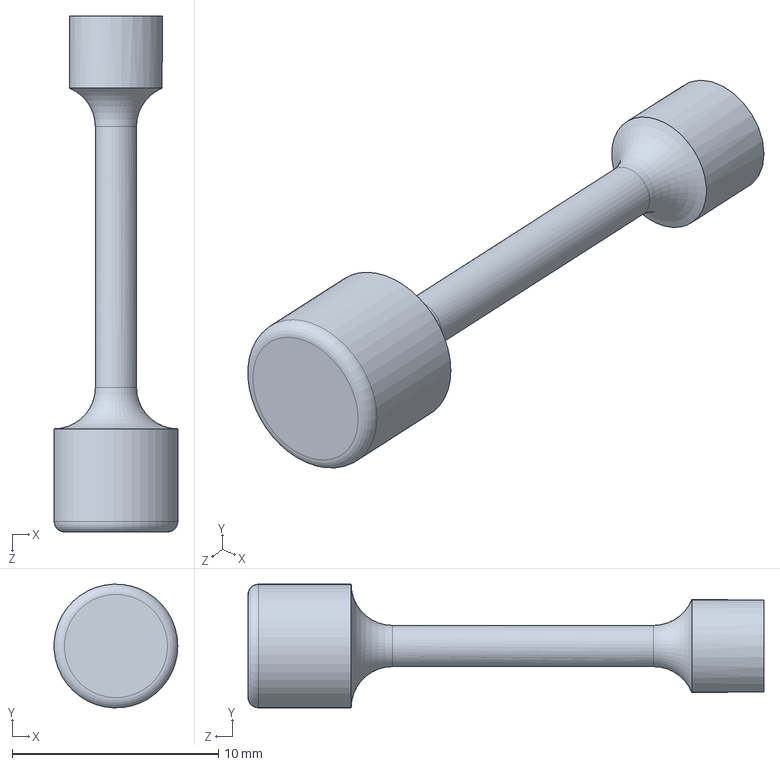
[picture p165: CAD file, 2022-12-10]
PCB/trackpoint/own.SLDPRT
5.99 x 6.00 x 25.0 mm
