xcl666/trackpoint-mechanical-keyboard/PCB/trackpoint/product/275stick.SLDPRT

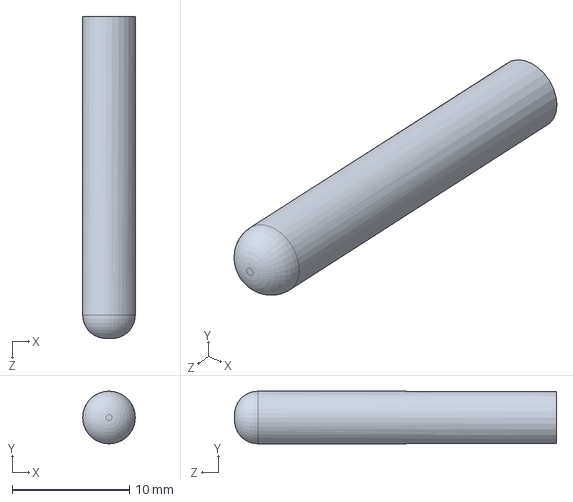
[picture p166: CAD file, 2022-12-10]
PCB/trackpoint/product/275stick.SLDPRT
4.50 x 4.50 x 27.5 mm
