xcl666/trackpoint-mechanical-keyboard/PCB/12x6/pcb.dxf

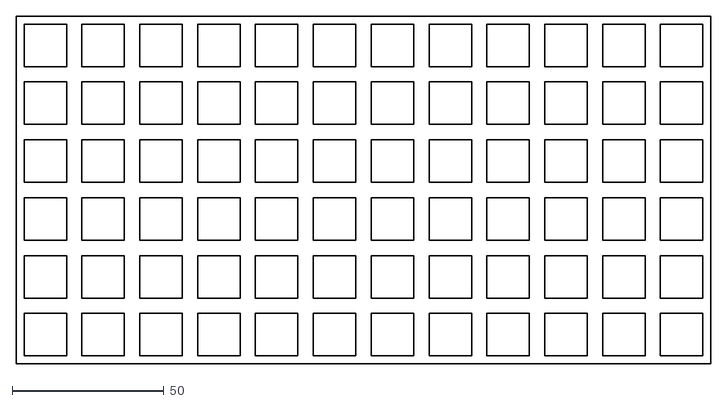
[picture p168: CAD file, 2022-12-10]
PCB/12x6/pcb.dxf
228.6 x 114.3
