xcl666/trackpoint-mechanical-keyboard/PCB/12x6/shell/plate.dxf

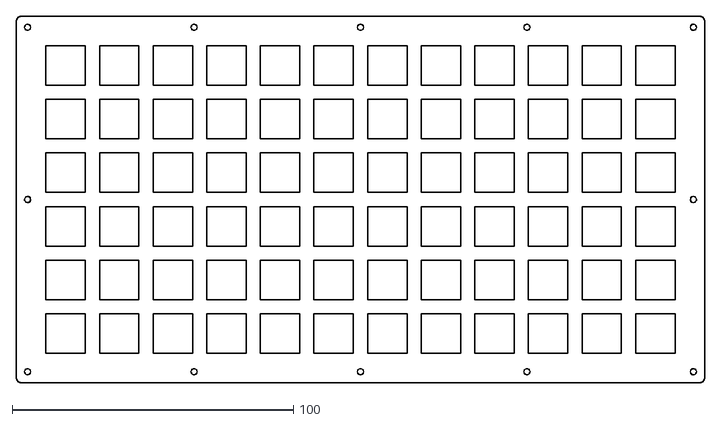
[picture p169: CAD file, 2022-12-10]
PCB/12x6/shell/plate.dxf
244.6 x 130.3
