xcl666/trackpoint-mechanical-keyboard/PCB/18x6/pcb.dxf

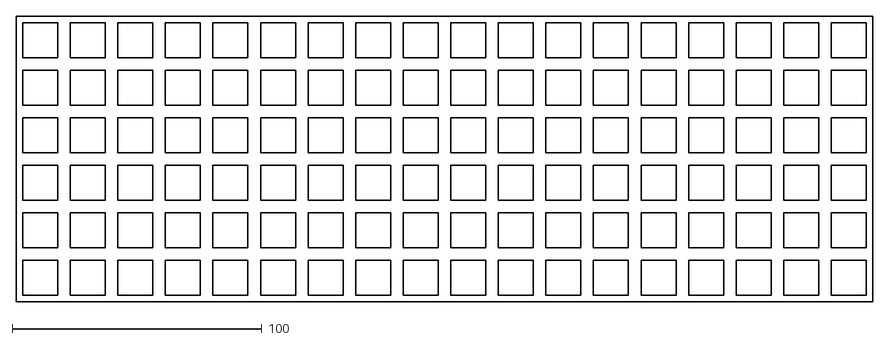
[picture p170: CAD file, 2022-12-10]
PCB/18x6/pcb.dxf
342.9 x 114.3
