xcl666/trackpoint-mechanical-keyboard/PCB/3x10/3D/30定位板v1.dxf

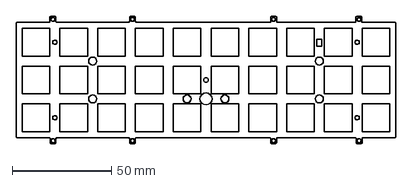
[picture p171: CAD file, 2022-12-10]
PCB/3x10/3D/30定位板v1.dxf
191.4 x 64.1 mm
