xcl666/trackpoint-mechanical-keyboard/PCB/3x10/pcbv2 - Copy.dxf

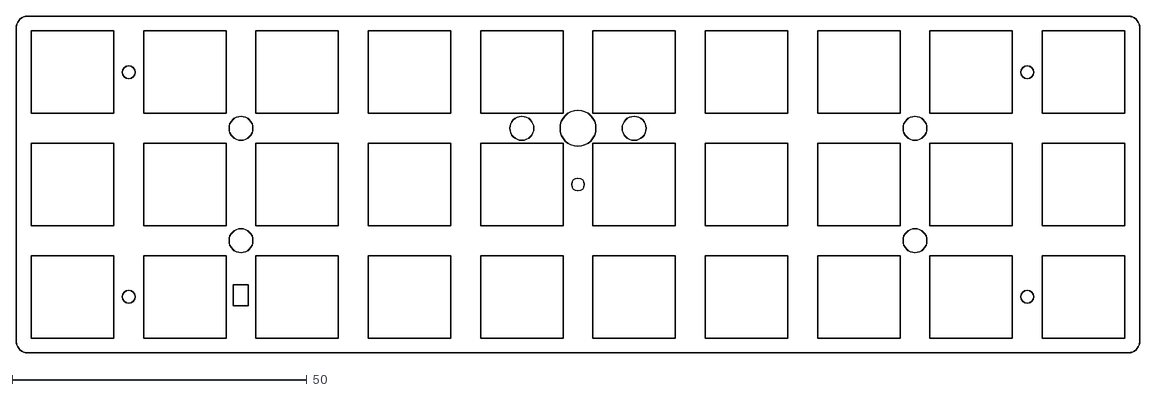
[picture p172: CAD file, 2022-12-10]
PCB/3x10/pcbv2 - Copy.dxf
190.5 x 57.2
