xcl666/trackpoint-mechanical-keyboard/PCB/3x10/shell/2013/openV1.dxf

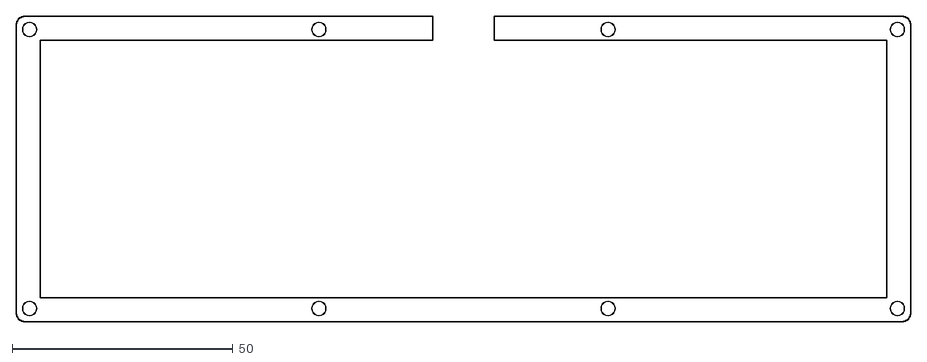
[picture p173: CAD file, 2022-12-10]
PCB/3x10/shell/2013/openV1.dxf
202.5 x 69.2
