xcl666/trackpoint-mechanical-keyboard/PCB/4x14/4x14pcb.dxf

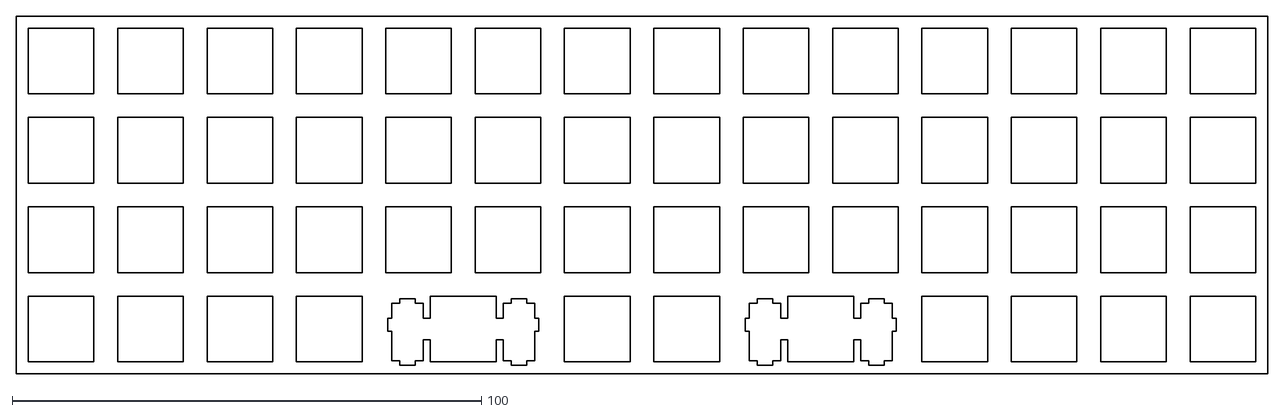
[picture p175: CAD file, 2022-12-10]
PCB/4x14/4x14pcb.dxf
266.7 x 76.2
