xcl666/trackpoint-mechanical-keyboard/PCB/4x14/shell/1u配列船.STEP

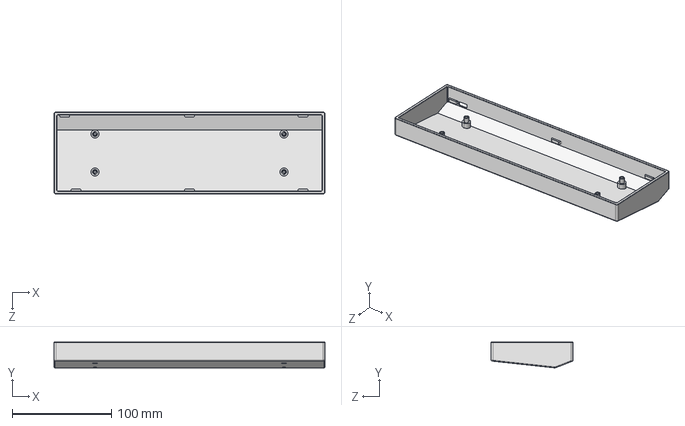
[picture p176: CAD file, 2022-12-10]
PCB/4x14/shell/1u配列船.STEP
273.1 x 25.9 x 82.6 mm
