xcl666/trackpoint-mechanical-keyboard/PCB/6x12Threekeys/switchlast.dxf

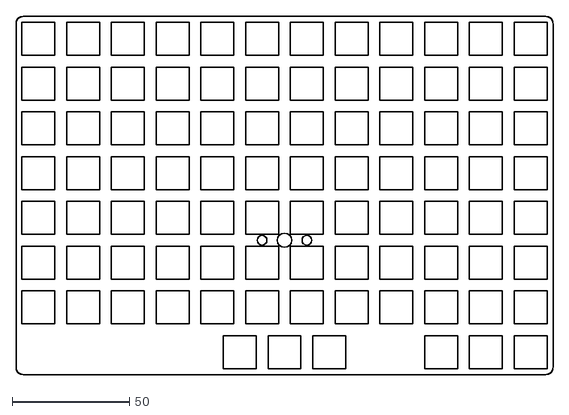
[picture p177: CAD file, 2022-12-10]
PCB/6x12Threekeys/switchlast.dxf
228.6 x 152.4
