xcl666/trackpoint-mechanical-keyboard/PCB/alice/3D/myown/new/上壳.SLDPRT

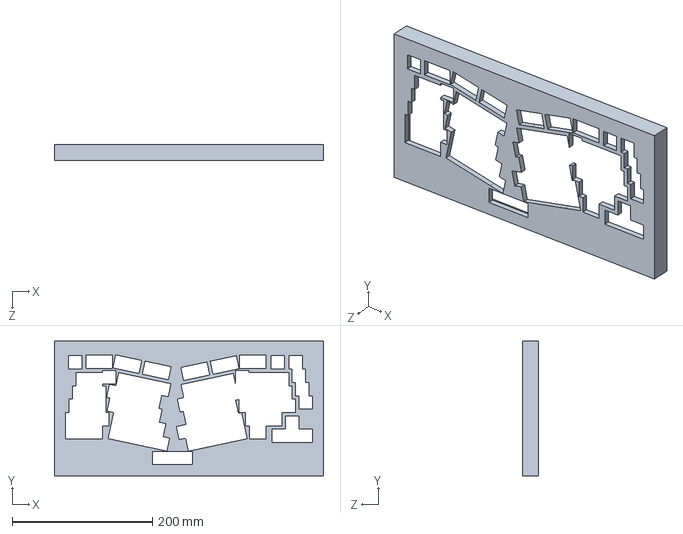
[picture p178: CAD file, 2022-12-10]
PCB/alice/3D/myown/new/上壳.SLDPRT
383.5 x 192.0 x 23.5 mm
