xcl666/trackpoint-mechanical-keyboard/PCB/alice/3D/TA底壳.step

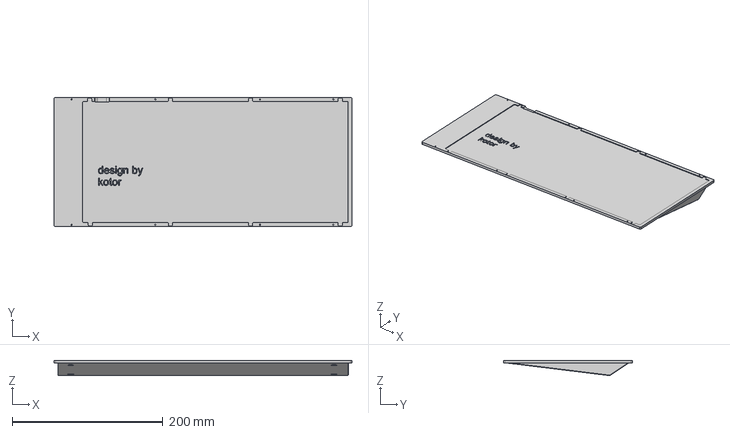
[picture p179: CAD file, 2022-12-10]
PCB/alice/3D/TA底壳.step
395.9 x 171.4 x 20.2 mm
