xcl666/trackpoint-mechanical-keyboard/PCB/alice/adelheid/adelheid-master/adelheid-master/case/foam/d16f64ecda69f43c41b6820d0f6a7fc9f048dfed_switch.dxf

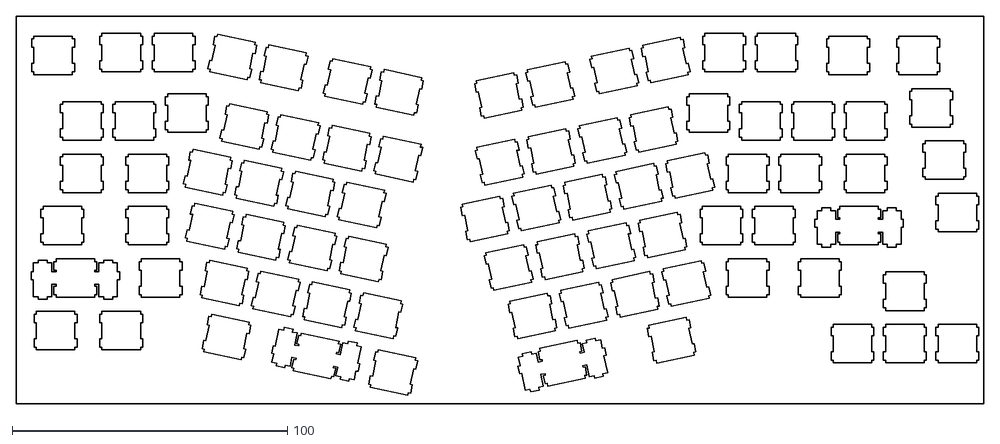
[picture p180: CAD file, 2022-12-10]
PCB/alice/adelheid/adelheid-master/adelheid-master/case/foam/d16f64ecda69f43c41b6820d0f6a7fc9f048dfed_switch.dxf
351.5 x 141.0
