xcl666/trackpoint-mechanical-keyboard/PCB/alice/adelheid/adelheid-master/adelheid-master/case/lasercut-layers/z_hipro_layers_600x600.dxf

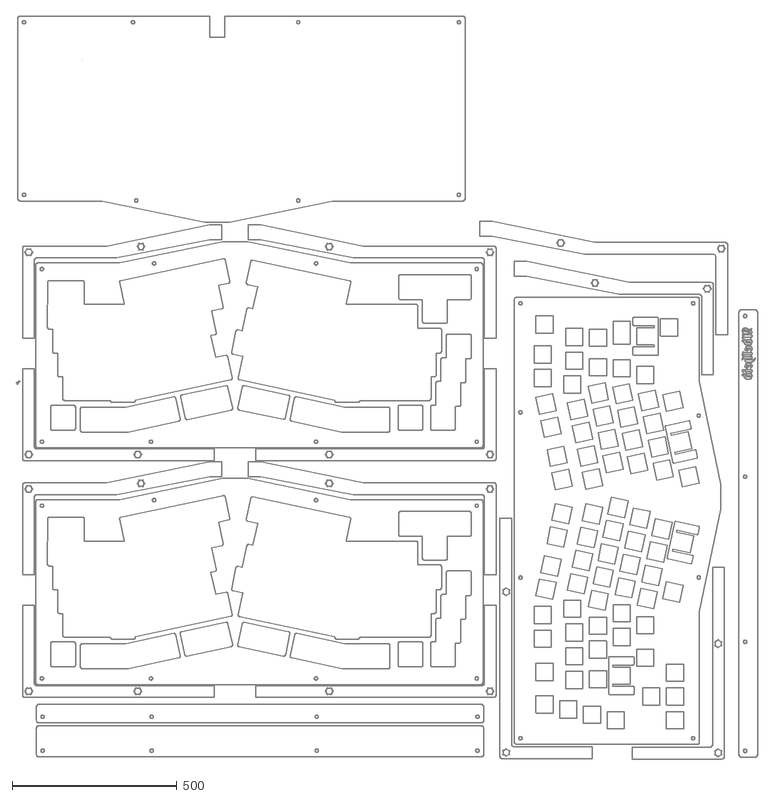
[picture p181: CAD file, 2022-12-10]
PCB/alice/adelheid/adelheid-master/adelheid-master/case/lasercut-layers/z_hipro_layers_600x600.dxf
2248.5 x 2254.0
