xcl666/trackpoint-mechanical-keyboard/PCB/alice/Kolibri/Kolibri-main/Kolibri-main/Case/05 Case edges.dxf

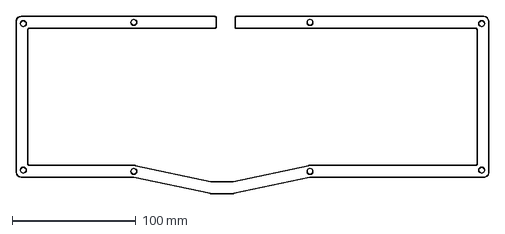
[picture p182: CAD file, 2022-12-10]
PCB/alice/Kolibri/Kolibri-main/Kolibri-main/Case/05 Case edges.dxf
381.4 x 142.8 mm
