xcl666/trackpoint-mechanical-keyboard/PCB/alice/shell/TA1021lastswitchv1.dxf

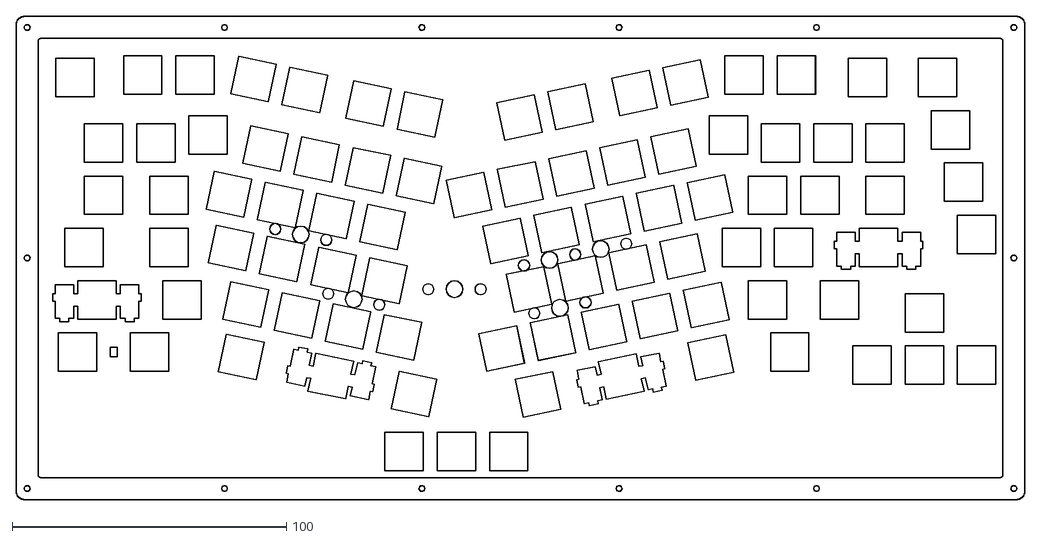
[picture p183: CAD file, 2022-12-10]
PCB/alice/shell/TA1021lastswitchv1.dxf
367.5 x 176.0
