xcl666/trackpoint-mechanical-keyboard/PCB/alice/TA1021lastswitchv1.dxf

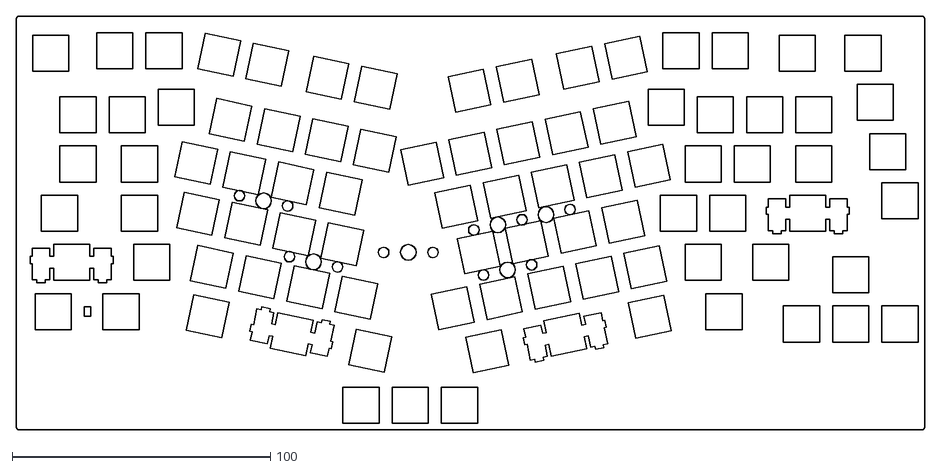
[picture p184: CAD file, 2022-12-10]
PCB/alice/TA1021lastswitchv1.dxf
351.5 x 160.0
