xcl666/trackpoint-mechanical-keyboard/PCB/Think60/think60platev1.dxf

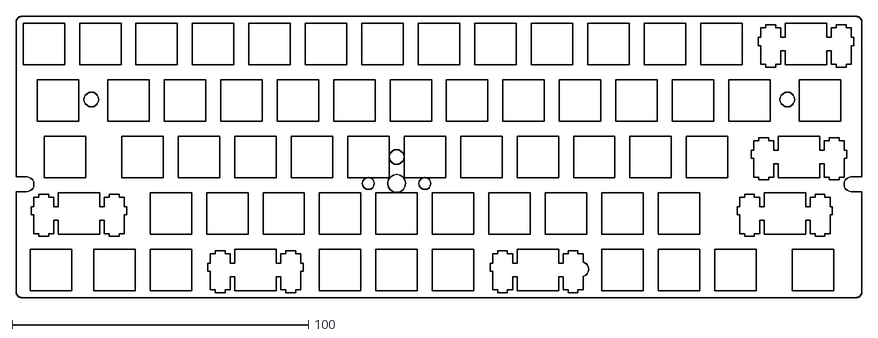
[picture p185: CAD file, 2022-12-10]
PCB/Think60/think60platev1.dxf
285.4 x 94.9
