xcl666/trackpoint-mechanical-keyboard/PCB/think84/formal/toptestlastv1.dxf

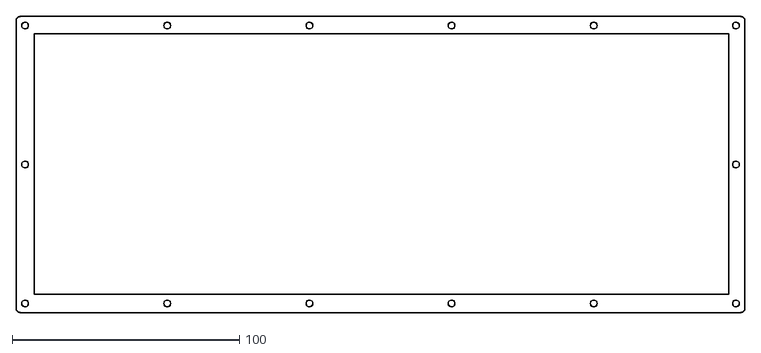
[picture p186: CAD file, 2022-12-10]
PCB/think84/formal/toptestlastv1.dxf
320.8 x 130.3
