xcl666/trackpoint-mechanical-keyboard/PCB/think84/opentest.dxf

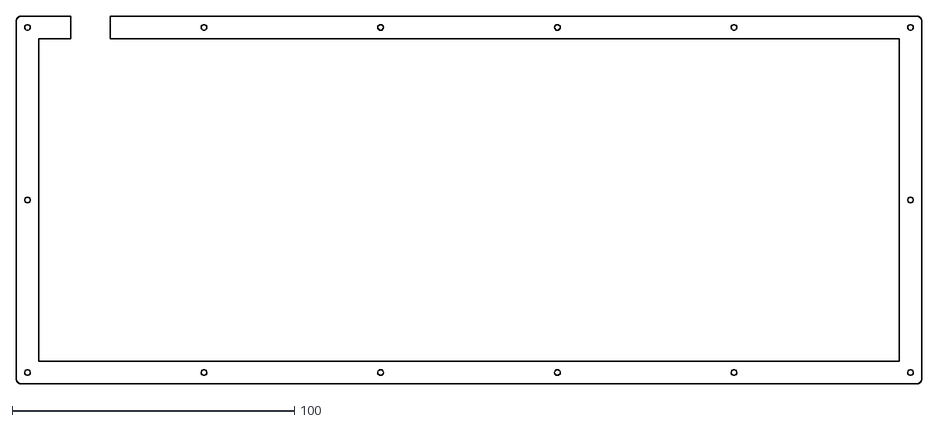
[picture p187: CAD file, 2022-12-10]
PCB/think84/opentest.dxf
320.8 x 130.3
