xcl666/trackpoint-mechanical-keyboard/PCB/tp60/gasket/switch.dxf

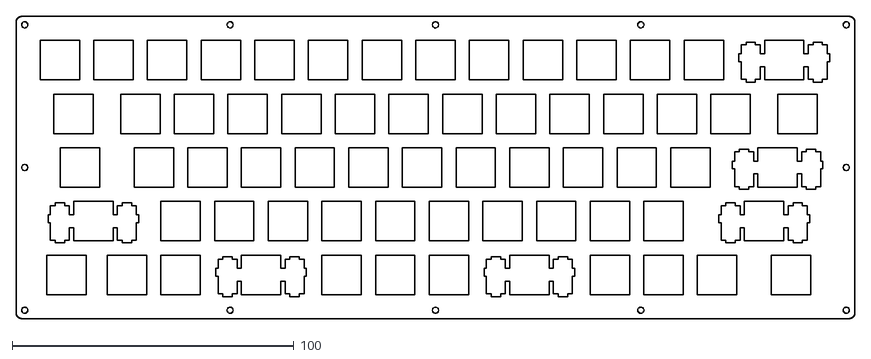
[picture p189: CAD file, 2022-12-10]
PCB/tp60/gasket/switch.dxf
297.8 x 107.2
