xcl666/trackpoint-mechanical-keyboard/PCB/tp_threekeys/shell/closed.dxf

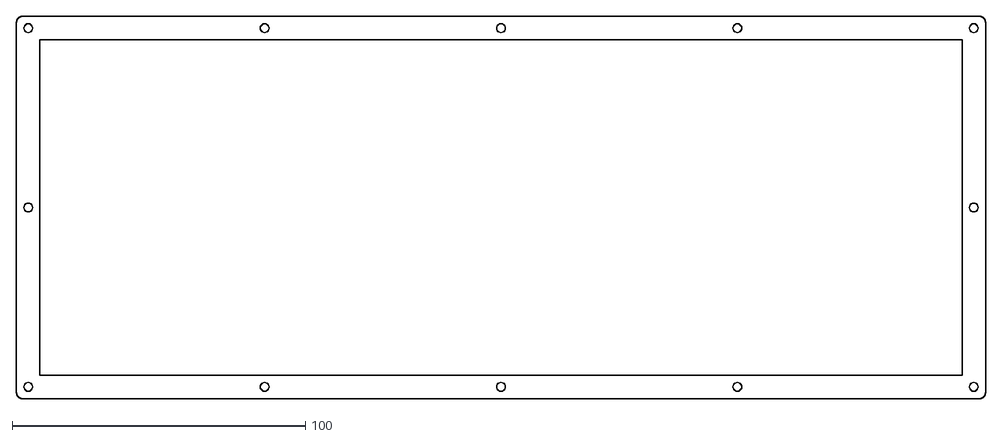
[picture p190: CAD file, 2022-12-10]
PCB/tp_threekeys/shell/closed.dxf
330.3 x 130.3
