xcl666/trackpoint-mechanical-keyboard/PCB/tpec32-main/tpec32-main/sw/knob.SLDPRT

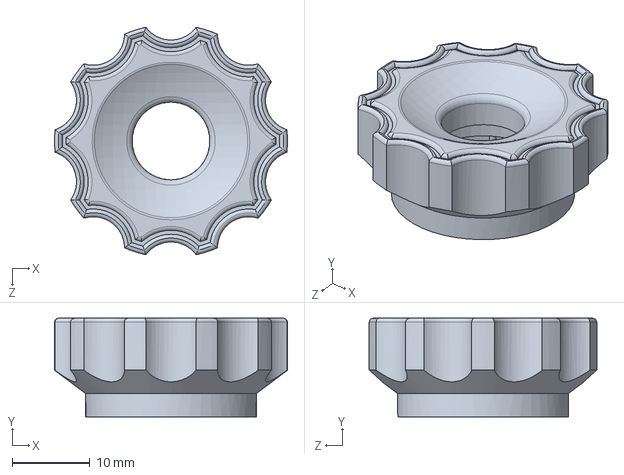
[picture p191: CAD file, 2022-12-10]
PCB/tpec32-main/tpec32-main/sw/knob.SLDPRT
30.0 x 12.7 x 29.3 mm
