xcl666/trackpoint-mechanical-keyboard/PCB/tppad/3dv1/定位板v1.STEP

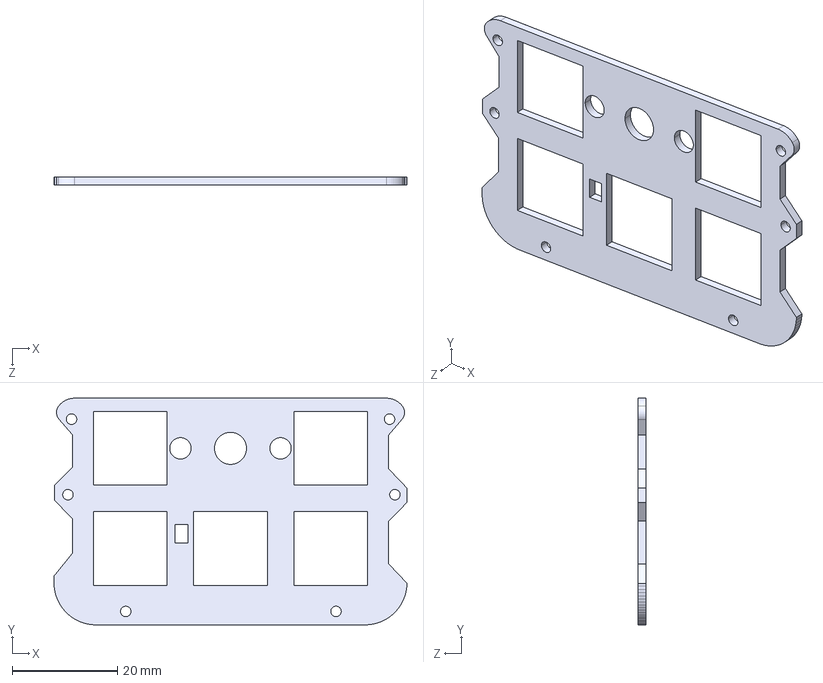
[picture p192: CAD file, 2022-12-10]
PCB/tppad/3dv1/定位板v1.STEP
67.2 x 43.1 x 1.50 mm
