xcl666/trackpoint-mechanical-keyboard/PCB/tppad/3dv2/红点定位板 右.dxf

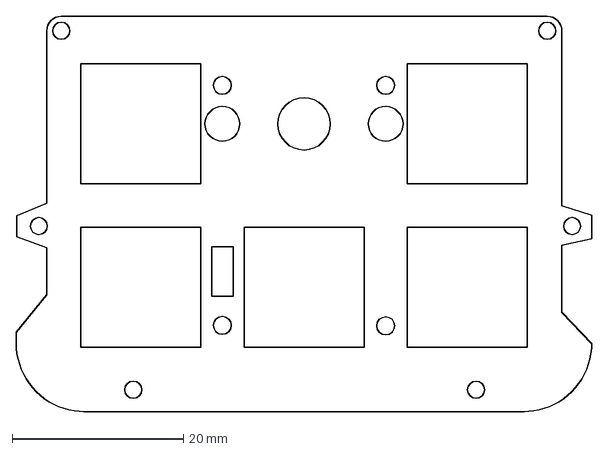
[picture p193: CAD file, 2022-12-10]
PCB/tppad/3dv2/红点定位板 右.dxf
67.2 x 46.1 mm
