xcl666/trackpoint-mechanical-keyboard/PCB/tppad/pcb.dxf

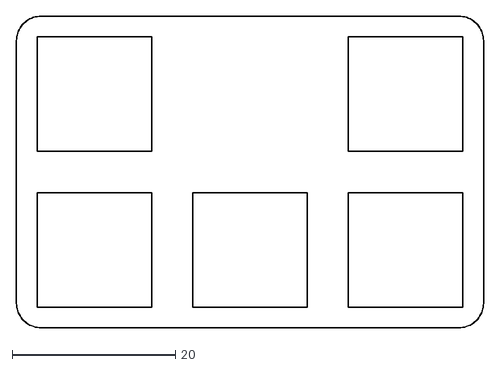
[picture p194: CAD file, 2022-12-10]
PCB/tppad/pcb.dxf
57.2 x 38.1
