xcl666/trackpoint-mechanical-keyboard/PCB/TP键盘升级包/TP键盘升级包/底座CAD/base_t61_d_2mm.DXF

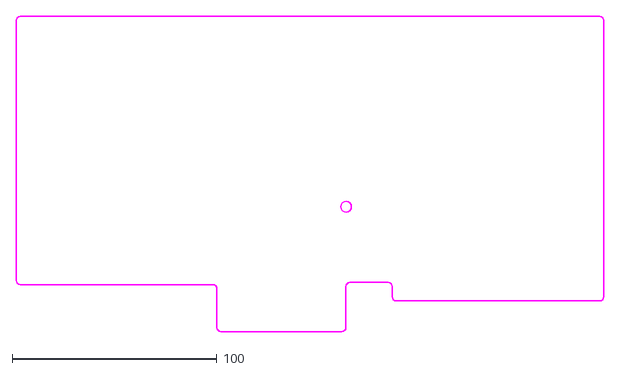
[picture p195: CAD file, 2022-12-10]
PCB/TP键盘升级包/TP键盘升级包/底座CAD/base_t61_d_2mm.DXF
287.0 x 154.0
