xcl666/trackpoint-mechanical-keyboard/PCB/trackpoint/interesting/轨迹球板外壳/鼠标底盖.STL

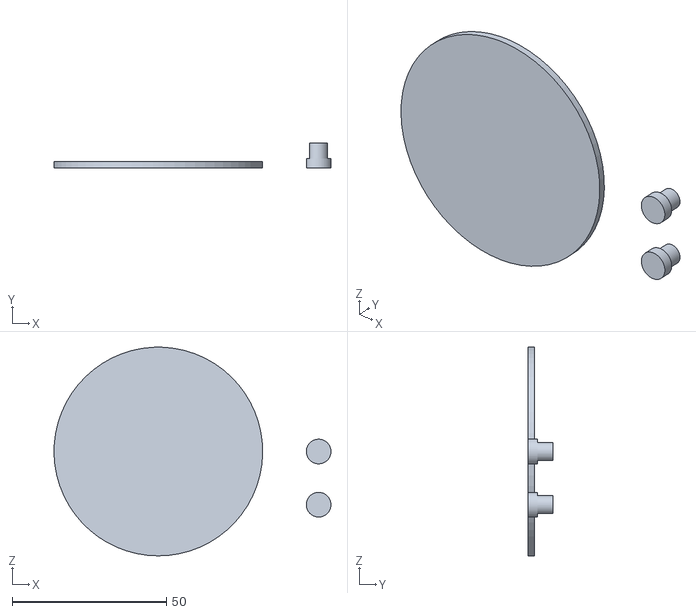
[picture p196: CAD file, 2022-12-10]
PCB/trackpoint/interesting/轨迹球板外壳/鼠标底盖.STL
89.7 x 8.00 x 67.6
