xcl666/trackpoint-mechanical-keyboard/PCB/trackpoint/product/m235stick.SLDPRT

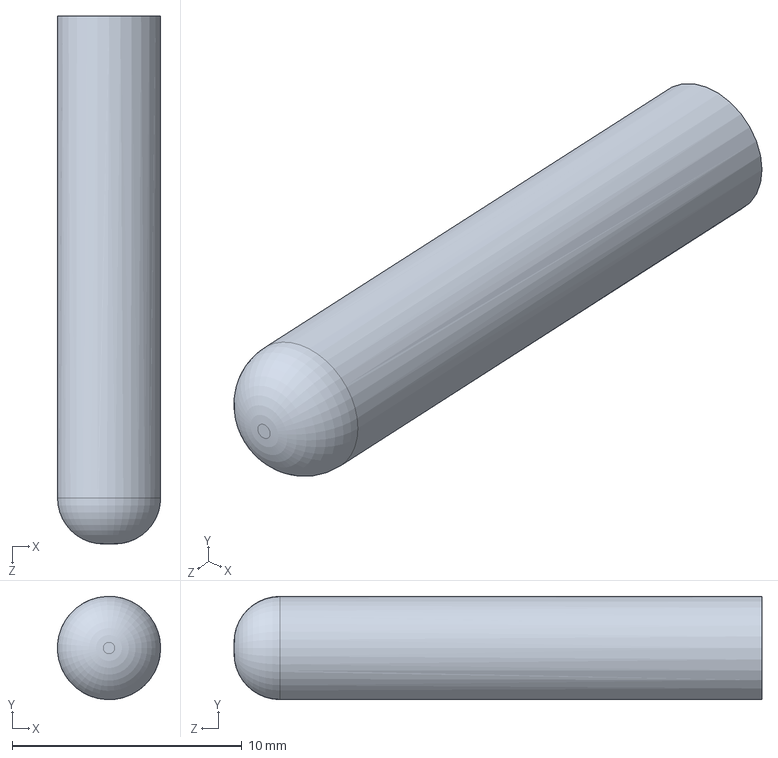
[picture p197: CAD file, 2022-12-10]
PCB/trackpoint/product/m235stick.SLDPRT
4.50 x 4.50 x 23.0 mm
