xcl666/trackpoint-mechanical-keyboard/PCB/12x6/12x6pcbV1.dxf

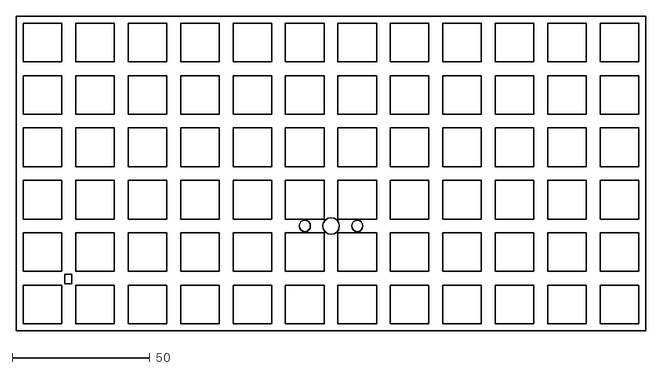
[picture p198: CAD file, 2022-12-10]
PCB/12x6/12x6pcbV1.dxf
228.6 x 114.3
