xcl666/trackpoint-mechanical-keyboard/PCB/12x6/shell/6x12switchV1.dxf

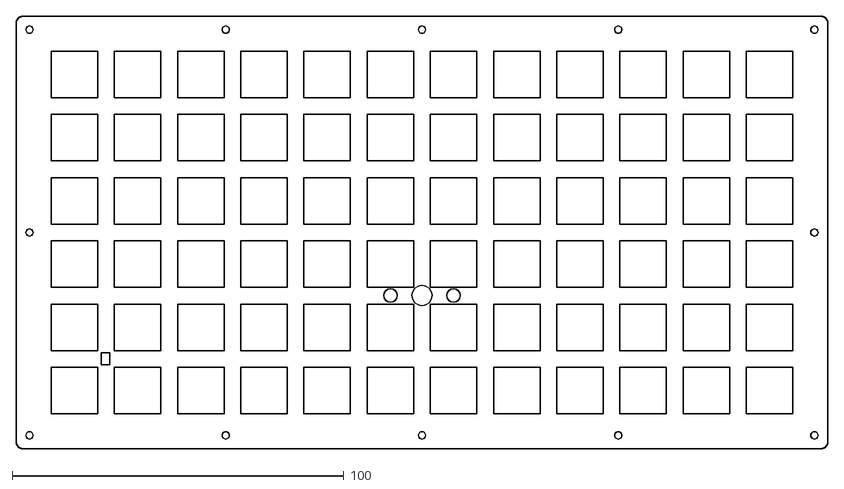
[picture p199: CAD file, 2022-12-10]
PCB/12x6/shell/6x12switchV1.dxf
244.6 x 130.3
