xcl666/trackpoint-mechanical-keyboard/PCB/3x10/3D/30定位板.dxf

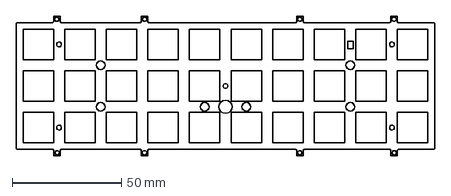
[picture p200: CAD file, 2022-12-10]
PCB/3x10/3D/30定位板.dxf
191.4 x 64.1 mm
