xcl666/trackpoint-mechanical-keyboard/PCB/3x10/closepcb.dxf

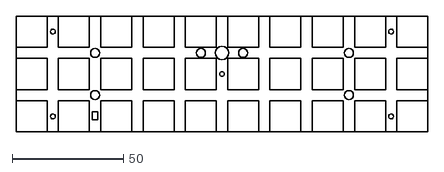
[picture p201: CAD file, 2022-12-10]
PCB/3x10/closepcb.dxf
185.4 x 52.1
