xcl666/trackpoint-mechanical-keyboard/PCB/3x10/shell/2013/3x10switchV1.dxf

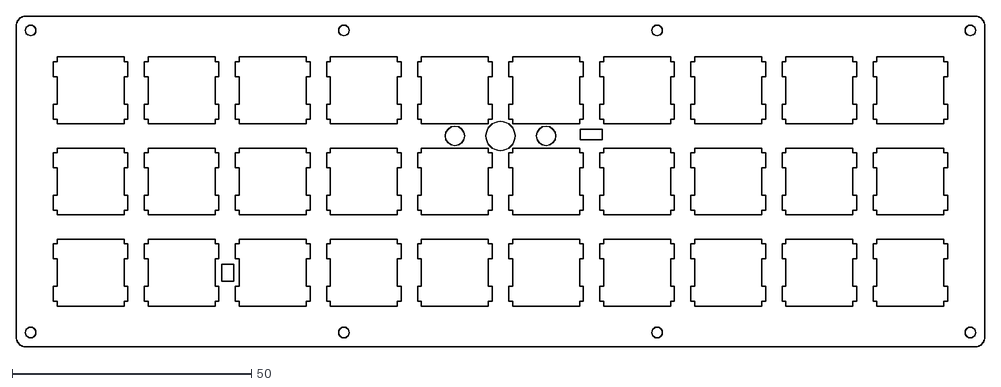
[picture p202: CAD file, 2022-12-10]
PCB/3x10/shell/2013/3x10switchV1.dxf
202.5 x 69.2
