xcl666/trackpoint-mechanical-keyboard/PCB/3x10/shell/99b5a13b30b3a3337f44358f47700b72f4264d0a_closed.dxf

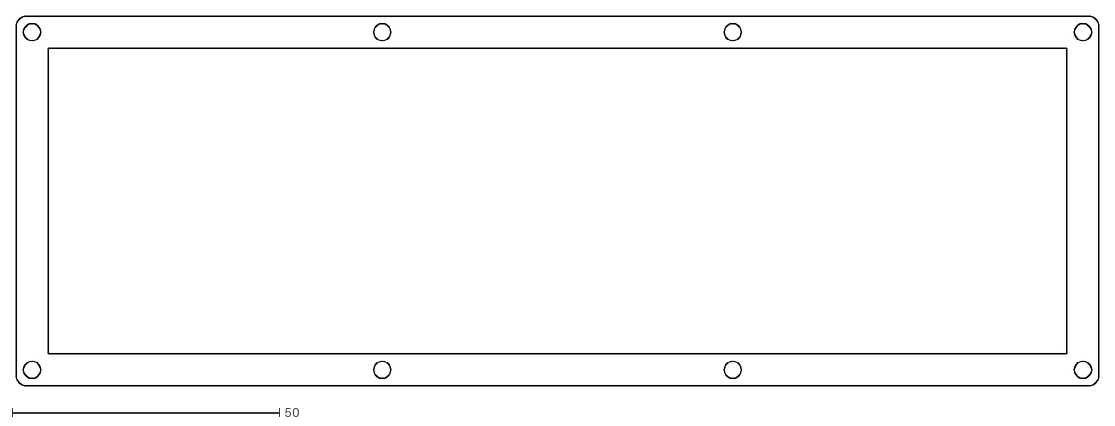
[picture p203: CAD file, 2022-12-10]
PCB/3x10/shell/99b5a13b30b3a3337f44358f47700b72f4264d0a_closed.dxf
202.5 x 69.2
