xcl666/trackpoint-mechanical-keyboard/PCB/4x14/4x14pcbV2.dxf

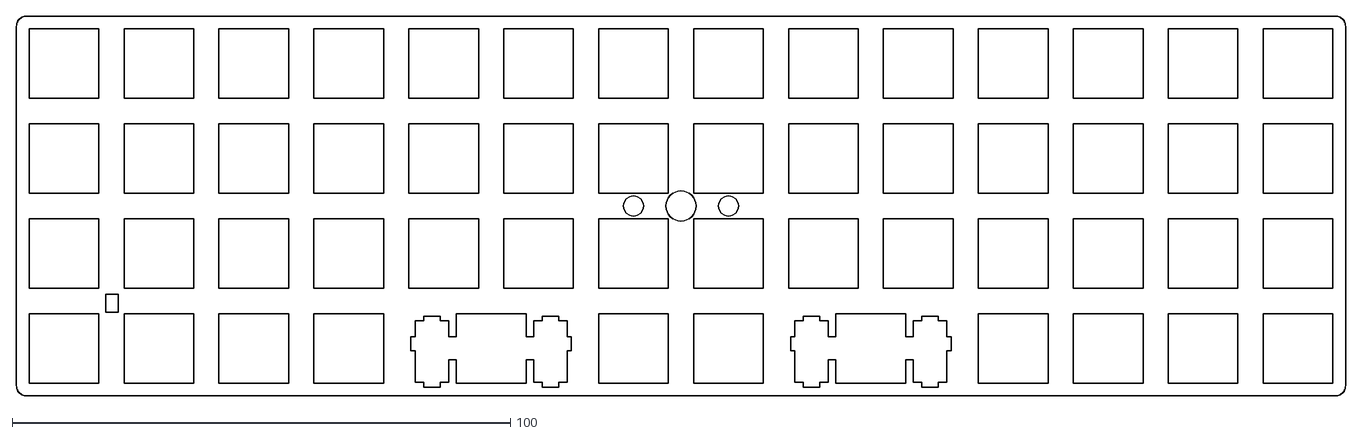
[picture p204: CAD file, 2022-12-10]
PCB/4x14/4x14pcbV2.dxf
266.7 x 76.2
