xcl666/trackpoint-mechanical-keyboard/PCB/4x14/shell/开孔后最终定位板.DXF

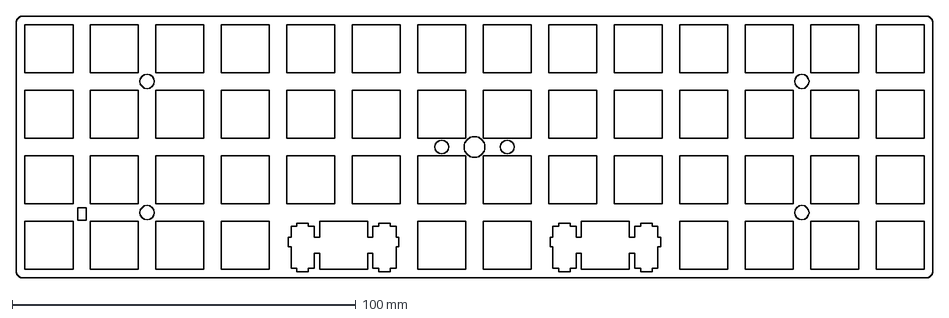
[picture p205: CAD file, 2022-12-10]
PCB/4x14/shell/开孔后最终定位板.DXF
266.7 x 76.2 mm
