xcl666/trackpoint-mechanical-keyboard/PCB/alice/3D/myown/new/夹心棉.SLDPRT

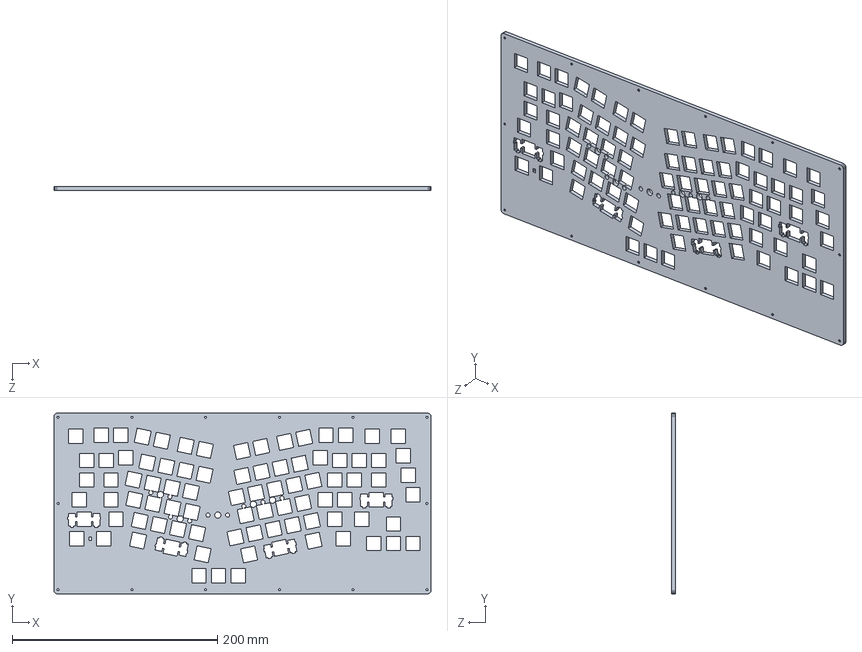
[picture p206: CAD file, 2022-12-10]
PCB/alice/3D/myown/new/夹心棉.SLDPRT
367.5 x 176.0 x 3.70 mm
