xcl666/trackpoint-mechanical-keyboard/PCB/alice/3D/myown/switch.dxf

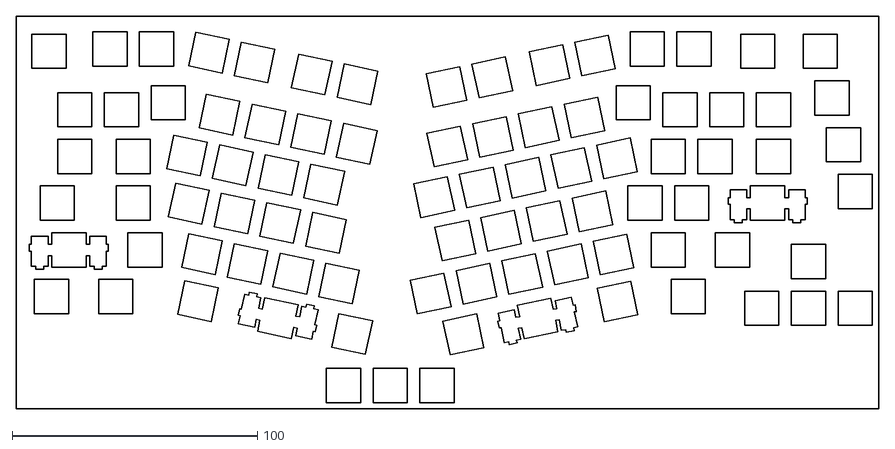
[picture p207: CAD file, 2022-12-10]
PCB/alice/3D/myown/switch.dxf
351.5 x 160.0
