xcl666/trackpoint-mechanical-keyboard/PCB/alice/88c5caf0cc8206b7d507fcfc2c8e6fd27b87e487_switchv3.dxf

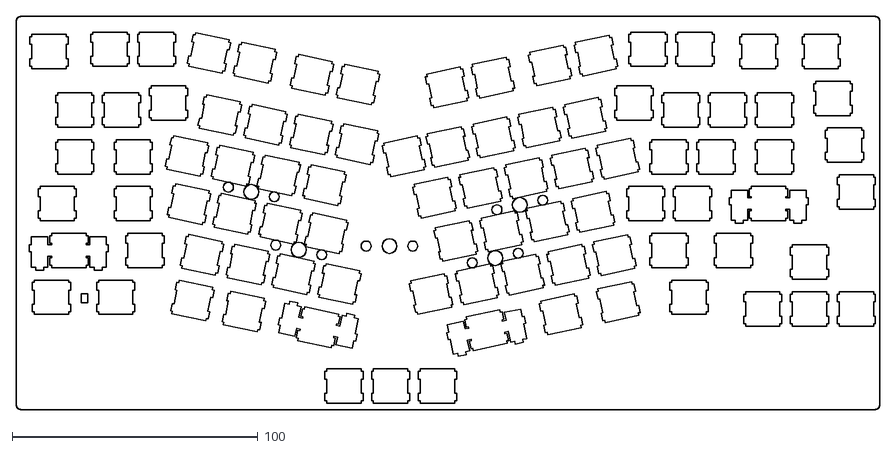
[picture p208: CAD file, 2022-12-10]
PCB/alice/88c5caf0cc8206b7d507fcfc2c8e6fd27b87e487_switchv3.dxf
351.5 x 160.0
