xcl666/trackpoint-mechanical-keyboard/PCB/alice/adelheid/adelheid-master/adelheid-master/case/lasercut-layers/lopro_layers.dxf

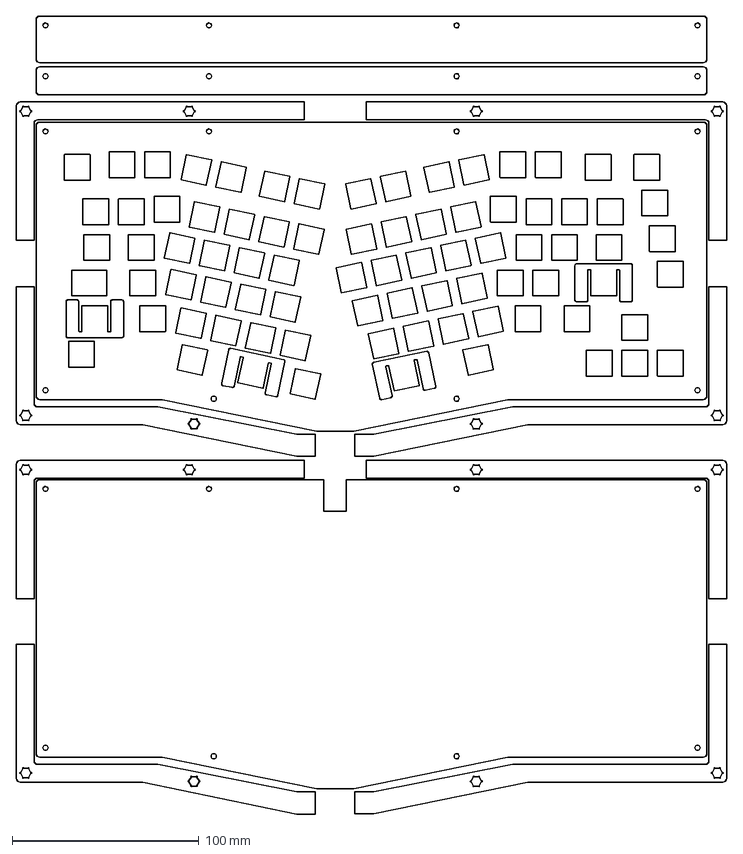
[picture p209: CAD file, 2022-12-10]
PCB/alice/adelheid/adelheid-master/adelheid-master/case/lasercut-layers/lopro_layers.dxf
380.2 x 427.2 mm
