xcl666/trackpoint-mechanical-keyboard/PCB/alice/Kolibri/Kolibri-main/Kolibri-main/Case/04 Case gasket.dxf

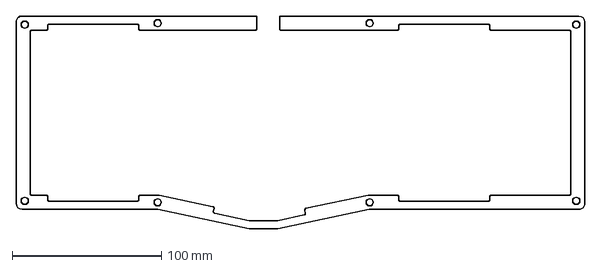
[picture p210: CAD file, 2022-12-10]
PCB/alice/Kolibri/Kolibri-main/Kolibri-main/Case/04 Case gasket.dxf
381.4 x 142.8 mm
