xcl666/trackpoint-mechanical-keyboard/PCB/alice/shell/closedV1.dxf

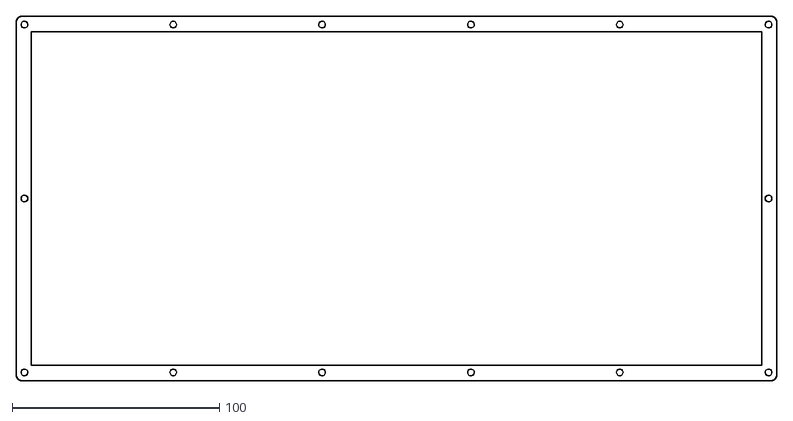
[picture p211: CAD file, 2022-12-10]
PCB/alice/shell/closedV1.dxf
367.5 x 176.0
