xcl666/trackpoint-mechanical-keyboard/PCB/think84/formal/pcb.dxf

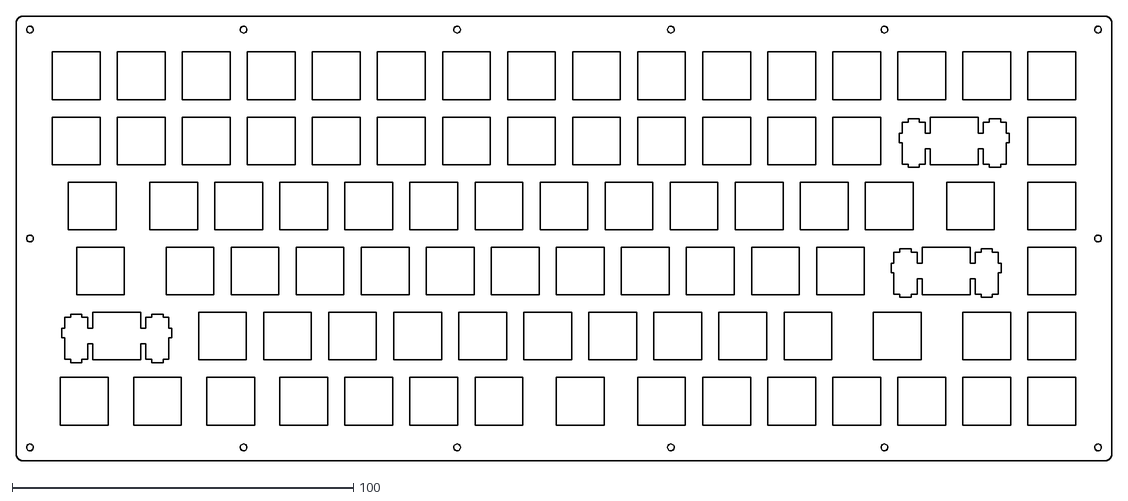
[picture p212: CAD file, 2022-12-10]
PCB/think84/formal/pcb.dxf
320.8 x 130.3
