xcl666/trackpoint-mechanical-keyboard/PCB/think84/toptest.dxf

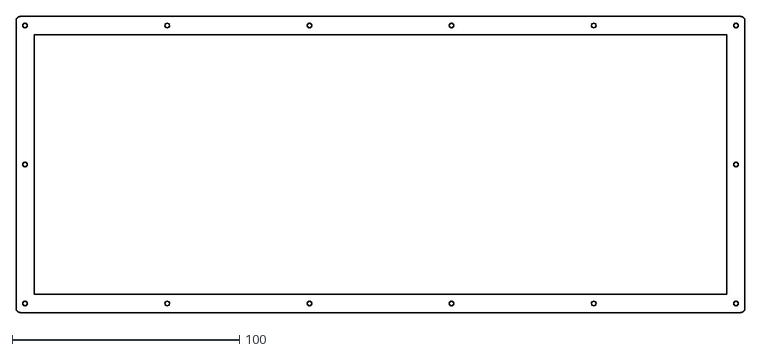
[picture p213: CAD file, 2022-12-10]
PCB/think84/toptest.dxf
320.8 x 130.3
