xcl666/trackpoint-mechanical-keyboard/PCB/tp60/gasket/pcbV1.dxf

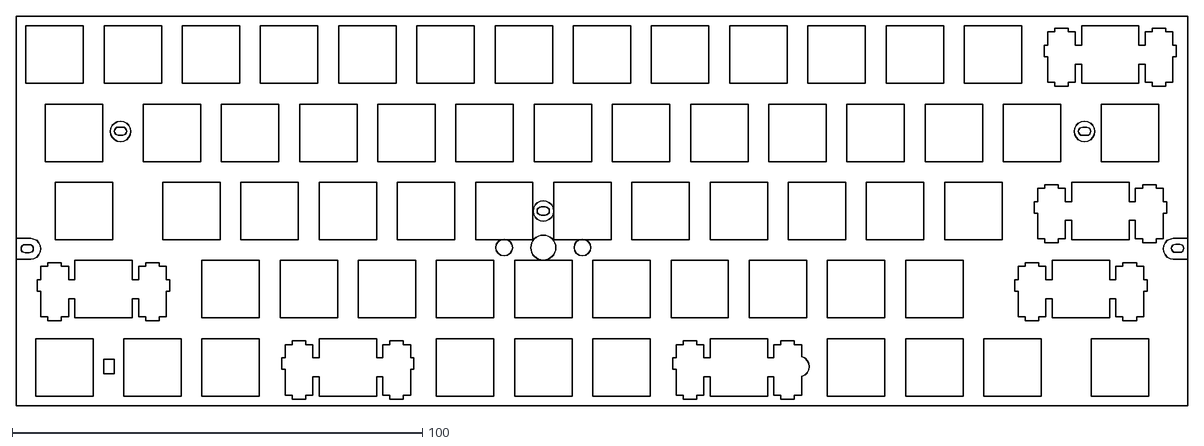
[picture p214: CAD file, 2022-12-10]
PCB/tp60/gasket/pcbV1.dxf
285.4 x 94.9
