xcl666/trackpoint-mechanical-keyboard/PCB/tpec32-main/tpec32-main/stl/rod_2.STL

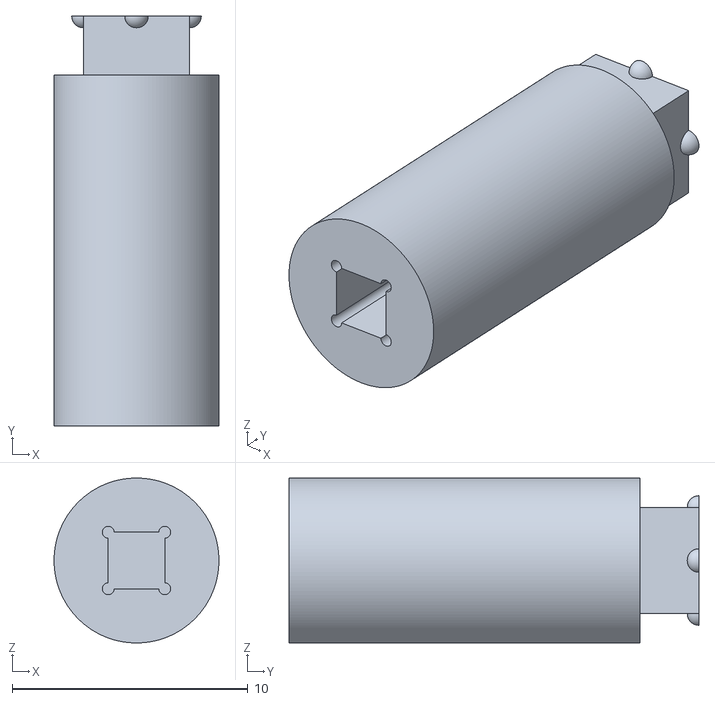
[picture p216: CAD file, 2022-12-10]
PCB/tpec32-main/tpec32-main/stl/rod_2.STL
7.00 x 17.4 x 7.00
