xcl666/trackpoint-mechanical-keyboard/PCB/tppad/3d/底壳.step

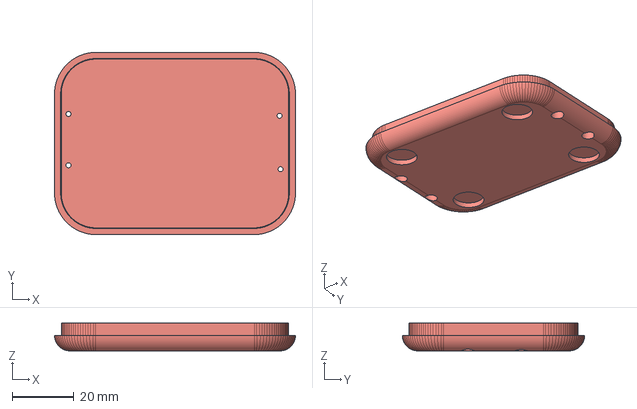
[picture p217: CAD file, 2022-12-10]
PCB/tppad/3d/底壳.step
78.2 x 59.1 x 9.00 mm
