xcl666/trackpoint-mechanical-keyboard/PCB/tppad/pcbv2with4holes.dxf

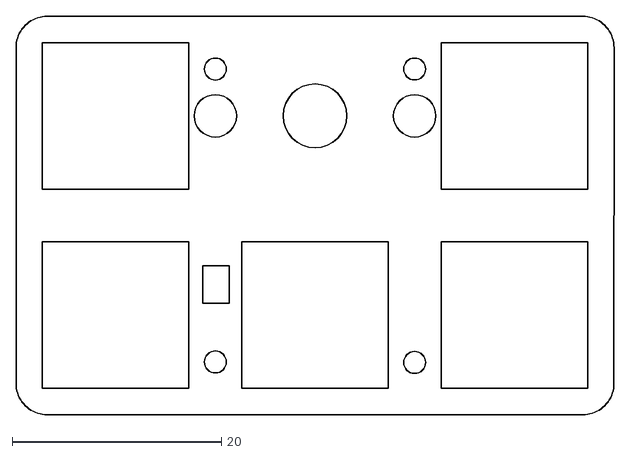
[picture p219: CAD file, 2022-12-10]
PCB/tppad/pcbv2with4holes.dxf
57.2 x 38.1
