xcl666/trackpoint-mechanical-keyboard/PCB/trackpoint/interesting/轨迹球板外壳/3个文件/3个文件/shell_1_of_鼠标底盖.stl

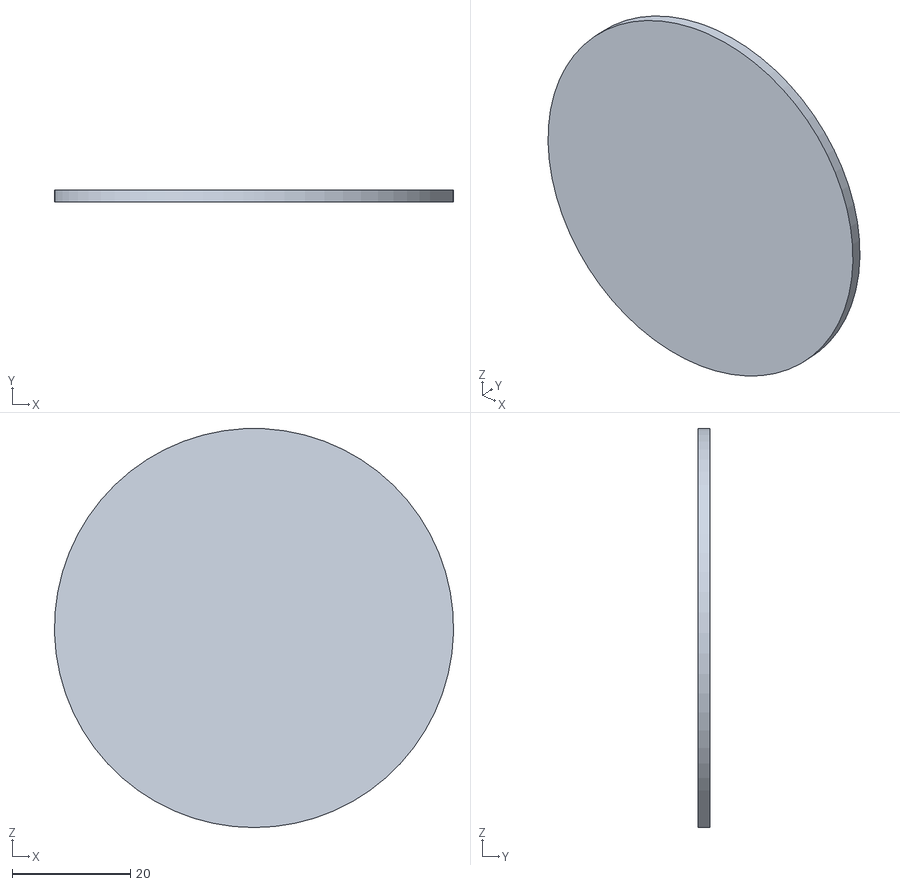
[picture p221: CAD file, 2022-12-10]
PCB/trackpoint/interesting/轨迹球板外壳/3个文件/3个文件/shell_1_of_鼠标底盖.stl
67.6 x 2.00 x 67.6
