xcl666/trackpoint-mechanical-keyboard/PCB/trackpoint/interesting/轨迹球板外壳/USB公头壳.STL

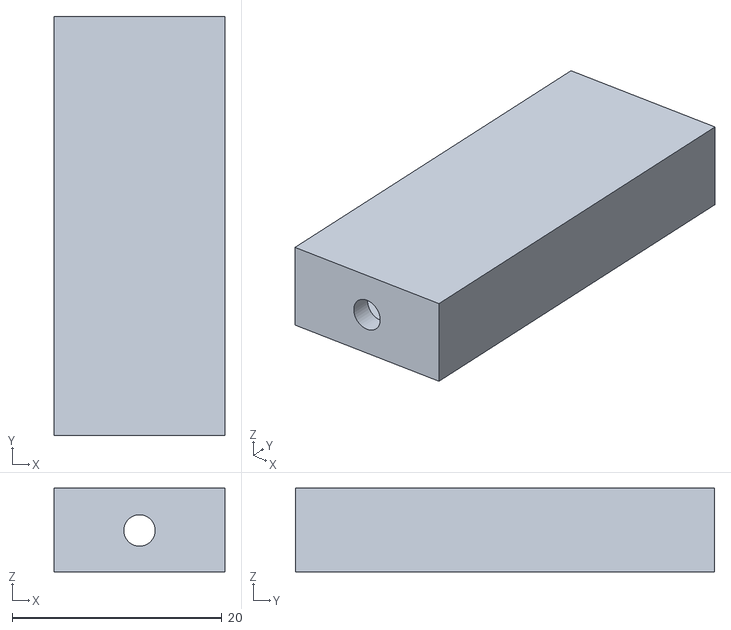
[picture p222: CAD file, 2022-12-10]
PCB/trackpoint/interesting/轨迹球板外壳/USB公头壳.STL
16.3 x 40.0 x 8.00
