xcl666/trackpoint-mechanical-keyboard/PCB/trackpoint/product/23stick.SLDPRT

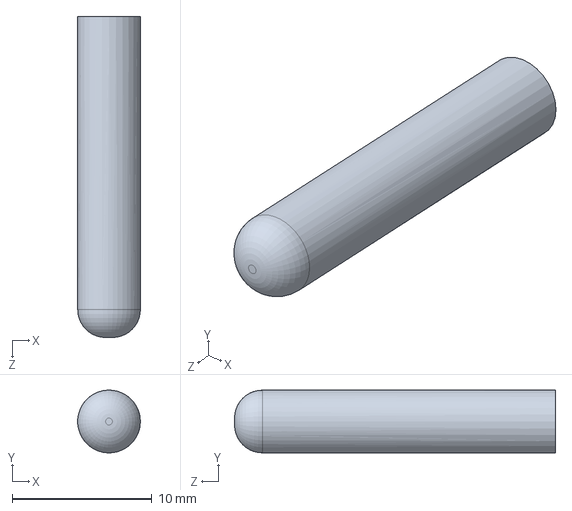
[picture p223: CAD file, 2022-12-10]
PCB/trackpoint/product/23stick.SLDPRT
4.50 x 4.50 x 23.0 mm
