xcl666/trackpoint-mechanical-keyboard/PCB/12x6/shell/open.dxf

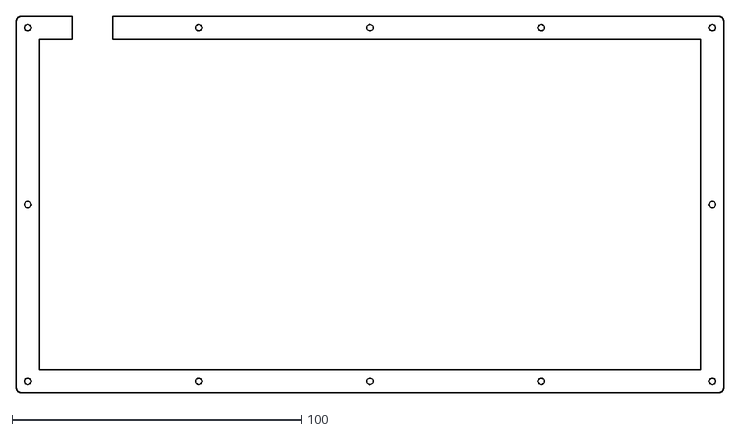
[picture p224: CAD file, 2022-12-10]
PCB/12x6/shell/open.dxf
244.6 x 130.3
