xcl666/trackpoint-mechanical-keyboard/PCB/3x10/shell/2013/bottom.dxf

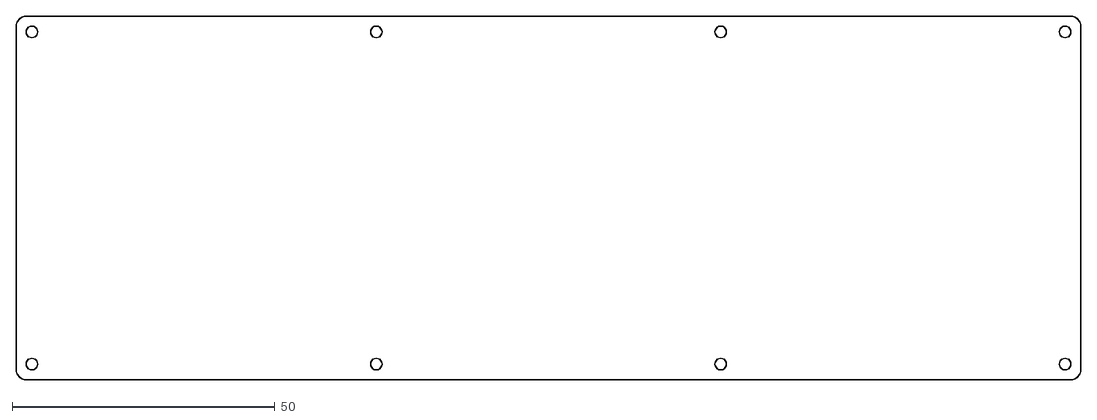
[picture p225: CAD file, 2022-12-10]
PCB/3x10/shell/2013/bottom.dxf
202.5 x 69.2
