xcl666/trackpoint-mechanical-keyboard/PCB/6x12Threekeys/open.dxf

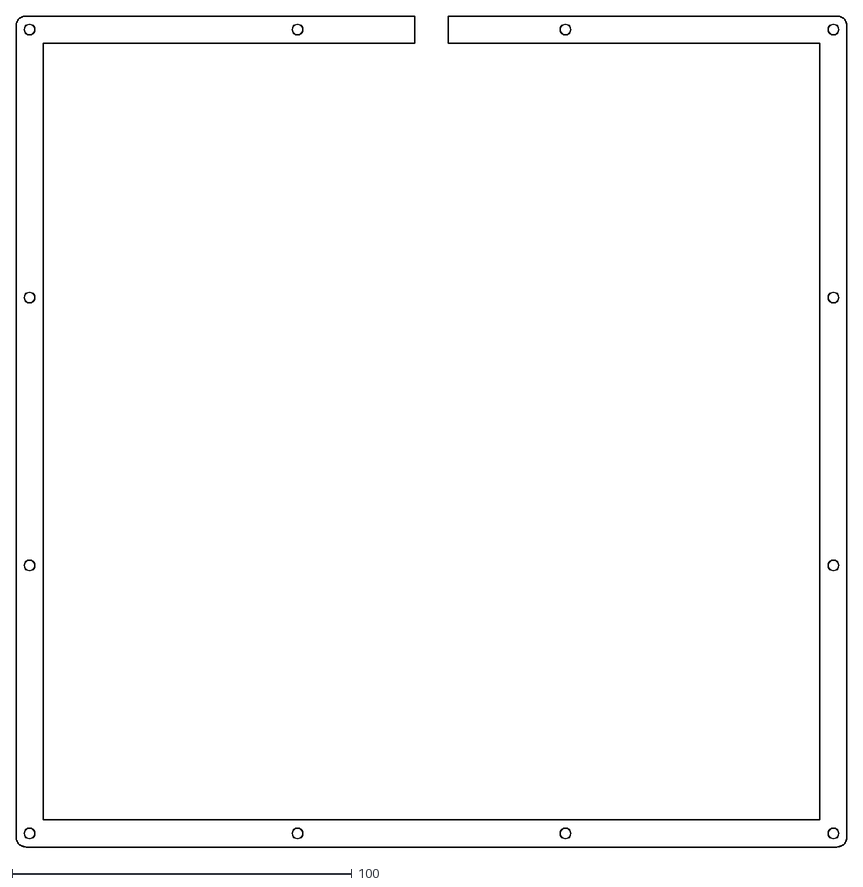
[picture p227: CAD file, 2022-12-10]
PCB/6x12Threekeys/open.dxf
244.6 x 244.6
