xcl666/trackpoint-mechanical-keyboard/PCB/alice/049ffa192bace8556d234e87433ab34e67dced8e_switchv1.dxf

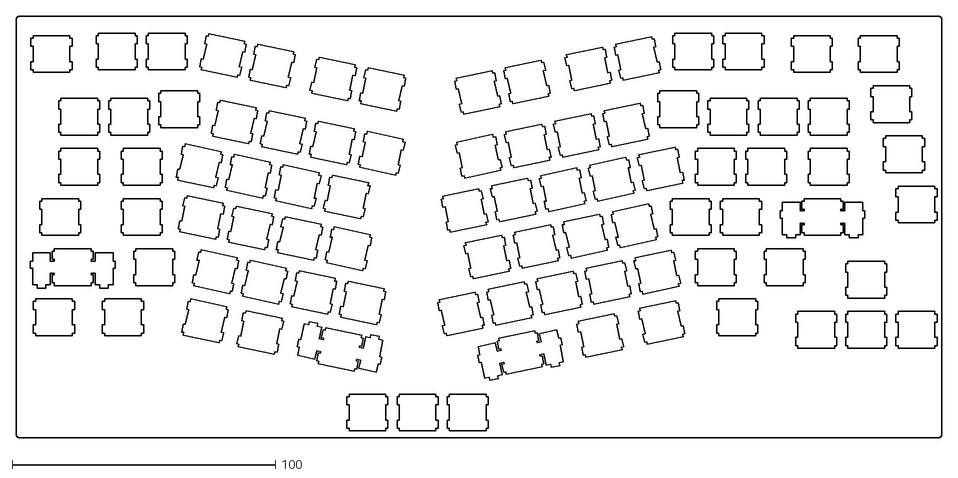
[picture p228: CAD file, 2022-12-10]
PCB/alice/049ffa192bace8556d234e87433ab34e67dced8e_switchv1.dxf
351.5 x 160.0
