xcl666/trackpoint-mechanical-keyboard/PCB/alice/3D/myown/new/底壳.SLDPRT

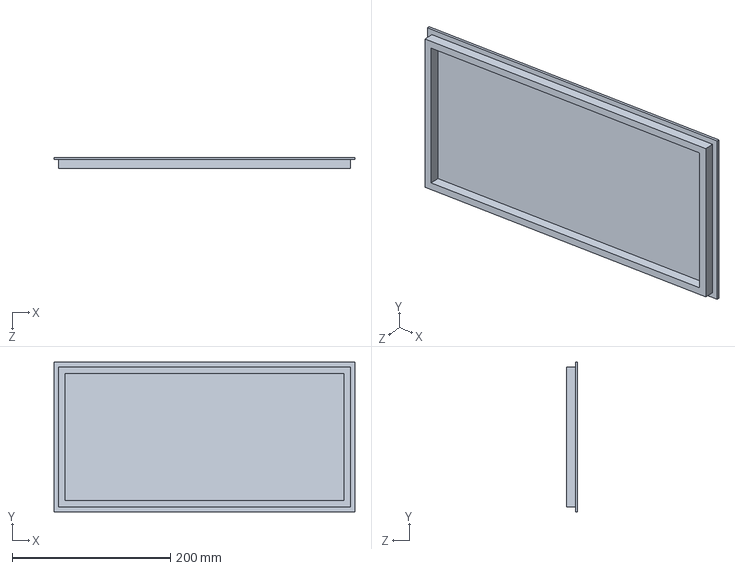
[picture p229: CAD file, 2022-12-10]
PCB/alice/3D/myown/new/底壳.SLDPRT
380.5 x 189.0 x 14.5 mm
