xcl666/trackpoint-mechanical-keyboard/PCB/alice/Kolibri/Kolibri-main/Kolibri-main/Case/07 Case top 2.dxf

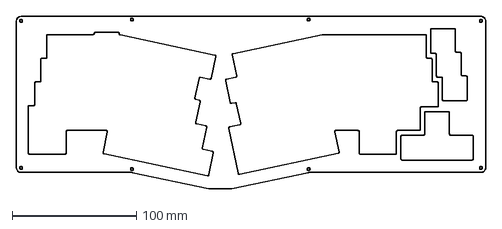
[picture p230: CAD file, 2022-12-10]
PCB/alice/Kolibri/Kolibri-main/Kolibri-main/Case/07 Case top 2.dxf
377.4 x 138.8 mm
