xcl666/trackpoint-mechanical-keyboard/PCB/think84/formal/toptestlast.dxf

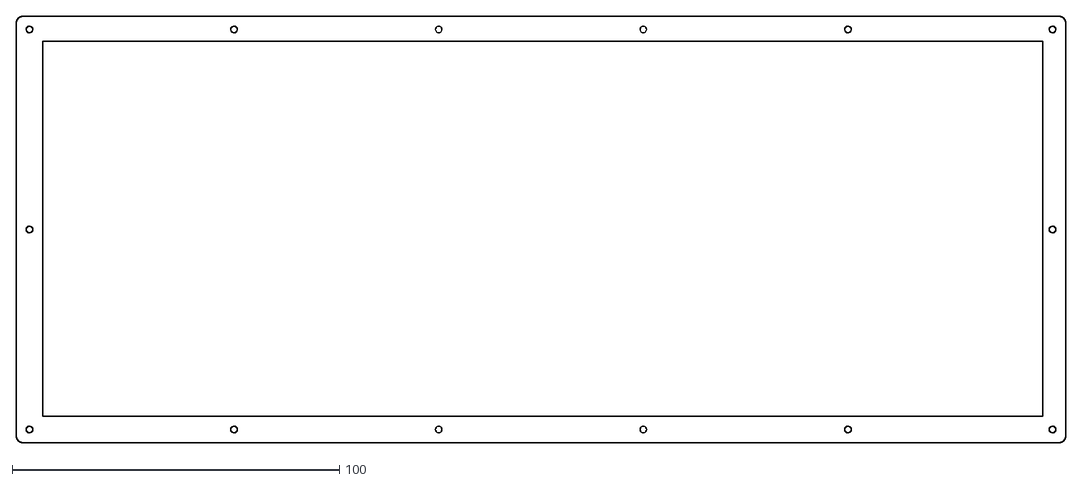
[picture p232: CAD file, 2022-12-10]
PCB/think84/formal/toptestlast.dxf
320.8 x 130.3
