xcl666/trackpoint-mechanical-keyboard/PCB/think84/plateforpc.dxf

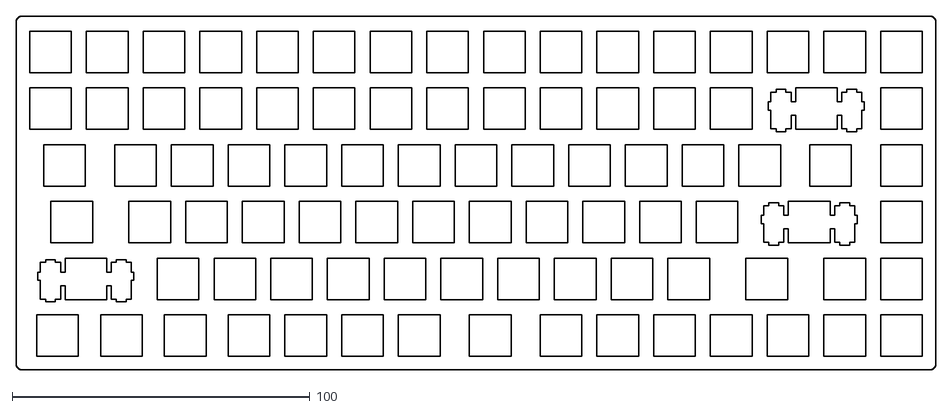
[picture p233: CAD file, 2022-12-10]
PCB/think84/plateforpc.dxf
308.8 x 118.8
