xcl666/trackpoint-mechanical-keyboard/PCB/tp60/gasket/pcbv2.dxf

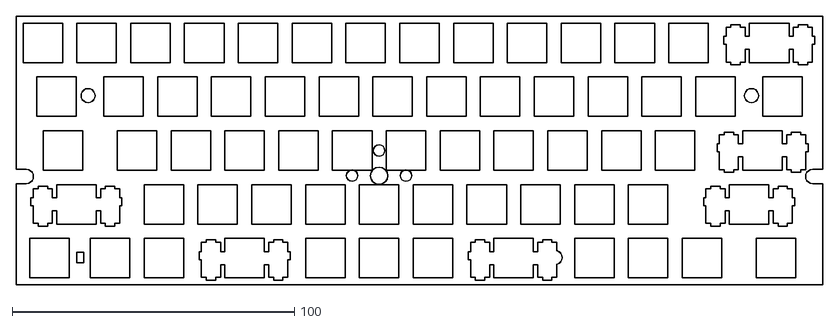
[picture p234: CAD file, 2022-12-10]
PCB/tp60/gasket/pcbv2.dxf
285.4 x 94.9
