xcl666/trackpoint-mechanical-keyboard/PCB/tp_threekeys/shell/closedV1.dxf

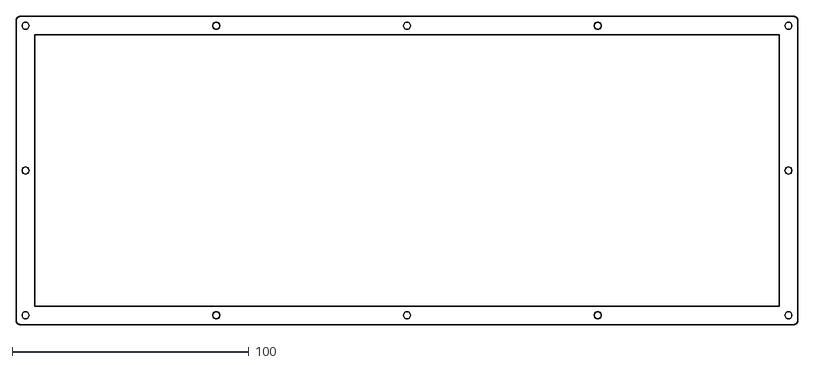
[picture p235: CAD file, 2022-12-10]
PCB/tp_threekeys/shell/closedV1.dxf
330.3 x 130.3
