xcl666/trackpoint-mechanical-keyboard/PCB/tpec32-main/tpec32-main/stl/tp_lid.STL

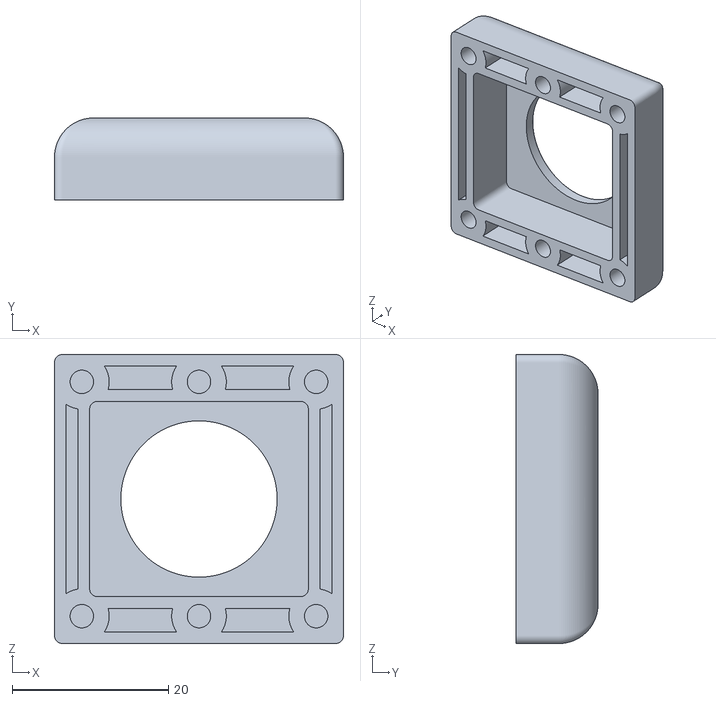
[picture p236: CAD file, 2022-12-10]
PCB/tpec32-main/tpec32-main/stl/tp_lid.STL
37.0 x 10.5 x 37.0
