xcl666/trackpoint-mechanical-keyboard/PCB/12x6/shell/closedv3.dxf

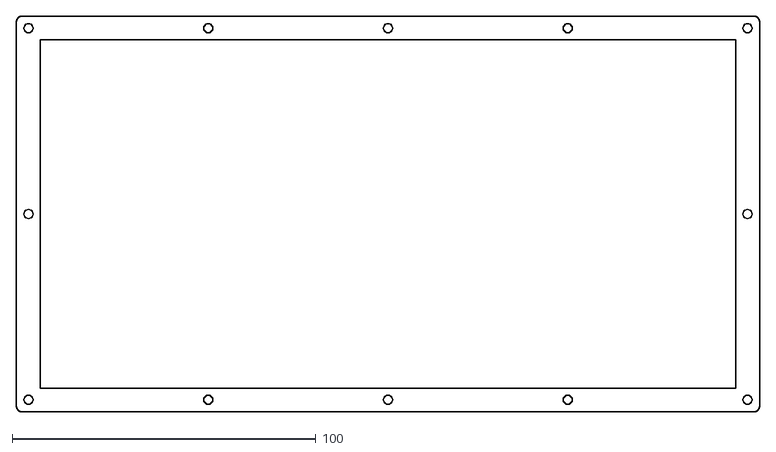
[picture p238: CAD file, 2022-12-10]
PCB/12x6/shell/closedv3.dxf
244.6 x 130.3
