xcl666/trackpoint-mechanical-keyboard/PCB/3x10/shell/78c762190a0ec8baa2587dde51f0a5da3c8a7542_switch.dxf

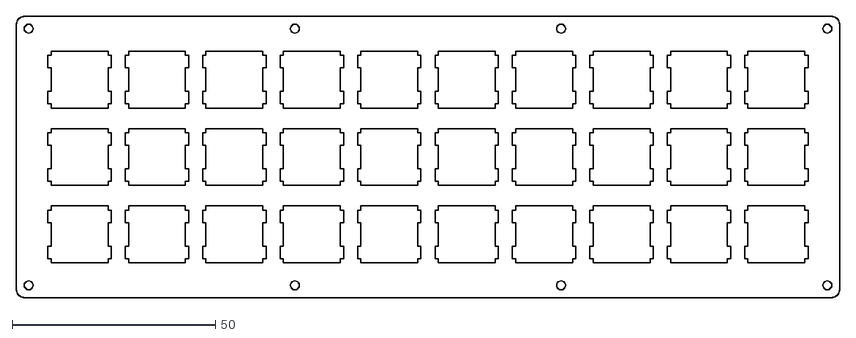
[picture p239: CAD file, 2022-12-10]
PCB/3x10/shell/78c762190a0ec8baa2587dde51f0a5da3c8a7542_switch.dxf
202.5 x 69.2
