xcl666/trackpoint-mechanical-keyboard/PCB/6x12Threekeys/closed.dxf

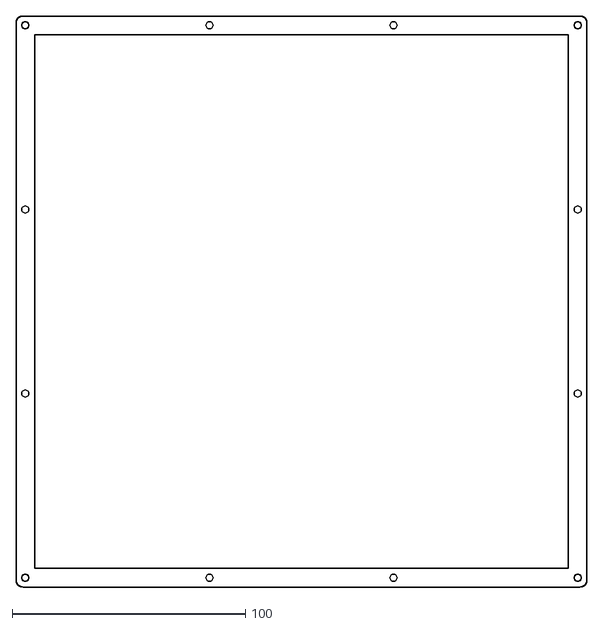
[picture p240: CAD file, 2022-12-10]
PCB/6x12Threekeys/closed.dxf
244.6 x 244.6
