xcl666/trackpoint-mechanical-keyboard/PCB/alice/3D/myown/exercise.SLDPRT

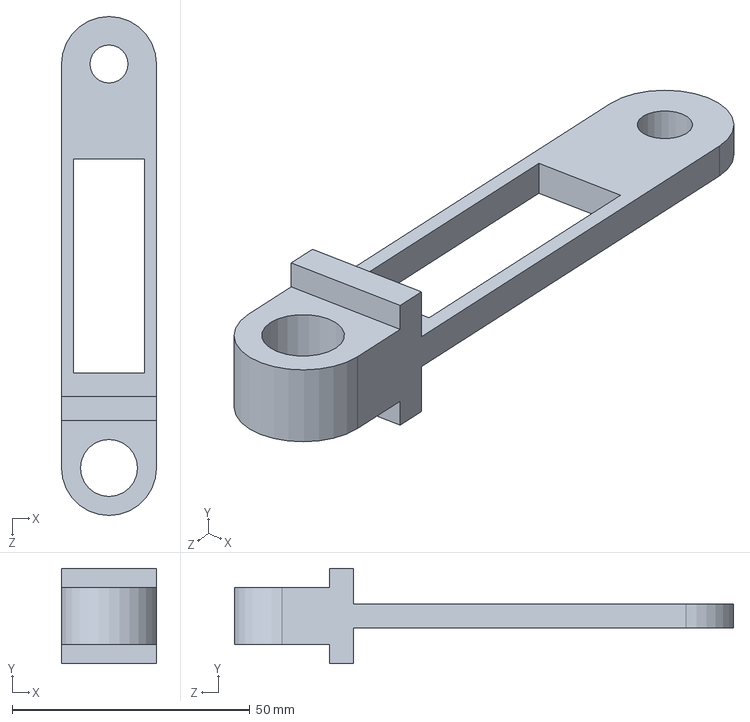
[picture p241: CAD file, 2022-12-10]
PCB/alice/3D/myown/exercise.SLDPRT
20.0 x 20.0 x 105.0 mm
