xcl666/trackpoint-mechanical-keyboard/PCB/alice/3D/myown/new/定位板.SLDPRT

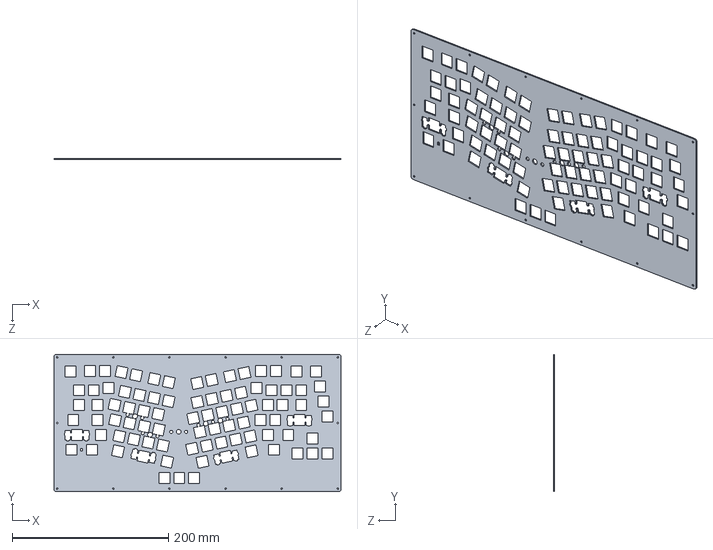
[picture p242: CAD file, 2022-12-10]
PCB/alice/3D/myown/new/定位板.SLDPRT
367.5 x 176.0 x 1.50 mm
