xcl666/trackpoint-mechanical-keyboard/PCB/alice/Kolibri/Kolibri-main/Kolibri-main/Case/06 Case top 1.dxf

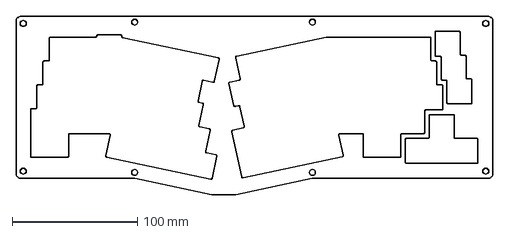
[picture p243: CAD file, 2022-12-10]
PCB/alice/Kolibri/Kolibri-main/Kolibri-main/Case/06 Case top 1.dxf
381.4 x 142.8 mm
