xcl666/trackpoint-mechanical-keyboard/PCB/alice/lastswitchV.dxf

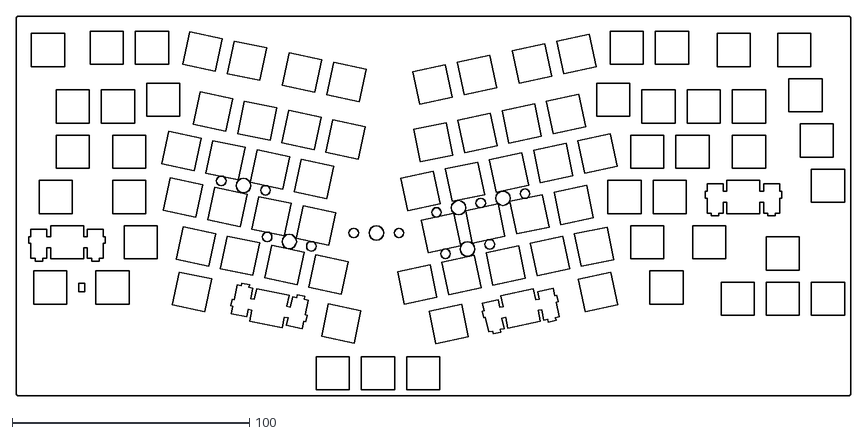
[picture p244: CAD file, 2022-12-10]
PCB/alice/lastswitchV.dxf
351.5 x 160.0
