xcl666/trackpoint-mechanical-keyboard/PCB/alice/shell/open.dxf

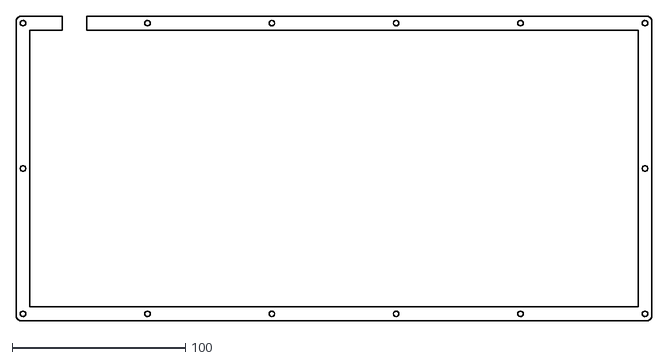
[picture p245: CAD file, 2022-12-10]
PCB/alice/shell/open.dxf
367.5 x 176.0
