xcl666/trackpoint-mechanical-keyboard/PCB/think84/formal/pcblast.dxf

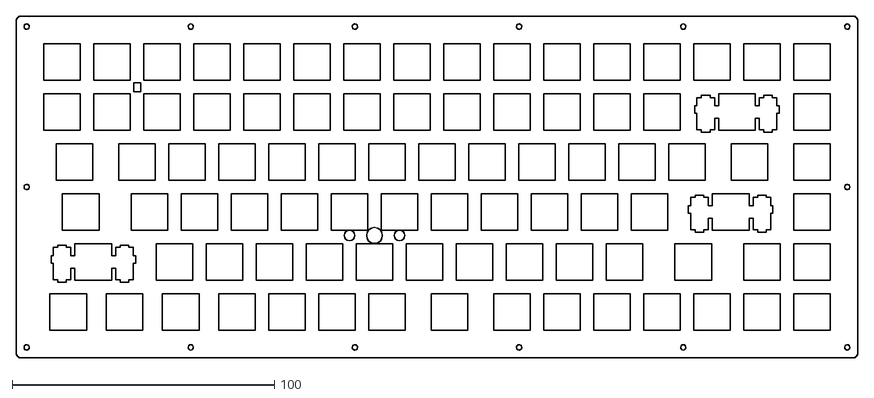
[picture p246: CAD file, 2022-12-10]
PCB/think84/formal/pcblast.dxf
320.8 x 130.3
