xcl666/trackpoint-mechanical-keyboard/PCB/tp60/gasket/closedV1.dxf

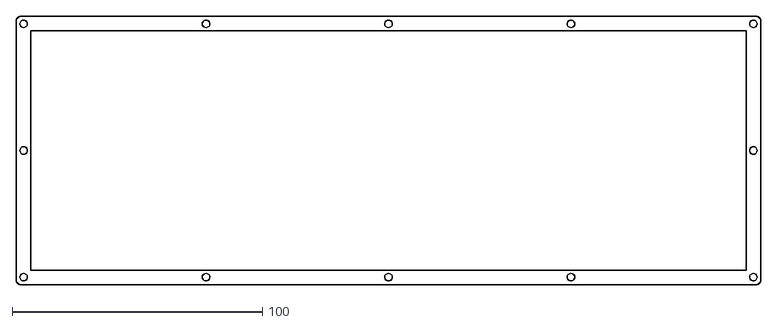
[picture p247: CAD file, 2022-12-10]
PCB/tp60/gasket/closedV1.dxf
297.8 x 107.2
