xcl666/trackpoint-mechanical-keyboard/PCB/tp_threekeys/shell/tp60switch_cherryV1.dxf

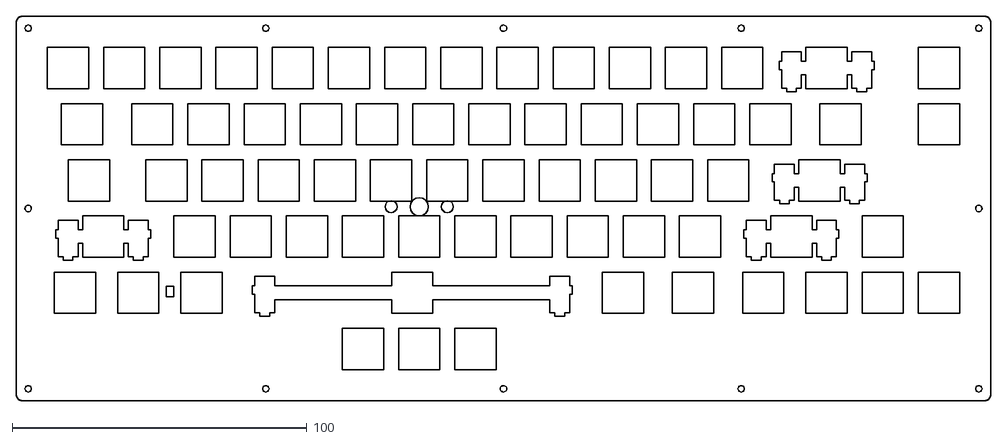
[picture p248: CAD file, 2022-12-10]
PCB/tp_threekeys/shell/tp60switch_cherryV1.dxf
330.3 x 130.3
