xcl666/trackpoint-mechanical-keyboard/PCB/tppad/3dv1/红点pad定位板V1.dxf

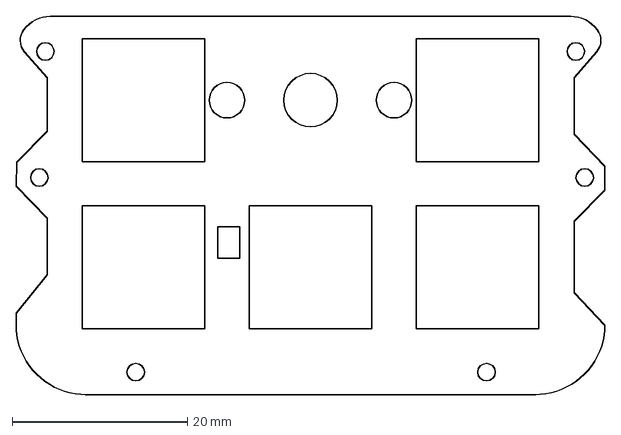
[picture p249: CAD file, 2022-12-10]
PCB/tppad/3dv1/红点pad定位板V1.dxf
67.2 x 43.1 mm
