xcl666/trackpoint-mechanical-keyboard/PCB/TP键盘升级包/TP键盘升级包/底座CAD/base_x61_d_2mm.DXF

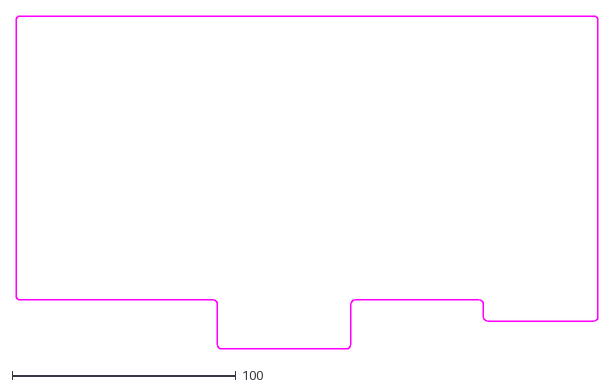
[picture p250: CAD file, 2022-12-10]
PCB/TP键盘升级包/TP键盘升级包/底座CAD/base_x61_d_2mm.DXF
260.0 x 148.7
