xcl666/trackpoint-mechanical-keyboard/PCB/alice/Kolibri/Kolibri-main/Kolibri-main/Build  guide.md

# Build guide

Connect Elite-C to computer and flash "kolibri_default.hex" firmware using qmk toolbox

Solder diodes for all keys. Black stripe on diode to square pad on pcb
<a href="https://imgur.com/B3Za0va">source: imgur.com</a>

Solder Elite-C to top side of pcb. Check that pins match. Cut off the excess legs. 
I suggest wearing eye protection and placing something to top of Elite-C when cutting excess legs. Those legs will fly.
<a href="https://imgur.com/3hRq8Ik">source: imgur.com</a>

Add rotary encoder (optional)
<a href="https://imgur.com/TNAs7En">source: imgur.com</a>

Add stabilizers 5x2U, pcb foam and FR4 plate. Check that pcb foam sits nicely and is top of gasket "wings". Place switches and solder them.
<a href="https://imgur.com/5Xc3GtY">source: imgur.com</a>
<a href="https://imgur.com/O1NoN6L">source: imgur.com</a>
<a href="https://imgur.com/JhvSGWG">source: imgur.com</a>

Solder rgb strip (optional). Check that strip is correct way (din on strip matches din text on pcb). Add soldering iron to rgb strip pins and holes at pcb. Place them closely and heat up to connect them
<a href="https://imgur.com/yCE28Dx">source: imgur.com</a>

## Case

Put screws from the bottom and add standoffs. 
<a href="https://imgur.com/UYnJwfV">source: imgur.com</a>

Add legs. I suggest using double sided tape rather than screws for better flex clearance.
<a href="https://imgur.com/Va0qu77">source: imgur.com</a>

Add case layers 2-4 and place gasket strips. Leave out middle strip if you prefer more flex
<a href="https://imgur.com/aQx9FSN">source: imgur.com</a>

Add soldered pcb. There's ~0.5mm clearance between outer sides of pcb and inner sides of case. Use your time to place the pcb so it doesn't hit side of case.
<a href="https://imgur.com/JhvSGWG">source: imgur.com</a>

Add rest of the case layers 5-7 and screw it in.
<a href="https://imgur.com/aYyIyYg">source: imgur.com</a>
