xcl666/trackpoint-mechanical-keyboard/qmk_firmware/keyboards/xcl/aurora/config.h

#ifndef CONFIG_H
#define CONFIG_H

#include "config_common.h"

/* Device */
#define VENDOR_ID       0xDE29
#define PRODUCT_ID      0x7314
#define DEVICE_VER      0x0001
#define MANUFACTURER    Leo Deng
#define PRODUCT         Aurora
#define DESCRIPTION     RGB Matrix

/* Matrix */
#define MATRIX_ROWS 3
#define MATRIX_COLS 3
#define MATRIX_ROW_PINS { D7, B5, B6 }
#define MATRIX_COL_PINS { D4, E6, B3 }
#define DIODE_DIRECTION COL2ROW // COL2ROW or ROW2COL

#define DEBOUNCE 5
#define TAP_CODE_DELAY 10
#define PREVENT_STUCK_MODIFIERS

/* RGB Matrix */
#ifdef RGB_MATRIX_ENABLE
#define DRIVER_ADDR_1 0b1110100
#define DRIVER_COUNT 1
#define DRIVER_LED_TOTAL 4

#define RGB_MATRIX_KEYPRESSES
#define RGB_MATRIX_MAXIMUM_BRIGHTNESS 200 // limits maximum brightness of LEDs to 200 out of 255. If not defined maximum brightness is set to 255
#define RGB_MATRIX_STARTUP_MODE RGB_MATRIX_CYCLE_LEFT_RIGHT // Sets the default mode, if none has been set
#define RGB_MATRIX_STARTUP_HUE 0 // Sets the default hue value, if none has been set
#define RGB_MATRIX_STARTUP_SAT 255 // Sets the default saturation value, if none has been set
#define RGB_MATRIX_STARTUP_VAL RGB_MATRIX_MAXIMUM_BRIGHTNESS // Sets the default brightness value, if none has been set
#define RGB_MATRIX_STARTUP_SPD 127 // Sets the default animation speed, if none has been set
// #define RGB_MATRIX_DISABLE_KEYCODES // disables control of rgb matrix by keycodes (must use code functions to control the feature)
// #define RGB_DISABLE_TIMEOUT 0
// #define RGB_DISABLE_AFTER_TIMEOUT 0
// #define RGB_DISABLE_WHEN_USB_SUSPENDED true
#define RGB_MATRIX_LED_PROCESS_LIMIT (DRIVER_LED_TOTAL + 4) / 5 // limits the number of LEDs to process in an animation per task run
#define RGB_MATRIX_LED_FLUSH_LIMIT 16 // limits in milliseconds how frequently an animation will update the LEDs. 16 (16ms) is equivalent to 60fps
// #define DISABLE_RGB_MATRIX_SPLASH
// #define DISABLE_RGB_MATRIX_MULTISPLASH
// #define DISABLE_RGB_MATRIX_SOLID_SPLASH
// #define DISABLE_RGB_MATRIX_SOLID_MULTISPLASH
#endif

#endif
