xcl666/trackpoint-mechanical-keyboard/qmk_firmware/keyboards/xcl/kb/config.h

#ifndef CONFIG_H
#define CONFIG_H

#include "config_common.h"

/* USB Device descriptor parameter */
#define VENDOR_ID       0xFEED
#define PRODUCT_ID      0x6060
#define DEVICE_VER      0x0001
#define MANUFACTURER    qmkbuilder
#define PRODUCT         keyboard
#define DESCRIPTION     Keyboard

/* key matrix size */
#define MATRIX_ROWS 5
#define MATRIX_COLS 4

/* key matrix pins */
#define MATRIX_ROW_PINS { F5, F4, F1, F6, F7 }
#define MATRIX_COL_PINS { B3, B2, B1, B0 }
#define ENCODERS_PAD_A { C7 }
#define ENCODERS_PAD_B { C6 }
#define ENCODER_RESOLUTION 2
#define UNUSED_PINS
/* oled显示*/


/* OLED */
#ifdef OLED_DRIVER_ENABLE
//#define OLED_BRIGHTNESS 5
#define OLED_TIMEOUT 0
//#define OLED_FONT_WIDTH 15
#endif





/* COL2ROW or ROW2COL */
#define DIODE_DIRECTION COL2ROW



/* Set 0 if debouncing isn't needed */
#define DEBOUNCING_DELAY 5

/* Mechanical locking support. Use KC_LCAP, KC_LNUM or KC_LSCR instead in keymap */
#define LOCKING_SUPPORT_ENABLE

/* Locking resynchronize hack */
#define LOCKING_RESYNC_ENABLE

/* key combination for command */
#define IS_COMMAND() ( \
    keyboard_report->mods == (MOD_BIT(KC_LSHIFT) | MOD_BIT(KC_RSHIFT)) \
)

/* prevent stuck modifiers */
#define PREVENT_STUCK_MODIFIERS

#define RGB_DI_PIN F0
#ifdef RGB_DI_PIN
#define RGBLIGHT_ANIMATIONS
#define RGBLED_NUM 6
#define RGBLIGHT_HUE_STEP 8
#define RGBLIGHT_SAT_STEP 8
#define RGBLIGHT_VAL_STEP 8
#endif

#endif
