xcl666/trackpoint-mechanical-keyboard/qmk_firmware/keyboards/xcl/lightdance/config.h

#ifndef CONFIG_H
#define CONFIG_H

#include "config_common.h"

/* Device */
#define VENDOR_ID       0xDE29
#define PRODUCT_ID      0x7309
#define DEVICE_VER      0x0001
#define MANUFACTURER    Leo Deng
#define PRODUCT         Lightdance
#define DESCRIPTION     Test with light and audio effects

/* DFU */
#define QMK_ESC_INPUT D4  // usually ROW
#define QMK_ESC_OUTPUT F6 // usually COL
#define QMK_LED D2

/* Command */
#define IS_COMMAND() ( keyboard_report->mods == (MOD_BIT(KC_LSHIFT) | MOD_BIT(KC_RSHIFT)) )

/* Matrix */
#define MATRIX_ROWS 5
#define MATRIX_COLS 5
#define MATRIX_ROW_PINS { D4, C6, D7, E6, B4 }
#define MATRIX_COL_PINS { F6, F7, B1, B3, B2 }
#define DIODE_DIRECTION COL2ROW // COL2ROW or ROW2COL

#define DEBOUNCE 5
#define TAP_CODE_DELAY 10
#define PREVENT_STUCK_MODIFIERS

/* LED Indicators */
#define LED_CAPS_LOCK_PIN D2
#define LED_PIN_ON_STATE 1

/* WS2812 RGB */
#define RGB_DI_PIN F4
#define RGBLED_NUM 3
#define RGBLIGHT_ANIMATIONS
#define RGBLIGHT_HUE_STEP 8
#define RGBLIGHT_SAT_STEP 8
#define RGBLIGHT_VAL_STEP 8
#define RGBLIGHT_LAYERS
#define RGBLIGHT_LAYER_BLINK
#define RGBLIGHT_LAYERS_OVERRIDE_RGB_OFF

#endif
