xcl666/trackpoint-mechanical-keyboard/qmk_firmware/keyboards/xcl/kb1/config.h

#ifndef CONFIG_H
#define CONFIG_H

#include "config_common.h"

/* USB Device descriptor parameter */
#define VENDOR_ID       0xFEED
#define PRODUCT_ID      0x6060
#define DEVICE_VER      0x0001
#define MANUFACTURER    dztech
#define PRODUCT         hhkb40
#define DESCRIPTION     Keyboard

/* key matrix size */
#define MATRIX_ROWS 4
#define MATRIX_COLS 13

/* key matrix pins */
#define MATRIX_ROW_PINS { E6, B6, B5, B4 }
#define MATRIX_COL_PINS { D3, F7, F6, F5, F4, F1, F0, B0, C7, C6, D7, D6, D5 }
#define UNUSED_PINS

/* COL2ROW or ROW2COL */
#define DIODE_DIRECTION COL2ROW

/* number of backlight levels */

#ifdef BACKLIGHT_PIN
#define BACKLIGHT_LEVELS 3
#endif

/* Set 0 if debouncing isn't needed */
#define DEBOUNCE 5

/* Mechanical locking support. Use KC_LCAP, KC_LNUM or KC_LSCR instead in keymap */
#define LOCKING_SUPPORT_ENABLE

/* Locking resynchronize hack */
#define LOCKING_RESYNC_ENABLE



#ifdef RGB_DI_PIN
#define RGBLIGHT_ANIMATIONS

#define RGBLED_NUM 44
#define RGBLIGHT_HUE_STEP 8
#define RGBLIGHT_SAT_STEP 8
#define RGBLIGHT_VAL_STEP 8
#define RGBLIGHT_SLEEP
#define RGBLIGHT_LIMIT_VAL undefined
#endif

#endif
