xcl666/trackpoint-mechanical-keyboard/qmk_firmware/keyboards/xcl/prototype/config.h

#ifndef CONFIG_H
#define CONFIG_H

#include "config_common.h"

/* Device */
#define VENDOR_ID       0xDE29
#define PRODUCT_ID      0x7301
#define DEVICE_VER      0x0001
#define MANUFACTURER    Leo Deng
#define PRODUCT         Prototype
#define DESCRIPTION     Pro Micro driven 40% keyboard

/* Command */
#define IS_COMMAND() ( keyboard_report->mods == (MOD_BIT(KC_LSHIFT) | MOD_BIT(KC_RSHIFT)) )

/* Matrix */
#define MATRIX_ROWS 4
#define MATRIX_COLS 12
#define MATRIX_ROW_PINS { D1, D0, D4, C6 }
#define MATRIX_COL_PINS { D7, E6, B4, B5, B6, B2, B3, B1, F7, F6, F5, F4 }
#define DIODE_DIRECTION ROW2COL // COL2ROW or ROW2COL

#define DEBOUNCE 5
#define TAP_CODE_DELAY 10
#define PREVENT_STUCK_MODIFIERS

#endif
