xcl666/trackpoint-mechanical-keyboard/qmk_firmware/keyboards/xcl/328p/328p.h

#pragma once

#include "quantum.h"

// Indication LED settings
#define LED_ON  2
#define LED_DIM 1
#define LED_OFF 0

#define GPIO_STATE_LOW  0
#define GPIO_STATE_HIGH 1

#define PIN_LED B2

void set_scramble_LED(uint8_t mode);

#define LAYOUT( \
  K01, K02, K03, \
  K11, K12, K13  \
) { \
  { K01, K02, K03 }, \
  { K11, K12, K13 }, \
}
