xcl666/trackpoint-mechanical-keyboard/qmk_firmware/keyboards/xcl/redox/keymaps/default/keymap.c

#include "redox.h"

const uint16_t PROGMEM keymaps[][MATRIX_ROWS][MATRIX_COLS] = {

  [0] = LAYOUT(
  //┌─────────┬─────────┬─────────┬─────────┬─────────┬─────────┐                                              ┌─────────┬─────────┬─────────┬─────────┬─────────┬─────────┐
      KC_ESC  , KC_1    , KC_2    , KC_3    , KC_4    , KC_5    ,                                                KC_6    , KC_7    , KC_8    , KC_9    , KC_0    , KC_BSPC ,
  //├─────────┼─────────┼─────────┼─────────┼─────────┼─────────┼─────────┐                          ┌─────────┼─────────┼─────────┼─────────┼─────────┼─────────┼─────────┤
      KC_TAB  , KC_Q    , KC_W    , KC_E    , KC_R    , KC_T    , KC_MINS ,                            KC_LBRC , KC_Y    , KC_U    , KC_I    , KC_O    , KC_P    , KC_BSLS ,
  //├─────────┼─────────┼─────────┼─────────┼─────────┼─────────┼─────────┤                          ├─────────┼─────────┼─────────┼─────────┼─────────┼─────────┼─────────┤
      KC_CAPS , KC_A    , KC_S    , KC_D    , KC_F    , KC_G    , KC_EQL  ,                            KC_RBRC , KC_H    , KC_J    , KC_K    , KC_L    , KC_SCLN , KC_QUOT ,
  //├─────────┼─────────┼─────────┼─────────┼─────────┼─────────┼─────────┼─────────┐      ┌─────────┼─────────┼─────────┼─────────┼─────────┼─────────┼─────────┼─────────┤
      KC_LSFT , KC_Z    , KC_X    , KC_C    , KC_V    , KC_B    , KC_PGUP , KC_PGDN ,        KC_HOME , KC_END  , KC_N    , KC_M    , KC_COMM , KC_DOT  , KC_SLSH , KC_RSFT ,
  //├─────────┼─────────┼─────────┼─────────┼────┬────┴────┬────┼─────────┼─────────┤      ├─────────┼─────────┼───┬─────┴───┬─────┼─────────┼─────────┼─────────┼─────────┤
      KC_LCTL , KC_LGUI , KC_LALT , KC_APP  ,      MO(1)   ,      KC_LSFT , KC_SPC  ,        KC_ENT  , KC_RSFT ,     MO(2)   ,       KC_LEFT , KC_DOWN , KC_UP   , KC_RGHT
  //└─────────┴─────────┴─────────┴─────────┘    └─────────┘    └─────────┴─────────┘      └─────────┴─────────┘   └─────────┘     └─────────┴─────────┴─────────┴─────────┘
  ),

  [1] = LAYOUT(
  //┌─────────┬─────────┬─────────┬─────────┬─────────┬─────────┐                                              ┌─────────┬─────────┬─────────┬─────────┬─────────┬─────────┐
      _______ , _______ , _______ , _______ , _______ , _______ ,                                                _______ , _______ , _______ , _______ , _______ , _______ ,
  //├─────────┼─────────┼─────────┼─────────┼─────────┼─────────┼─────────┐                          ┌─────────┼─────────┼─────────┼─────────┼─────────┼─────────┼─────────┤
      _______ , KC_VOLU , KC_F1   , KC_F2   , KC_F3   , KC_F4   , _______ ,                            _______ , KC_PPLS , KC_PMNS , KC_PAST , KC_PSLS , _______ , _______ ,
  //├─────────┼─────────┼─────────┼─────────┼─────────┼─────────┼─────────┤                          ├─────────┼─────────┼─────────┼─────────┼─────────┼─────────┼─────────┤
      _______ , KC_VOLD , KC_F5   , KC_F6   , KC_F7   , KC_F8   , _______ ,                            _______ , KC_PSCR , KC_SLCK , KC_PAUS , _______ , _______ , _______ ,
  //├─────────┼─────────┼─────────┼─────────┼─────────┼─────────┼─────────┼─────────┐      ┌─────────┼─────────┼─────────┼─────────┼─────────┼─────────┼─────────┼─────────┤
      _______ , KC_MUTE , KC_F9   , KC_F10  , KC_F11  , KC_F12  , _______ , _______ ,        _______ , _______ , KC_INS  , KC_DEL  , _______ , _______ , _______ , _______ ,
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
  )

};

void led_set_user(uint8_t usb_led) {
  if (usb_led & (1 << USB_LED_CAPS_LOCK)) {
    DDRD |= (1 << 5); PORTD &= ~(1 << 5);
  } else {
    DDRD &= ~(1 << 5); PORTD &= ~(1 << 5);
  }
};
