xcl666/trackpoint-mechanical-keyboard/qmk_firmware/keyboards/xcl/plancky3/keymaps/default/keymap.c

#include "plancky3.h"

const uint16_t PROGMEM keymaps[][MATRIX_ROWS][MATRIX_COLS] = {

  [0] = LAYOUT(
    KC_ESC,  KC_Q,    KC_W,    KC_E,    KC_R,    KC_T,    KC_Y,    KC_U,    KC_I,    KC_O,    KC_P,    KC_BSPC,
    KC_TAB,  KC_A,    KC_S,    KC_D,    KC_F,    KC_G,    KC_H,    KC_J,    KC_K,    KC_L,    KC_BSLS, KC_ENT,
    KC_LSFT, KC_Z,    KC_X,    KC_C,    KC_V,    KC_B,    KC_N,    KC_M,    KC_COMM, KC_DOT,  KC_SLSH, KC_RSFT,
    KC_CAPS, KC_LCTL, KC_LGUI, KC_LALT, LT(2, KC_SPC),    LT(1, KC_SPC),    KC_LEFT, KC_DOWN, KC_UP,   KC_RGHT),

  [1] = LAYOUT(
    KC_GRV,  KC_1,    KC_2,    KC_3,    KC_4,    KC_5,    KC_6,    KC_7,    KC_8,    KC_9,    KC_0,    KC_TRNS,
    KC_TRNS, KC_INS,  KC_HOME, KC_PGUP, KC_TRNS, KC_TRNS, KC_MINS, KC_EQL,  KC_LBRC, KC_RBRC, KC_TRNS, KC_TRNS,
    KC_TRNS, KC_DEL,  KC_END,  KC_PGDN, KC_TRNS, KC_TRNS, KC_SCLN, KC_QUOT, KC_TRNS, KC_TRNS, KC_TRNS, KC_TRNS,
    KC_TRNS, KC_TRNS, KC_TRNS, KC_TRNS,       RESET,           KC_TRNS,     KC_TRNS, KC_TRNS, KC_TRNS, KC_TRNS),

  [2] = LAYOUT(
    KC_F1,   KC_F2,   KC_F3,   KC_F4,   KC_F5,   KC_F6,   KC_F7,   KC_F8,   KC_F9,   KC_F10,  KC_F11,  KC_F12,
    KC_TRNS, KC_TRNS, KC_TRNS, KC_TRNS, KC_TRNS, KC_TRNS, KC_TRNS, KC_BRID, KC_BRIU, KC_TRNS, KC_TRNS, KC_TRNS,
    KC_TRNS, KC_PSCR, KC_SLCK, KC_PAUS, KC_TRNS, KC_TRNS, KC_MUTE, KC_VOLD, KC_VOLU, KC_TRNS, KC_TRNS, KC_TRNS,
    KC_TRNS, KC_TRNS, KC_TRNS, KC_TRNS,      KC_TRNS,           RESET,      KC_TRNS, KC_TRNS, KC_TRNS, KC_TRNS),

  [3] = LAYOUT(
    KC_NO,   KC_NO,   KC_NO,   KC_NO,   KC_NO,   KC_NO,   KC_NO,   KC_NO,   KC_NO,   KC_NO,   KC_NO,   KC_NO,
    KC_NO,   KC_NO,   KC_NO,   KC_NO,   KC_NO,   KC_NO,   KC_NO,   KC_NO,   KC_NO,   KC_NO,   KC_NO,   KC_NO,
    KC_NO,   KC_NO,   KC_NO,   KC_NO,   KC_NO,   KC_NO,   KC_NO,   KC_NO,   KC_NO,   KC_NO,   KC_NO,   KC_NO,
    KC_NO,   KC_NO,   KC_NO,   KC_NO,        KC_NO,            KC_NO,       KC_NO,   KC_NO,   KC_NO,   KC_NO)

};

const macro_t *action_get_macro(keyrecord_t *record, uint8_t id, uint8_t opt) {
  switch (id) {}
  return MACRO_NONE;
}

void matrix_init_user(void) {}

void matrix_scan_user(void) {}

bool process_record_user(uint16_t keycode, keyrecord_t *record) {
  return true;
}

void led_set_user(uint8_t usb_led) {
  if (usb_led & (1 << USB_LED_CAPS_LOCK)) {
    DDRD |= (1 << 2); PORTD &= ~(1 << 2);
  } else {
    DDRD &= ~(1 << 2); PORTD &= ~(1 << 2);
  }
}
